foxostro/Turtle16/Hardware/Archive/MEMModule_Rev_C_1e01d7a2/MEMModule (Rev C).pdf

Id: 1/14 Title: Turtle16: MEM, RAM, ROM

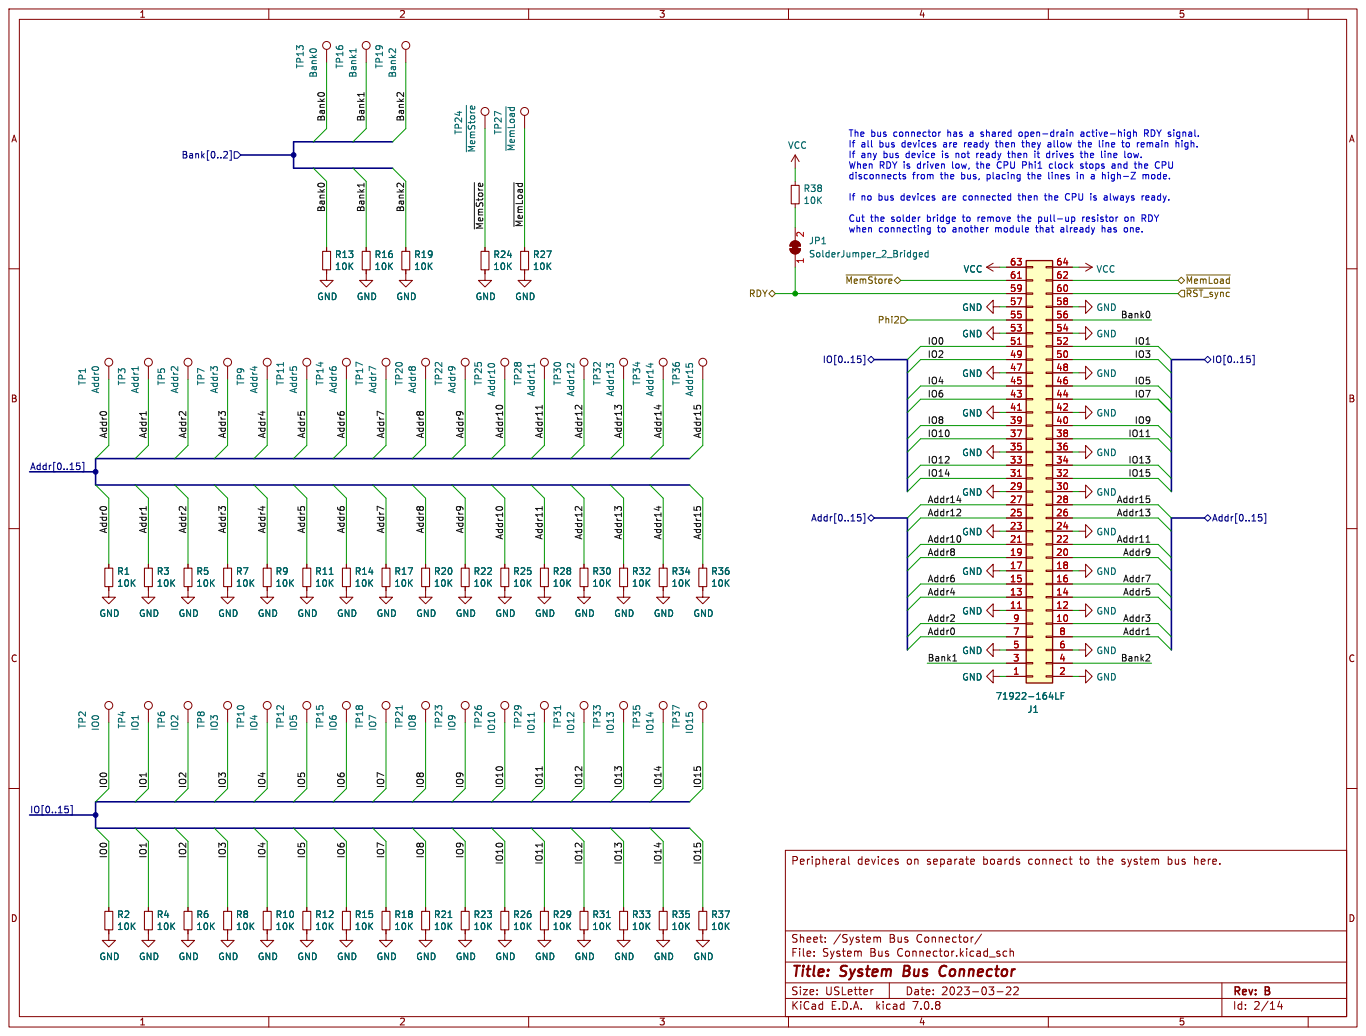
[picture p56: page 2]

If all bus devices are ready then they allow the line to remain high.
If any bus device is not ready then it drives the line low. When RDY is driven low, the CPU Phi1 clock stops and the CPU

VCC GND GND GND GND
9 GND GND GND GND

GND GND

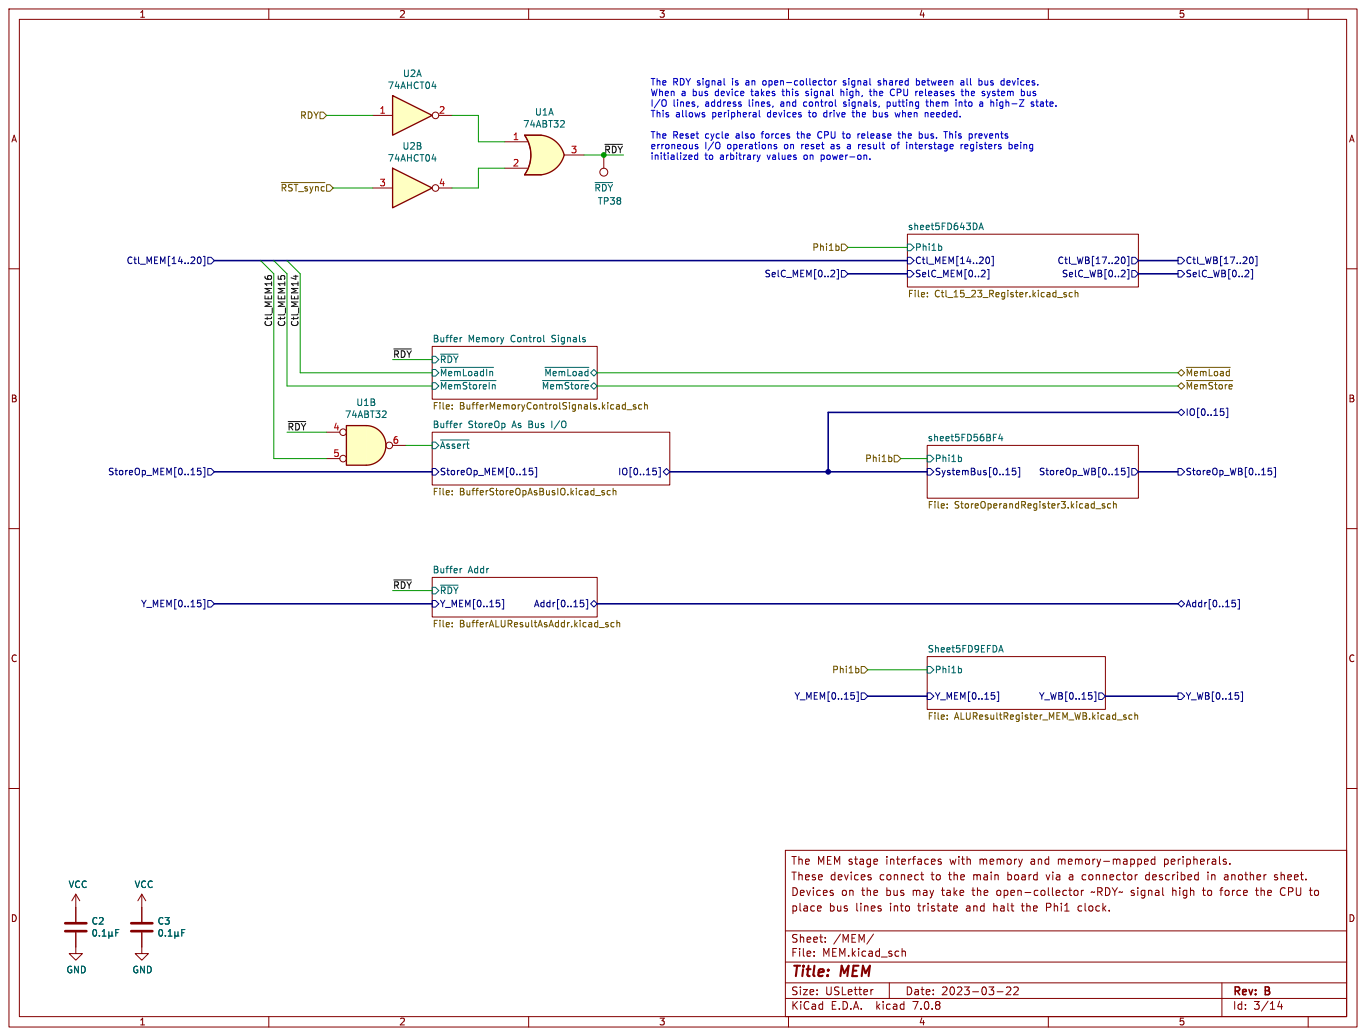
[picture p57: page 3]

~{RDY} Buffer Memory Control Signals File: BufferMemoryControlSignals.kicad_sch

~{Assert} Buffer StoreOp As Bus I/O

þÿ0.1¼F GND VCC 14 GND


74AHCT245 VCC GND GND GND


Id: 5/14 Title: MEM: Buffer StoreOp



Id: 7/14 Title: MEM/WB: Control Word Register File: Ctl_15_23_Register.kicad_sch Sheet: /MEM/sheet5FD643DA/



VCC GND VCC GND GND GND GND

If the IF stage is not being fed by ROM then it is being fed by RAM.

File: RAM.kicad_sch Sheet: /Memory/RAM/
Id: 9/14 Title: Turtle16: RAM


File: ALUResultRegister_MEM_WB.kicad_sch Sheet: /MEM/Sheet5FD9EFDA/ GND

Id: 10/14 Title: ALU Result Register MEM/WB


Id: 11/14 Title: Turtle16: MEM Prototype Inputs

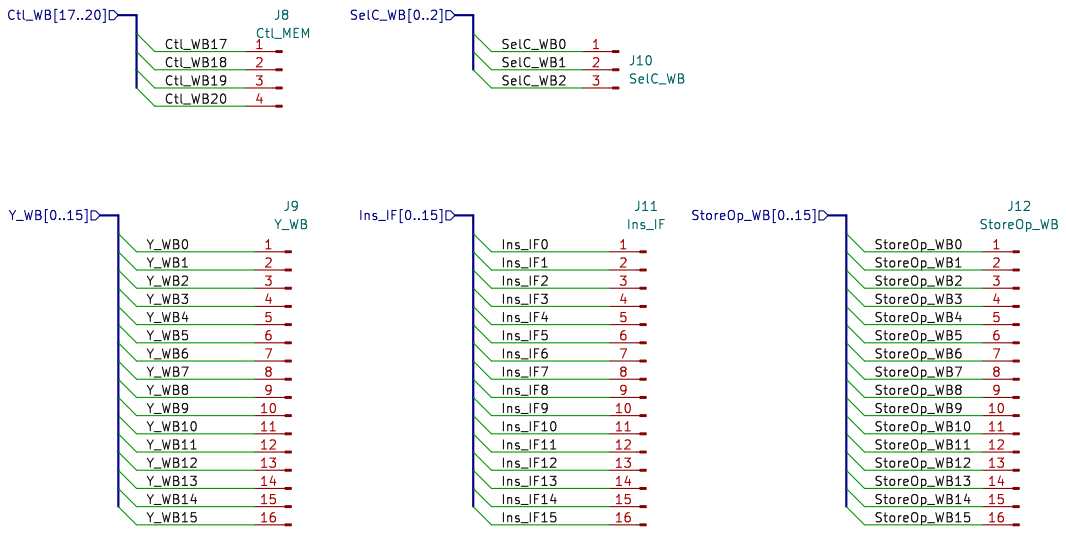
[picture p58: page 12]

Id: 12/14 Title: Turtle16: MEM Prototype Outputs

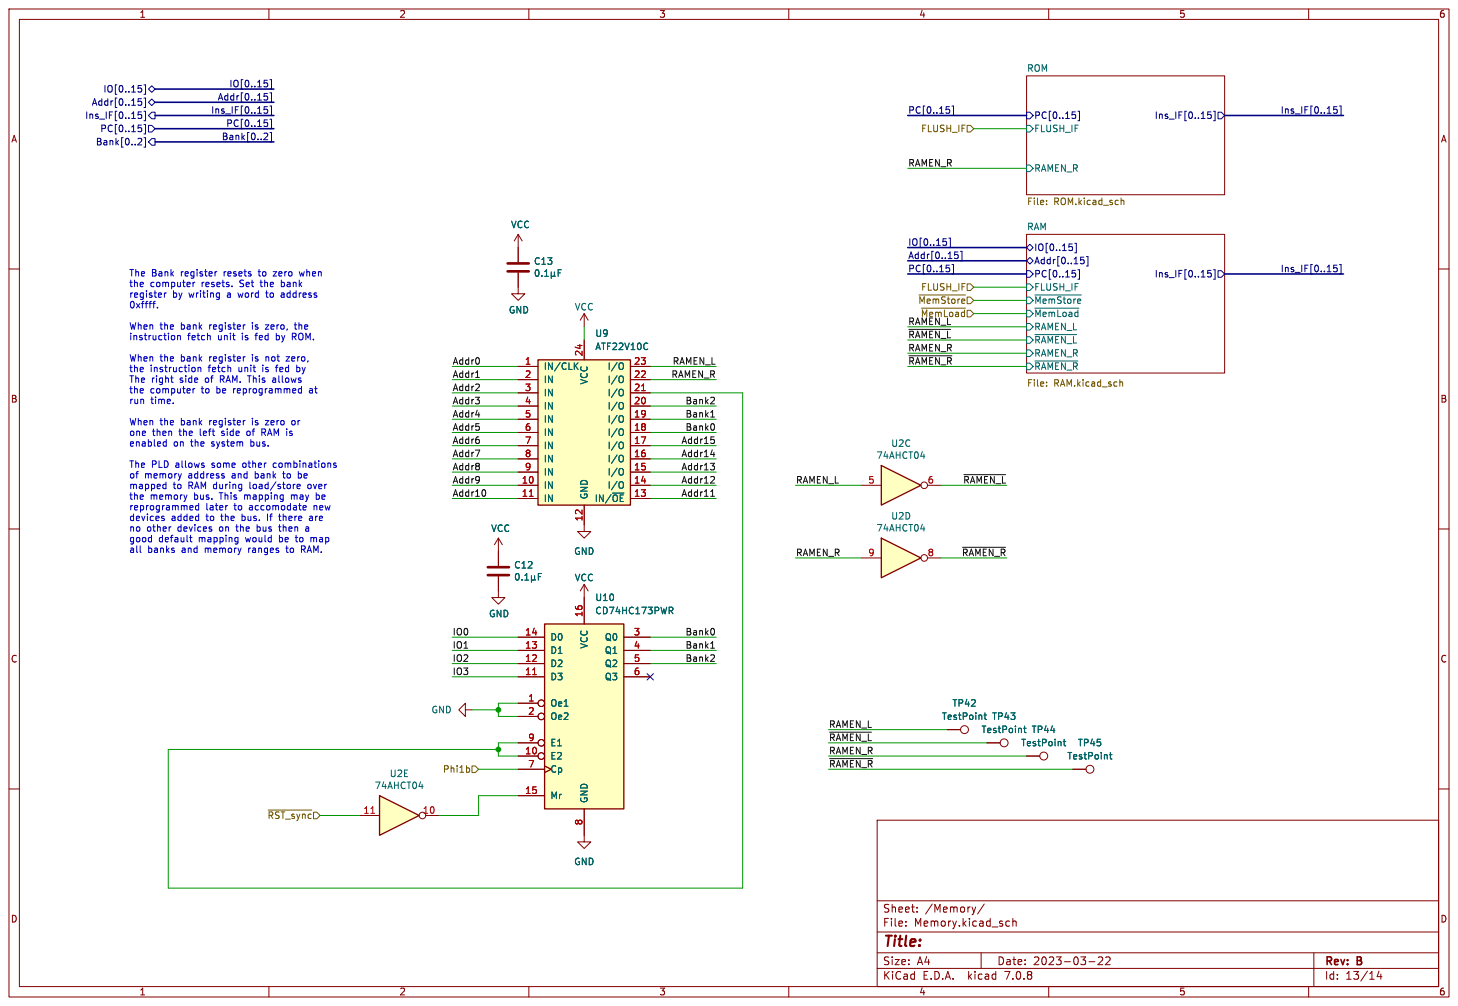
[picture p59: page 13]

8 E1 9 U10 CD74HC173PWR GND TP43 TestPoint TP42 TestPoint TP44 TestPoint TP45 TestPoint 5 6 U2C

the memory bus. This mapping may be
devices added to the bus. If there are
no other devices on the bus then a

Id: 13/14 Title: File: Memory.kicad_sch Sheet: /Memory/

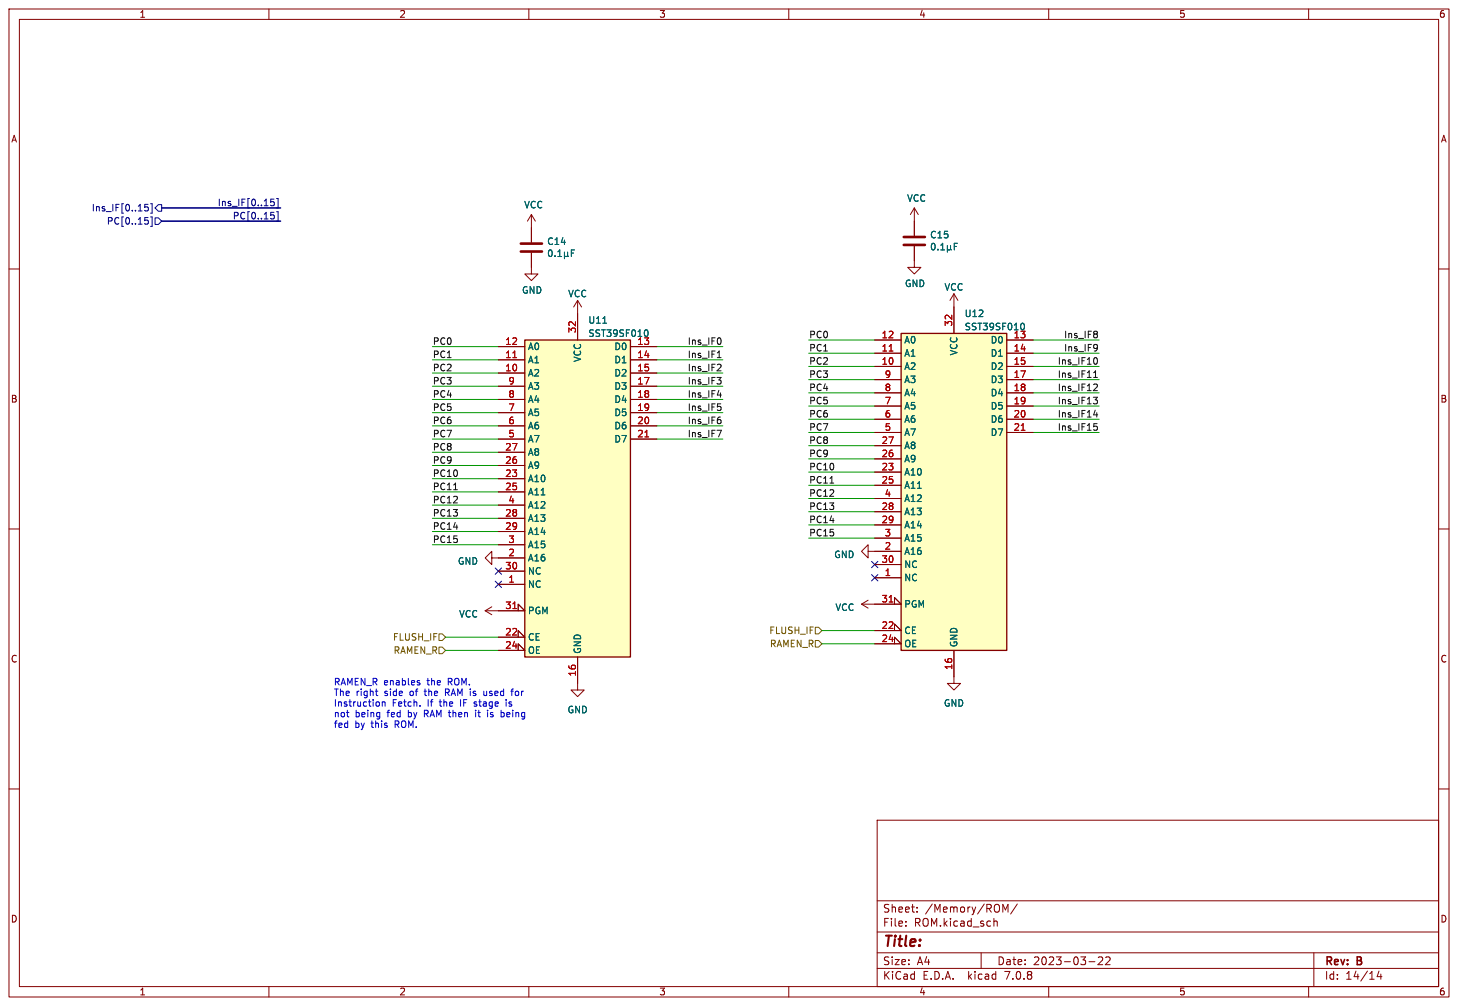
[picture p60: page 14]

fed by this ROM.

Id: 14/14 Title: File: ROM.kicad_sch Sheet: /Memory/ROM/
