foxostro/Turtle16/Hardware/PrototypeProcessor/BypassModule/BypassModule.kicad_pcb

## KiCad design Hardware/PrototypeProcessor/BypassModule/BypassModule.kicad_pcb (2025-06-30, an earlier design)

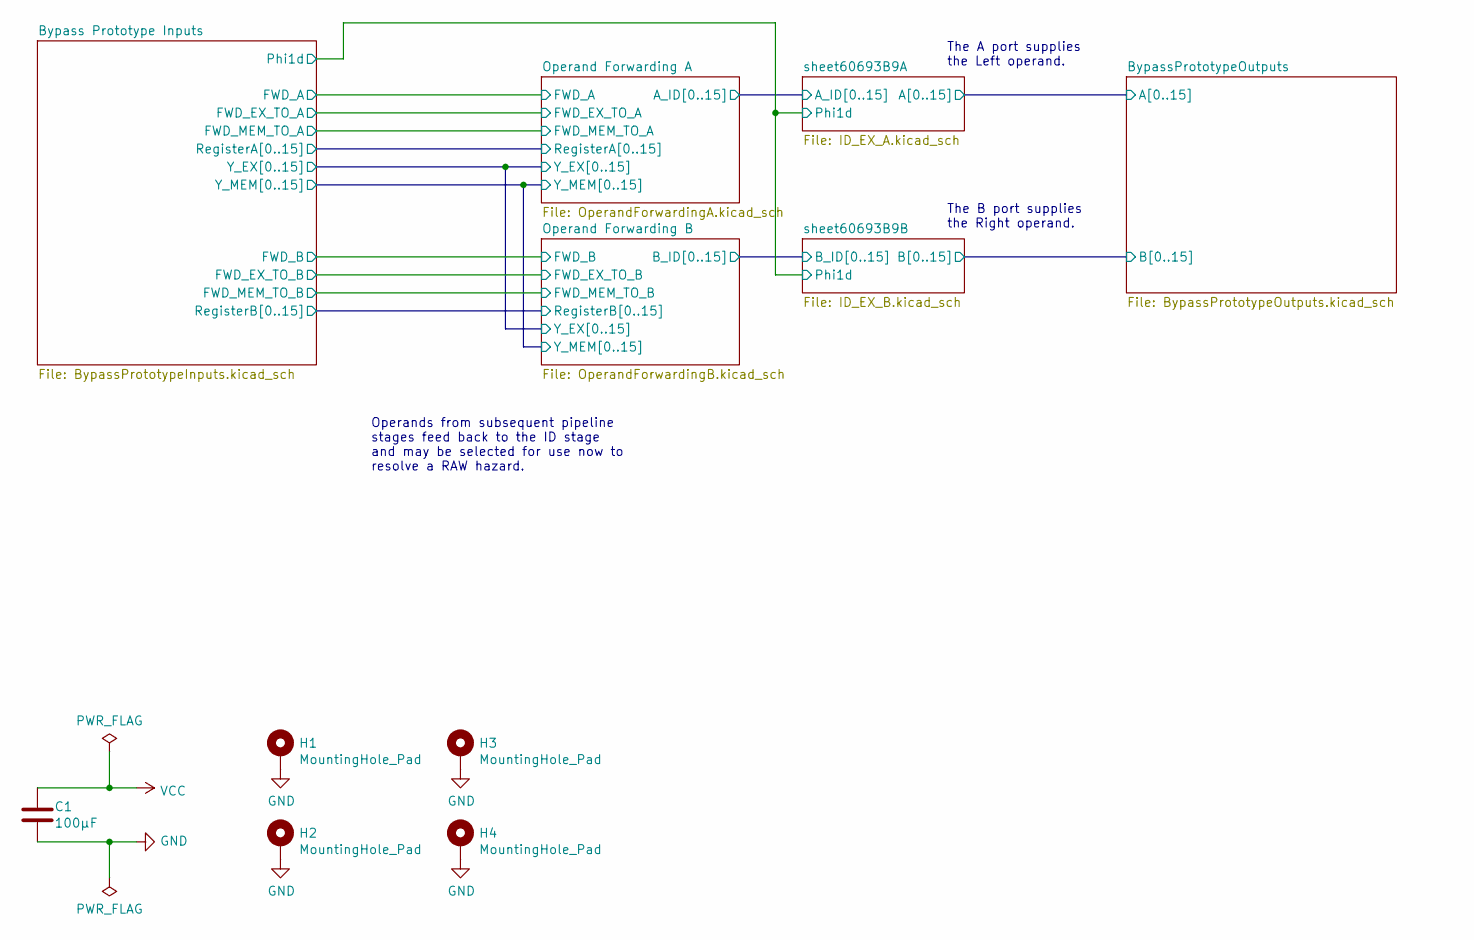
[picture p125: schematic BypassModule.kicad_sch, Turtle16: Bypass]

Parts:
C1: 100µF; C_1206_3216Metric_Pad1.33x1.80mm_HandSolder
H1, H2, H3, H4: MountingHole_Pad; MountingHole_3.2mm_M3_Pad

Connections:
GND: C1.2, H1.1, H2.1, H3.1, H4.1; also elsewhere on the board
VCC: C1.1; also elsewhere on the board

Notes on the sheet:
Operands from subsequent pipeline stages feed back to the ID stage and may be selected for use now to resolve a RAW hazard.
The B port supplies the Right operand.
The A port supplies the Left operand.

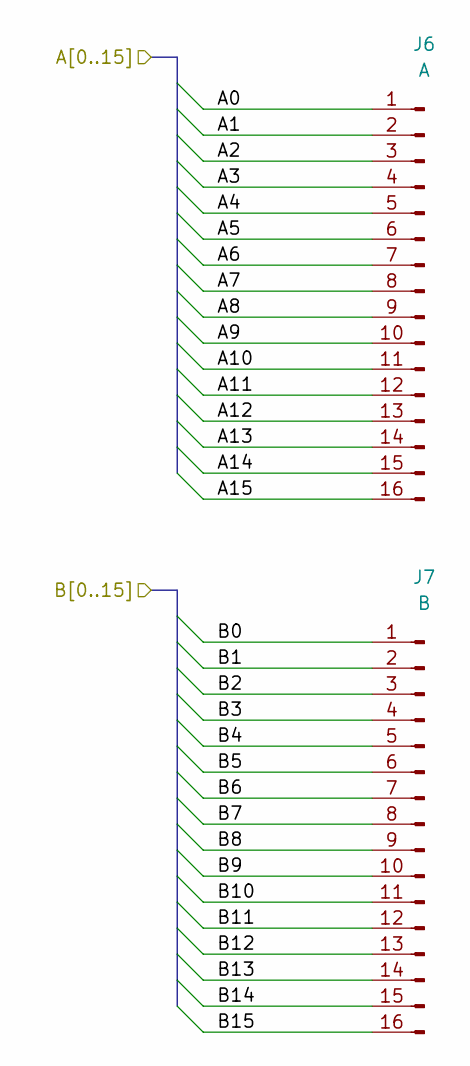
[picture p126: schematic BypassPrototypeOutputs.kicad_sch]

Parts:
J6: A; PinHeader_1x16_P2.54mm_Vertical
J7: B; PinHeader_1x16_P2.54mm_Vertical

Connections:
/BypassPrototypeOutputs/A0: J6.1; also elsewhere on the board
/BypassPrototypeOutputs/A1: J6.2; also elsewhere on the board
/BypassPrototypeOutputs/A2: J6.3; also elsewhere on the board
/BypassPrototypeOutputs/A3: J6.4; also elsewhere on the board
/BypassPrototypeOutputs/A4: J6.5; also elsewhere on the board
/BypassPrototypeOutputs/A5: J6.6; also elsewhere on the board
/BypassPrototypeOutputs/A6: J6.7; also elsewhere on the board
/BypassPrototypeOutputs/A7: J6.8; also elsewhere on the board
/BypassPrototypeOutputs/A8: J6.9; also elsewhere on the board
/BypassPrototypeOutputs/A9: J6.10; also elsewhere on the board
/BypassPrototypeOutputs/A10: J6.11; also elsewhere on the board
/BypassPrototypeOutputs/A11: J6.12; also elsewhere on the board
/BypassPrototypeOutputs/A12: J6.13; also elsewhere on the board
/BypassPrototypeOutputs/A13: J6.14; also elsewhere on the board
/BypassPrototypeOutputs/A14: J6.15; also elsewhere on the board
/BypassPrototypeOutputs/A15: J6.16; also elsewhere on the board
/BypassPrototypeOutputs/B0: J7.1; also elsewhere on the board
/BypassPrototypeOutputs/B1: J7.2; also elsewhere on the board
/BypassPrototypeOutputs/B2: J7.3; also elsewhere on the board
/BypassPrototypeOutputs/B3: J7.4; also elsewhere on the board
/BypassPrototypeOutputs/B4: J7.5; also elsewhere on the board
/BypassPrototypeOutputs/B5: J7.6; also elsewhere on the board
/BypassPrototypeOutputs/B6: J7.7; also elsewhere on the board
/BypassPrototypeOutputs/B7: J7.8; also elsewhere on the board
/BypassPrototypeOutputs/B8: J7.9; also elsewhere on the board
/BypassPrototypeOutputs/B9: J7.10; also elsewhere on the board
/BypassPrototypeOutputs/B10: J7.11; also elsewhere on the board
/BypassPrototypeOutputs/B11: J7.12; also elsewhere on the board
/BypassPrototypeOutputs/B12: J7.13; also elsewhere on the board
/BypassPrototypeOutputs/B13: J7.14; also elsewhere on the board
/BypassPrototypeOutputs/B14: J7.15; also elsewhere on the board
/BypassPrototypeOutputs/B15: J7.16; also elsewhere on the board

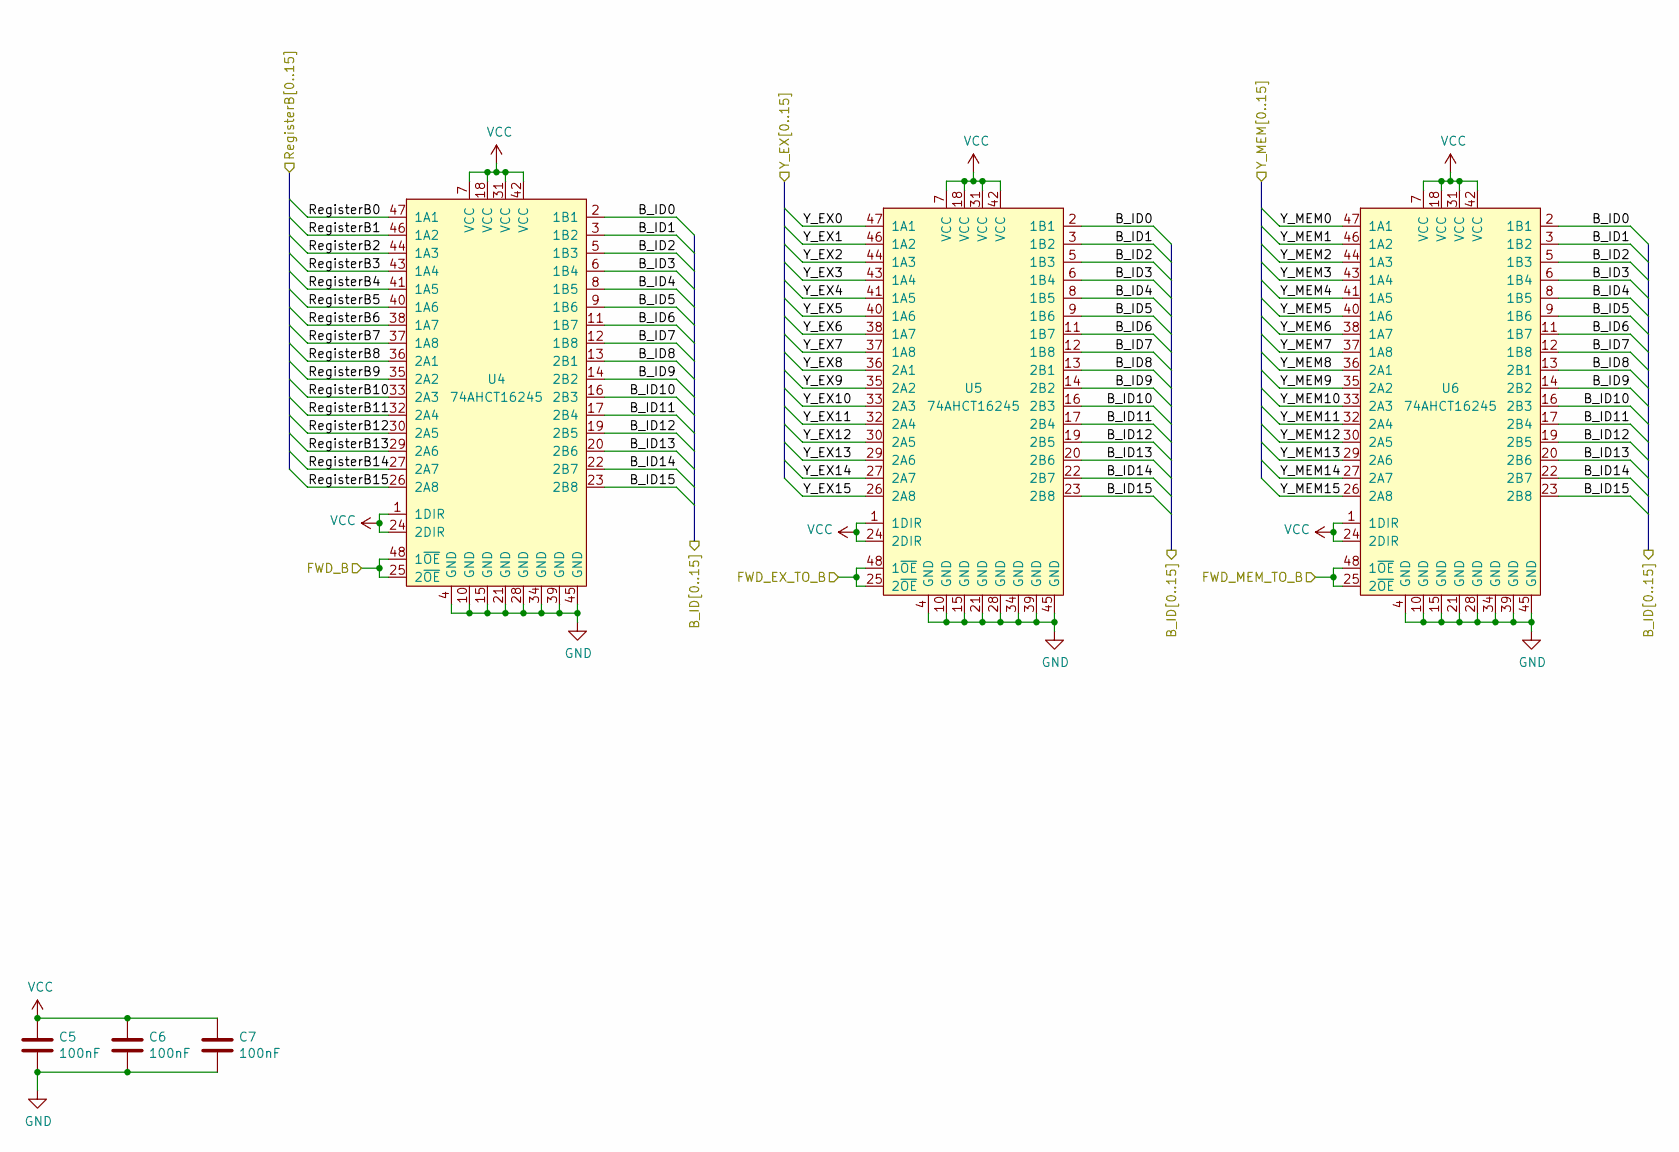
[picture p127: schematic OperandForwardingB.kicad_sch]

Parts:
C5, C6, C7: 100nF; C_0603_1608Metric_Pad1.08x0.95mm_HandSolder
U4, U5, U6: 74AHCT16245; TSSOP-48_6.1x12.5mm_P0.5mm

Connections:
/Bypass Prototype Inputs/FWD_B: U4.25 (2~OE), U4.48 (1~OE); also elsewhere on the board
/Bypass Prototype Inputs/FWD_EX_TO_B: U5.25 (2~OE), U5.48 (1~OE); also elsewhere on the board
/Bypass Prototype Inputs/FWD_MEM_TO_B: U6.25 (2~OE), U6.48 (1~OE); also elsewhere on the board
/Bypass Prototype Inputs/RegisterB0: U4.47 (1A1); also elsewhere on the board
/Bypass Prototype Inputs/RegisterB1: U4.46 (1A2); also elsewhere on the board
/Bypass Prototype Inputs/RegisterB2: U4.44 (1A3); also elsewhere on the board
/Bypass Prototype Inputs/RegisterB3: U4.43 (1A4); also elsewhere on the board
/Bypass Prototype Inputs/RegisterB4: U4.41 (1A5); also elsewhere on the board
/Bypass Prototype Inputs/RegisterB5: U4.40 (1A6); also elsewhere on the board
/Bypass Prototype Inputs/RegisterB6: U4.38 (1A7); also elsewhere on the board
/Bypass Prototype Inputs/RegisterB7: U4.37 (1A8); also elsewhere on the board
/Bypass Prototype Inputs/RegisterB8: U4.36 (2A1); also elsewhere on the board
/Bypass Prototype Inputs/RegisterB9: U4.35 (2A2); also elsewhere on the board
/Bypass Prototype Inputs/RegisterB10: U4.33 (2A3); also elsewhere on the board
/Bypass Prototype Inputs/RegisterB11: U4.32 (2A4); also elsewhere on the board
/Bypass Prototype Inputs/RegisterB12: U4.30 (2A5); also elsewhere on the board
/Bypass Prototype Inputs/RegisterB13: U4.29 (2A6); also elsewhere on the board
/Bypass Prototype Inputs/RegisterB14: U4.27 (2A7); also elsewhere on the board
/Bypass Prototype Inputs/RegisterB15: U4.26 (2A8); also elsewhere on the board
/Bypass Prototype Inputs/Y_EX0: U5.47 (1A1); also elsewhere on the board
/Bypass Prototype Inputs/Y_EX1: U5.46 (1A2); also elsewhere on the board
/Bypass Prototype Inputs/Y_EX2: U5.44 (1A3); also elsewhere on the board
/Bypass Prototype Inputs/Y_EX3: U5.43 (1A4); also elsewhere on the board
/Bypass Prototype Inputs/Y_EX4: U5.41 (1A5); also elsewhere on the board
/Bypass Prototype Inputs/Y_EX5: U5.40 (1A6); also elsewhere on the board
/Bypass Prototype Inputs/Y_EX6: U5.38 (1A7); also elsewhere on the board
/Bypass Prototype Inputs/Y_EX7: U5.37 (1A8); also elsewhere on the board
/Bypass Prototype Inputs/Y_EX8: U5.36 (2A1); also elsewhere on the board
/Bypass Prototype Inputs/Y_EX9: U5.35 (2A2); also elsewhere on the board
/Bypass Prototype Inputs/Y_EX10: U5.33 (2A3); also elsewhere on the board
/Bypass Prototype Inputs/Y_EX11: U5.32 (2A4); also elsewhere on the board
/Bypass Prototype Inputs/Y_EX12: U5.30 (2A5); also elsewhere on the board
/Bypass Prototype Inputs/Y_EX13: U5.29 (2A6); also elsewhere on the board
/Bypass Prototype Inputs/Y_EX14: U5.27 (2A7); also elsewhere on the board
/Bypass Prototype Inputs/Y_EX15: U5.26 (2A8); also elsewhere on the board
/Bypass Prototype Inputs/Y_MEM0: U6.47 (1A1); also elsewhere on the board
/Bypass Prototype Inputs/Y_MEM1: U6.46 (1A2); also elsewhere on the board
/Bypass Prototype Inputs/Y_MEM2: U6.44 (1A3); also elsewhere on the board
/Bypass Prototype Inputs/Y_MEM3: U6.43 (1A4); also elsewhere on the board
/Bypass Prototype Inputs/Y_MEM4: U6.41 (1A5); also elsewhere on the board
/Bypass Prototype Inputs/Y_MEM5: U6.40 (1A6); also elsewhere on the board
/Bypass Prototype Inputs/Y_MEM6: U6.38 (1A7); also elsewhere on the board
/Bypass Prototype Inputs/Y_MEM7: U6.37 (1A8); also elsewhere on the board
/Bypass Prototype Inputs/Y_MEM8: U6.36 (2A1); also elsewhere on the board
/Bypass Prototype Inputs/Y_MEM9: U6.35 (2A2); also elsewhere on the board
/Bypass Prototype Inputs/Y_MEM10: U6.33 (2A3); also elsewhere on the board
/Bypass Prototype Inputs/Y_MEM11: U6.32 (2A4); also elsewhere on the board
/Bypass Prototype Inputs/Y_MEM12: U6.30 (2A5); also elsewhere on the board
/Bypass Prototype Inputs/Y_MEM13: U6.29 (2A6); also elsewhere on the board
/Bypass Prototype Inputs/Y_MEM14: U6.27 (2A7); also elsewhere on the board
/Bypass Prototype Inputs/Y_MEM15: U6.26 (2A8); also elsewhere on the board
/Operand Forwarding B/B_ID0: U4.2 (1B1), U5.2 (1B1), U6.2 (1B1); also elsewhere on the board
/Operand Forwarding B/B_ID1: U4.3 (1B2), U5.3 (1B2), U6.3 (1B2); also elsewhere on the board
/Operand Forwarding B/B_ID2: U4.5 (1B3), U5.5 (1B3), U6.5 (1B3); also elsewhere on the board
/Operand Forwarding B/B_ID3: U4.6 (1B4), U5.6 (1B4), U6.6 (1B4); also elsewhere on the board
/Operand Forwarding B/B_ID4: U4.8 (1B5), U5.8 (1B5), U6.8 (1B5); also elsewhere on the board
/Operand Forwarding B/B_ID5: U4.9 (1B6), U5.9 (1B6), U6.9 (1B6); also elsewhere on the board
/Operand Forwarding B/B_ID6: U4.11 (1B7), U5.11 (1B7), U6.11 (1B7); also elsewhere on the board
/Operand Forwarding B/B_ID7: U4.12 (1B8), U5.12 (1B8), U6.12 (1B8); also elsewhere on the board
/Operand Forwarding B/B_ID8: U4.13 (2B1), U5.13 (2B1), U6.13 (2B1); also elsewhere on the board
/Operand Forwarding B/B_ID9: U4.14 (2B2), U5.14 (2B2), U6.14 (2B2); also elsewhere on the board
/Operand Forwarding B/B_ID10: U4.16 (2B3), U5.16 (2B3), U6.16 (2B3); also elsewhere on the board
/Operand Forwarding B/B_ID11: U4.17 (2B4), U5.17 (2B4), U6.17 (2B4); also elsewhere on the board
/Operand Forwarding B/B_ID12: U4.19 (2B5), U5.19 (2B5), U6.19 (2B5); also elsewhere on the board
/Operand Forwarding B/B_ID13: U4.20 (2B6), U5.20 (2B6), U6.20 (2B6); also elsewhere on the board
/Operand Forwarding B/B_ID14: U4.22 (2B7), U5.22 (2B7), U6.22 (2B7); also elsewhere on the board
/Operand Forwarding B/B_ID15: U4.23 (2B8), U5.23 (2B8), U6.23 (2B8); also elsewhere on the board
GND: C5.2, C6.2, C7.2, U4.4 (GND), U4.10 (GND), U4.15 (GND), U4.21 (GND), U4.28 (GND), U4.34 (GND), U4.39 (GND), U4.45 (GND), U5.4 (GND), U5.10 (GND), U5.15 (GND), U5.21 (GND), U5.28 (GND), U5.34 (GND), U5.39 (GND), U5.45 (GND), U6.4 (GND), U6.10 (GND), U6.15 (GND), U6.21 (GND), U6.28 (GND), U6.34 (GND), U6.39 (GND), U6.45 (GND); also elsewhere on the board
VCC: C5.1, C6.1, C7.1, U4.1 (1DIR), U4.7 (VCC), U4.18 (VCC), U4.24 (2DIR), U4.31 (VCC), U4.42 (VCC), U5.1 (1DIR), U5.7 (VCC), U5.18 (VCC), U5.24 (2DIR), U5.31 (VCC), U5.42 (VCC), U6.1 (1DIR), U6.7 (VCC), U6.18 (VCC), U6.24 (2DIR), U6.31 (VCC), U6.42 (VCC); also elsewhere on the board

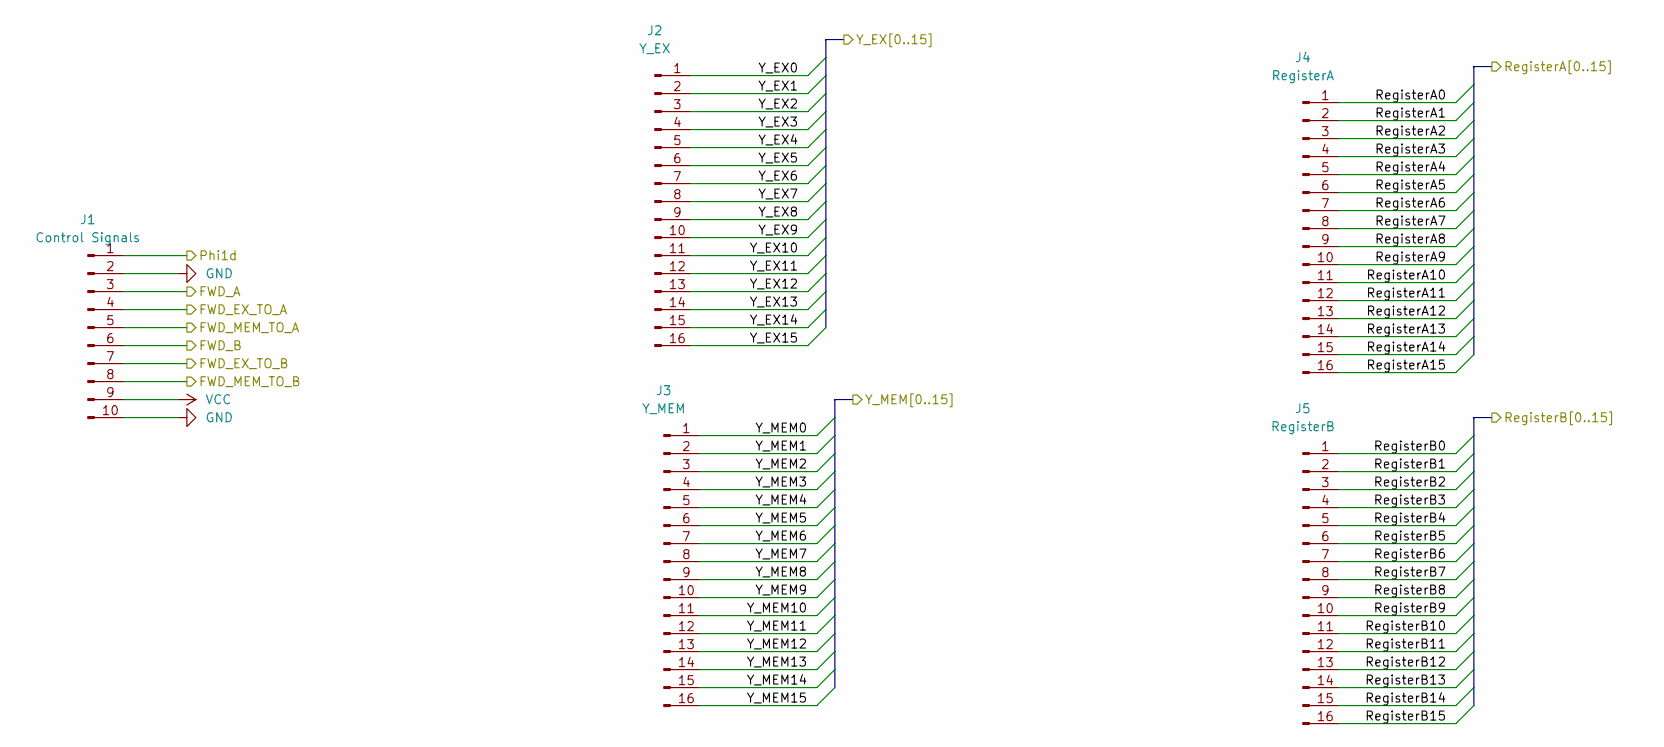
[picture p128: schematic BypassPrototypeInputs.kicad_sch]

Parts:
J1: Control Signals; PinHeader_1x10_P2.54mm_Vertical
J2: Y_EX; PinHeader_1x16_P2.54mm_Vertical
J3: Y_MEM; PinHeader_1x16_P2.54mm_Vertical
J4: RegisterA; PinHeader_1x16_P2.54mm_Vertical
J5: RegisterB; PinHeader_1x16_P2.54mm_Vertical

Connections:
/Bypass Prototype Inputs/FWD_A: J1.3; also elsewhere on the board
/Bypass Prototype Inputs/FWD_B: J1.6; also elsewhere on the board
/Bypass Prototype Inputs/FWD_EX_TO_A: J1.4; also elsewhere on the board
/Bypass Prototype Inputs/FWD_EX_TO_B: J1.7; also elsewhere on the board
/Bypass Prototype Inputs/FWD_MEM_TO_A: J1.5; also elsewhere on the board
/Bypass Prototype Inputs/FWD_MEM_TO_B: J1.8; also elsewhere on the board
/Bypass Prototype Inputs/Phi1d: J1.1; also elsewhere on the board
/Bypass Prototype Inputs/RegisterA0: J4.1; also elsewhere on the board
/Bypass Prototype Inputs/RegisterA1: J4.2; also elsewhere on the board
/Bypass Prototype Inputs/RegisterA2: J4.3; also elsewhere on the board
/Bypass Prototype Inputs/RegisterA3: J4.4; also elsewhere on the board
/Bypass Prototype Inputs/RegisterA4: J4.5; also elsewhere on the board
/Bypass Prototype Inputs/RegisterA5: J4.6; also elsewhere on the board
/Bypass Prototype Inputs/RegisterA6: J4.7; also elsewhere on the board
/Bypass Prototype Inputs/RegisterA7: J4.8; also elsewhere on the board
/Bypass Prototype Inputs/RegisterA8: J4.9; also elsewhere on the board
/Bypass Prototype Inputs/RegisterA9: J4.10; also elsewhere on the board
/Bypass Prototype Inputs/RegisterA10: J4.11; also elsewhere on the board
/Bypass Prototype Inputs/RegisterA11: J4.12; also elsewhere on the board
/Bypass Prototype Inputs/RegisterA12: J4.13; also elsewhere on the board
/Bypass Prototype Inputs/RegisterA13: J4.14; also elsewhere on the board
/Bypass Prototype Inputs/RegisterA14: J4.15; also elsewhere on the board
/Bypass Prototype Inputs/RegisterA15: J4.16; also elsewhere on the board
/Bypass Prototype Inputs/RegisterB0: J5.1; also elsewhere on the board
/Bypass Prototype Inputs/RegisterB1: J5.2; also elsewhere on the board
/Bypass Prototype Inputs/RegisterB2: J5.3; also elsewhere on the board
/Bypass Prototype Inputs/RegisterB3: J5.4; also elsewhere on the board
/Bypass Prototype Inputs/RegisterB4: J5.5; also elsewhere on the board
/Bypass Prototype Inputs/RegisterB5: J5.6; also elsewhere on the board
/Bypass Prototype Inputs/RegisterB6: J5.7; also elsewhere on the board
/Bypass Prototype Inputs/RegisterB7: J5.8; also elsewhere on the board
/Bypass Prototype Inputs/RegisterB8: J5.9; also elsewhere on the board
/Bypass Prototype Inputs/RegisterB9: J5.10; also elsewhere on the board
/Bypass Prototype Inputs/RegisterB10: J5.11; also elsewhere on the board
/Bypass Prototype Inputs/RegisterB11: J5.12; also elsewhere on the board
/Bypass Prototype Inputs/RegisterB12: J5.13; also elsewhere on the board
/Bypass Prototype Inputs/RegisterB13: J5.14; also elsewhere on the board
/Bypass Prototype Inputs/RegisterB14: J5.15; also elsewhere on the board
/Bypass Prototype Inputs/RegisterB15: J5.16; also elsewhere on the board
/Bypass Prototype Inputs/Y_EX0: J2.1; also elsewhere on the board
/Bypass Prototype Inputs/Y_EX1: J2.2; also elsewhere on the board
/Bypass Prototype Inputs/Y_EX2: J2.3; also elsewhere on the board
/Bypass Prototype Inputs/Y_EX3: J2.4; also elsewhere on the board
/Bypass Prototype Inputs/Y_EX4: J2.5; also elsewhere on the board
/Bypass Prototype Inputs/Y_EX5: J2.6; also elsewhere on the board
/Bypass Prototype Inputs/Y_EX6: J2.7; also elsewhere on the board
/Bypass Prototype Inputs/Y_EX7: J2.8; also elsewhere on the board
/Bypass Prototype Inputs/Y_EX8: J2.9; also elsewhere on the board
/Bypass Prototype Inputs/Y_EX9: J2.10; also elsewhere on the board
/Bypass Prototype Inputs/Y_EX10: J2.11; also elsewhere on the board
/Bypass Prototype Inputs/Y_EX11: J2.12; also elsewhere on the board
/Bypass Prototype Inputs/Y_EX12: J2.13; also elsewhere on the board
/Bypass Prototype Inputs/Y_EX13: J2.14; also elsewhere on the board
/Bypass Prototype Inputs/Y_EX14: J2.15; also elsewhere on the board
/Bypass Prototype Inputs/Y_EX15: J2.16; also elsewhere on the board
/Bypass Prototype Inputs/Y_MEM0: J3.1; also elsewhere on the board
/Bypass Prototype Inputs/Y_MEM1: J3.2; also elsewhere on the board
/Bypass Prototype Inputs/Y_MEM2: J3.3; also elsewhere on the board
/Bypass Prototype Inputs/Y_MEM3: J3.4; also elsewhere on the board
/Bypass Prototype Inputs/Y_MEM4: J3.5; also elsewhere on the board
/Bypass Prototype Inputs/Y_MEM5: J3.6; also elsewhere on the board
/Bypass Prototype Inputs/Y_MEM6: J3.7; also elsewhere on the board
/Bypass Prototype Inputs/Y_MEM7: J3.8; also elsewhere on the board
/Bypass Prototype Inputs/Y_MEM8: J3.9; also elsewhere on the board
/Bypass Prototype Inputs/Y_MEM9: J3.10; also elsewhere on the board
/Bypass Prototype Inputs/Y_MEM10: J3.11; also elsewhere on the board
/Bypass Prototype Inputs/Y_MEM11: J3.12; also elsewhere on the board
/Bypass Prototype Inputs/Y_MEM12: J3.13; also elsewhere on the board
/Bypass Prototype Inputs/Y_MEM13: J3.14; also elsewhere on the board
/Bypass Prototype Inputs/Y_MEM14: J3.15; also elsewhere on the board
/Bypass Prototype Inputs/Y_MEM15: J3.16; also elsewhere on the board
GND: J1.2, J1.10; also elsewhere on the board
VCC: J1.9; also elsewhere on the board

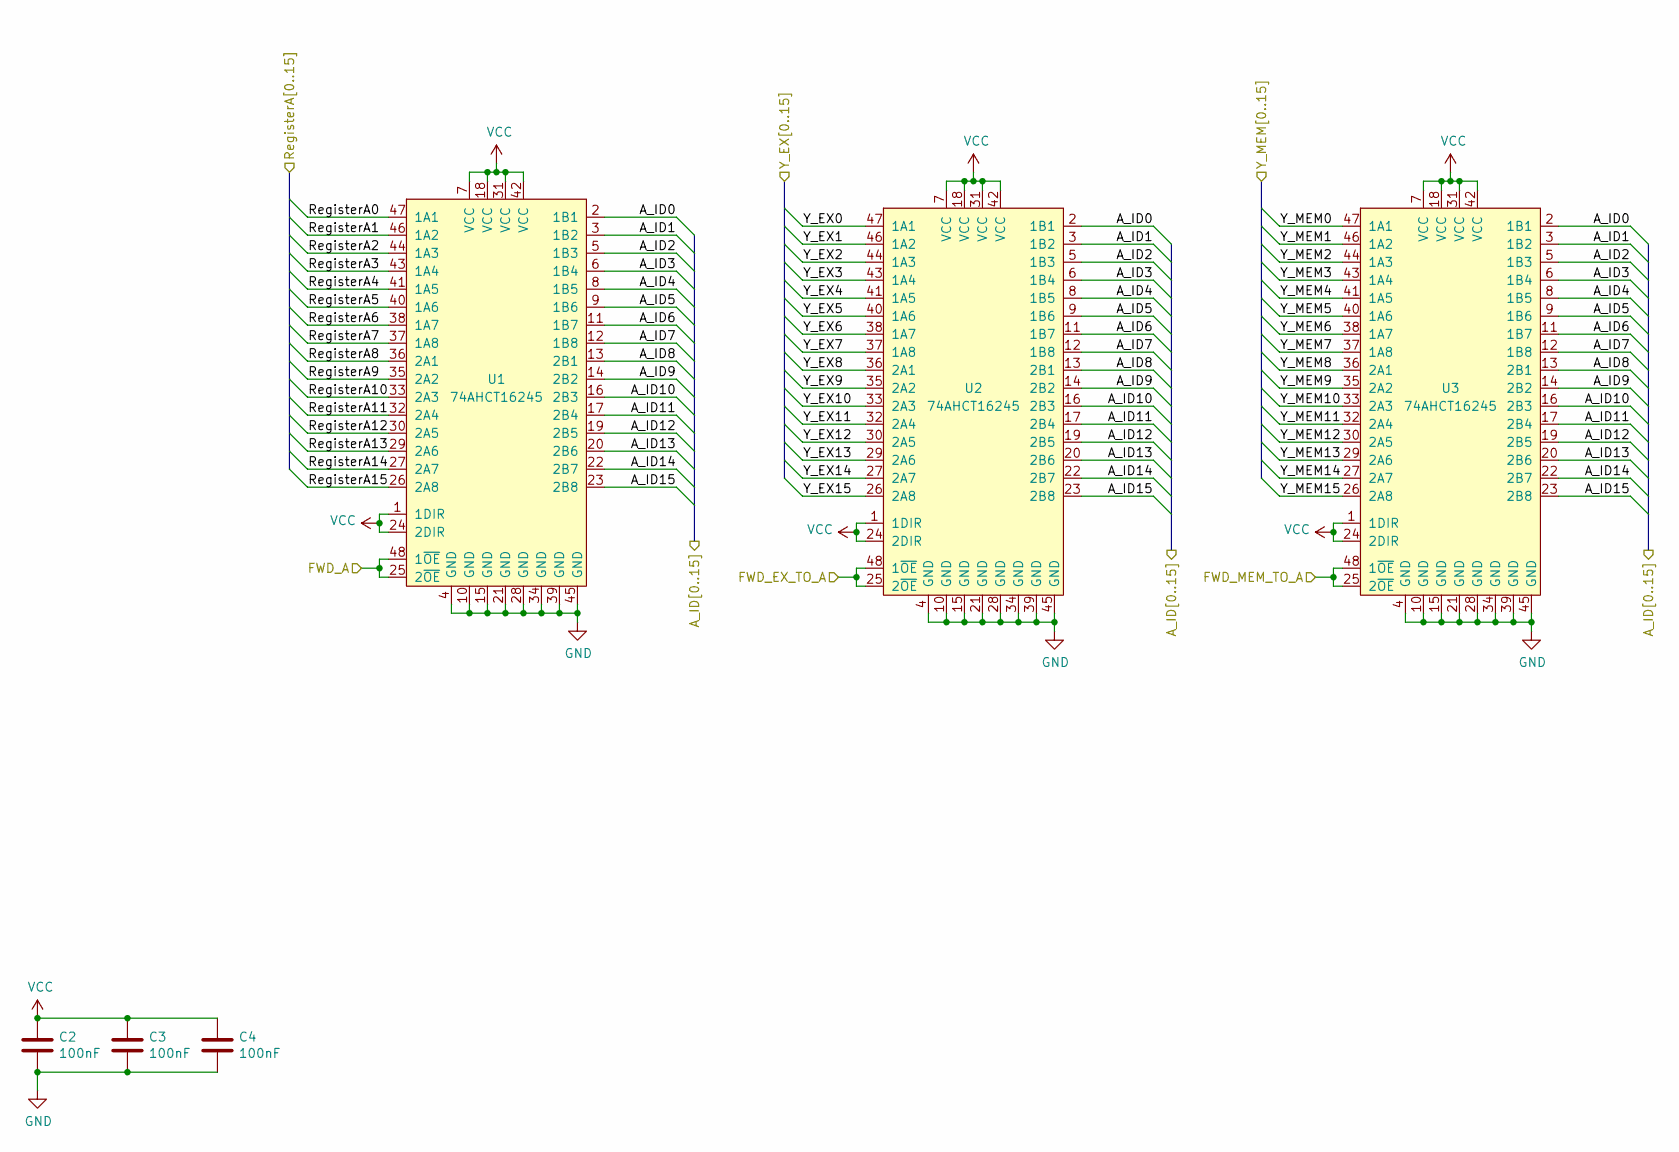
[picture p129: schematic OperandForwardingA.kicad_sch]

Parts:
C2, C3, C4: 100nF; C_0603_1608Metric_Pad1.08x0.95mm_HandSolder
U1, U2, U3: 74AHCT16245; TSSOP-48_6.1x12.5mm_P0.5mm

Connections:
/Bypass Prototype Inputs/FWD_A: U1.25 (2~OE), U1.48 (1~OE); also elsewhere on the board
/Bypass Prototype Inputs/FWD_EX_TO_A: U2.25 (2~OE), U2.48 (1~OE); also elsewhere on the board
/Bypass Prototype Inputs/FWD_MEM_TO_A: U3.25 (2~OE), U3.48 (1~OE); also elsewhere on the board
/Bypass Prototype Inputs/RegisterA0: U1.47 (1A1); also elsewhere on the board
/Bypass Prototype Inputs/RegisterA1: U1.46 (1A2); also elsewhere on the board
/Bypass Prototype Inputs/RegisterA2: U1.44 (1A3); also elsewhere on the board
/Bypass Prototype Inputs/RegisterA3: U1.43 (1A4); also elsewhere on the board
/Bypass Prototype Inputs/RegisterA4: U1.41 (1A5); also elsewhere on the board
/Bypass Prototype Inputs/RegisterA5: U1.40 (1A6); also elsewhere on the board
/Bypass Prototype Inputs/RegisterA6: U1.38 (1A7); also elsewhere on the board
/Bypass Prototype Inputs/RegisterA7: U1.37 (1A8); also elsewhere on the board
/Bypass Prototype Inputs/RegisterA8: U1.36 (2A1); also elsewhere on the board
/Bypass Prototype Inputs/RegisterA9: U1.35 (2A2); also elsewhere on the board
/Bypass Prototype Inputs/RegisterA10: U1.33 (2A3); also elsewhere on the board
/Bypass Prototype Inputs/RegisterA11: U1.32 (2A4); also elsewhere on the board
/Bypass Prototype Inputs/RegisterA12: U1.30 (2A5); also elsewhere on the board
/Bypass Prototype Inputs/RegisterA13: U1.29 (2A6); also elsewhere on the board
/Bypass Prototype Inputs/RegisterA14: U1.27 (2A7); also elsewhere on the board
/Bypass Prototype Inputs/RegisterA15: U1.26 (2A8); also elsewhere on the board
/Bypass Prototype Inputs/Y_EX0: U2.47 (1A1); also elsewhere on the board
/Bypass Prototype Inputs/Y_EX1: U2.46 (1A2); also elsewhere on the board
/Bypass Prototype Inputs/Y_EX2: U2.44 (1A3); also elsewhere on the board
/Bypass Prototype Inputs/Y_EX3: U2.43 (1A4); also elsewhere on the board
/Bypass Prototype Inputs/Y_EX4: U2.41 (1A5); also elsewhere on the board
/Bypass Prototype Inputs/Y_EX5: U2.40 (1A6); also elsewhere on the board
/Bypass Prototype Inputs/Y_EX6: U2.38 (1A7); also elsewhere on the board
/Bypass Prototype Inputs/Y_EX7: U2.37 (1A8); also elsewhere on the board
/Bypass Prototype Inputs/Y_EX8: U2.36 (2A1); also elsewhere on the board
/Bypass Prototype Inputs/Y_EX9: U2.35 (2A2); also elsewhere on the board
/Bypass Prototype Inputs/Y_EX10: U2.33 (2A3); also elsewhere on the board
/Bypass Prototype Inputs/Y_EX11: U2.32 (2A4); also elsewhere on the board
/Bypass Prototype Inputs/Y_EX12: U2.30 (2A5); also elsewhere on the board
/Bypass Prototype Inputs/Y_EX13: U2.29 (2A6); also elsewhere on the board
/Bypass Prototype Inputs/Y_EX14: U2.27 (2A7); also elsewhere on the board
/Bypass Prototype Inputs/Y_EX15: U2.26 (2A8); also elsewhere on the board
/Bypass Prototype Inputs/Y_MEM0: U3.47 (1A1); also elsewhere on the board
/Bypass Prototype Inputs/Y_MEM1: U3.46 (1A2); also elsewhere on the board
/Bypass Prototype Inputs/Y_MEM2: U3.44 (1A3); also elsewhere on the board
/Bypass Prototype Inputs/Y_MEM3: U3.43 (1A4); also elsewhere on the board
/Bypass Prototype Inputs/Y_MEM4: U3.41 (1A5); also elsewhere on the board
/Bypass Prototype Inputs/Y_MEM5: U3.40 (1A6); also elsewhere on the board
/Bypass Prototype Inputs/Y_MEM6: U3.38 (1A7); also elsewhere on the board
/Bypass Prototype Inputs/Y_MEM7: U3.37 (1A8); also elsewhere on the board
/Bypass Prototype Inputs/Y_MEM8: U3.36 (2A1); also elsewhere on the board
/Bypass Prototype Inputs/Y_MEM9: U3.35 (2A2); also elsewhere on the board
/Bypass Prototype Inputs/Y_MEM10: U3.33 (2A3); also elsewhere on the board
/Bypass Prototype Inputs/Y_MEM11: U3.32 (2A4); also elsewhere on the board
/Bypass Prototype Inputs/Y_MEM12: U3.30 (2A5); also elsewhere on the board
/Bypass Prototype Inputs/Y_MEM13: U3.29 (2A6); also elsewhere on the board
/Bypass Prototype Inputs/Y_MEM14: U3.27 (2A7); also elsewhere on the board
/Bypass Prototype Inputs/Y_MEM15: U3.26 (2A8); also elsewhere on the board
/Operand Forwarding A/A_ID0: U1.2 (1B1), U2.2 (1B1), U3.2 (1B1); also elsewhere on the board
/Operand Forwarding A/A_ID1: U1.3 (1B2), U2.3 (1B2), U3.3 (1B2); also elsewhere on the board
/Operand Forwarding A/A_ID2: U1.5 (1B3), U2.5 (1B3), U3.5 (1B3); also elsewhere on the board
/Operand Forwarding A/A_ID3: U1.6 (1B4), U2.6 (1B4), U3.6 (1B4); also elsewhere on the board
/Operand Forwarding A/A_ID4: U1.8 (1B5), U2.8 (1B5), U3.8 (1B5); also elsewhere on the board
/Operand Forwarding A/A_ID5: U1.9 (1B6), U2.9 (1B6), U3.9 (1B6); also elsewhere on the board
/Operand Forwarding A/A_ID6: U1.11 (1B7), U2.11 (1B7), U3.11 (1B7); also elsewhere on the board
/Operand Forwarding A/A_ID7: U1.12 (1B8), U2.12 (1B8), U3.12 (1B8); also elsewhere on the board
/Operand Forwarding A/A_ID8: U1.13 (2B1), U2.13 (2B1), U3.13 (2B1); also elsewhere on the board
/Operand Forwarding A/A_ID9: U1.14 (2B2), U2.14 (2B2), U3.14 (2B2); also elsewhere on the board
/Operand Forwarding A/A_ID10: U1.16 (2B3), U2.16 (2B3), U3.16 (2B3); also elsewhere on the board
/Operand Forwarding A/A_ID11: U1.17 (2B4), U2.17 (2B4), U3.17 (2B4); also elsewhere on the board
/Operand Forwarding A/A_ID12: U1.19 (2B5), U2.19 (2B5), U3.19 (2B5); also elsewhere on the board
/Operand Forwarding A/A_ID13: U1.20 (2B6), U2.20 (2B6), U3.20 (2B6); also elsewhere on the board
/Operand Forwarding A/A_ID14: U1.22 (2B7), U2.22 (2B7), U3.22 (2B7); also elsewhere on the board
/Operand Forwarding A/A_ID15: U1.23 (2B8), U2.23 (2B8), U3.23 (2B8); also elsewhere on the board
GND: C2.2, C3.2, C4.2, U1.4 (GND), U1.10 (GND), U1.15 (GND), U1.21 (GND), U1.28 (GND), U1.34 (GND), U1.39 (GND), U1.45 (GND), U2.4 (GND), U2.10 (GND), U2.15 (GND), U2.21 (GND), U2.28 (GND), U2.34 (GND), U2.39 (GND), U2.45 (GND), U3.4 (GND), U3.10 (GND), U3.15 (GND), U3.21 (GND), U3.28 (GND), U3.34 (GND), U3.39 (GND), U3.45 (GND); also elsewhere on the board
VCC: C2.1, C3.1, C4.1, U1.1 (1DIR), U1.7 (VCC), U1.18 (VCC), U1.24 (2DIR), U1.31 (VCC), U1.42 (VCC), U2.1 (1DIR), U2.7 (VCC), U2.18 (VCC), U2.24 (2DIR), U2.31 (VCC), U2.42 (VCC), U3.1 (1DIR), U3.7 (VCC), U3.18 (VCC), U3.24 (2DIR), U3.31 (VCC), U3.42 (VCC); also elsewhere on the board

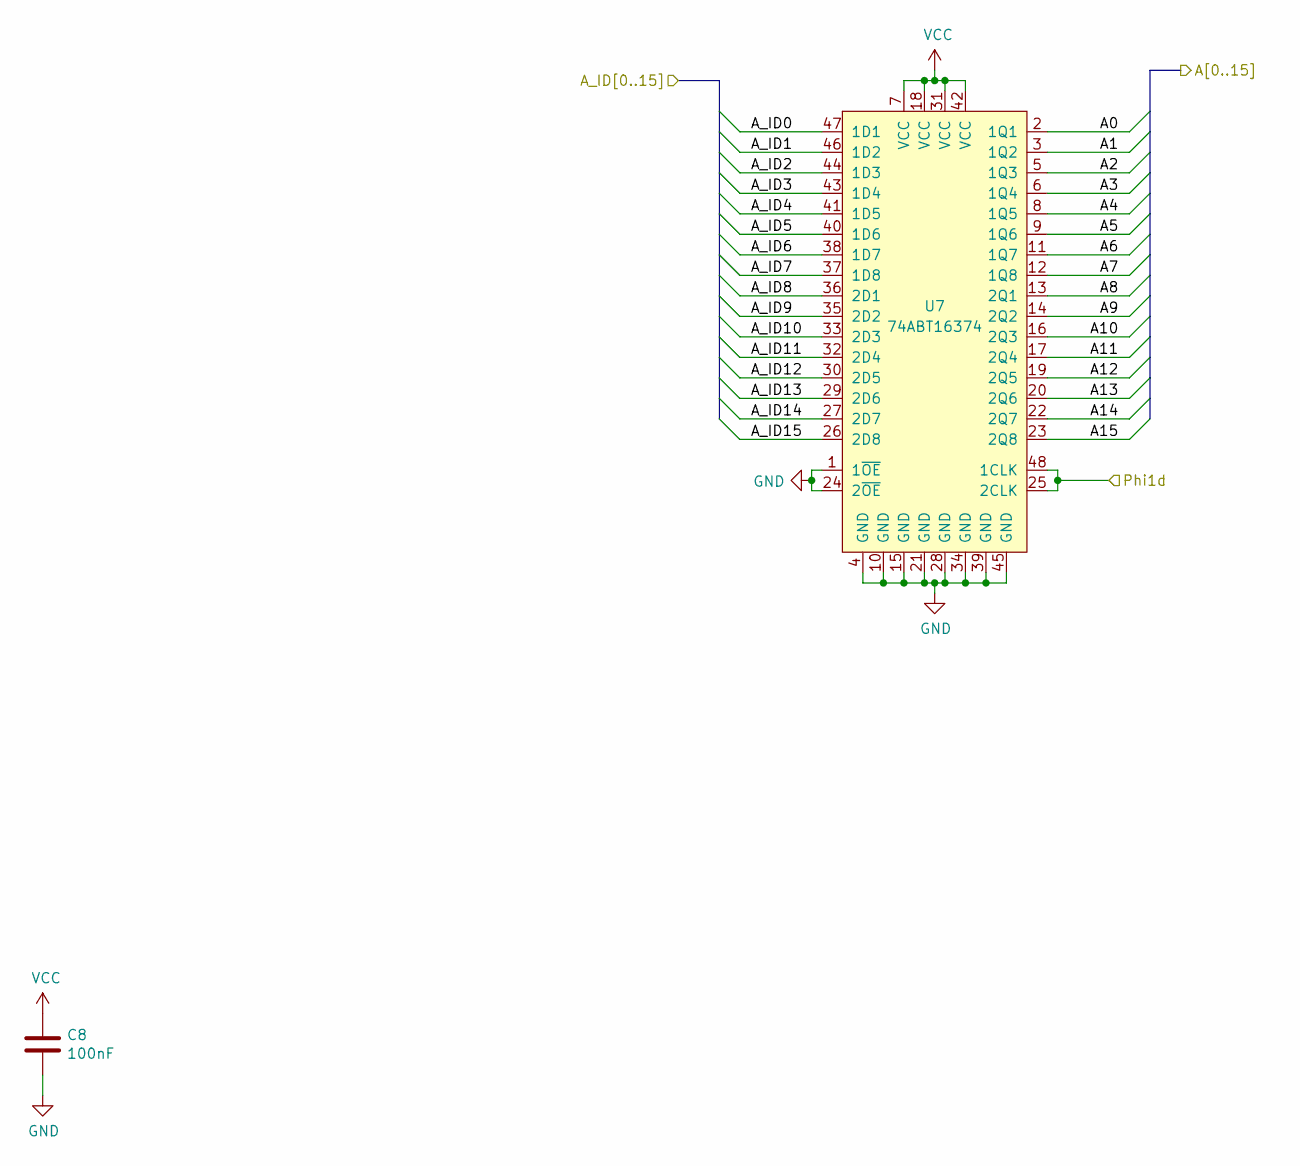
[picture p130: schematic ID_EX_A.kicad_sch]

Parts:
C8: 100nF; C_0603_1608Metric_Pad1.08x0.95mm_HandSolder
U7: 74ABT16374; TSSOP-48_6.1x12.5mm_P0.5mm

Connections:
/Bypass Prototype Inputs/Phi1d: U7.25 (2CLK), U7.48 (1CLK); also elsewhere on the board
/BypassPrototypeOutputs/A0: U7.2 (1Q1); also elsewhere on the board
/BypassPrototypeOutputs/A1: U7.3 (1Q2); also elsewhere on the board
/BypassPrototypeOutputs/A2: U7.5 (1Q3); also elsewhere on the board
/BypassPrototypeOutputs/A3: U7.6 (1Q4); also elsewhere on the board
/BypassPrototypeOutputs/A4: U7.8 (1Q5); also elsewhere on the board
/BypassPrototypeOutputs/A5: U7.9 (1Q6); also elsewhere on the board
/BypassPrototypeOutputs/A6: U7.11 (1Q7); also elsewhere on the board
/BypassPrototypeOutputs/A7: U7.12 (1Q8); also elsewhere on the board
/BypassPrototypeOutputs/A8: U7.13 (2Q1); also elsewhere on the board
/BypassPrototypeOutputs/A9: U7.14 (2Q2); also elsewhere on the board
/BypassPrototypeOutputs/A10: U7.16 (2Q3); also elsewhere on the board
/BypassPrototypeOutputs/A11: U7.17 (2Q4); also elsewhere on the board
/BypassPrototypeOutputs/A12: U7.19 (2Q5); also elsewhere on the board
/BypassPrototypeOutputs/A13: U7.20 (2Q6); also elsewhere on the board
/BypassPrototypeOutputs/A14: U7.22 (2Q7); also elsewhere on the board
/BypassPrototypeOutputs/A15: U7.23 (2Q8); also elsewhere on the board
/Operand Forwarding A/A_ID0: U7.47 (1D1); also elsewhere on the board
/Operand Forwarding A/A_ID1: U7.46 (1D2); also elsewhere on the board
/Operand Forwarding A/A_ID2: U7.44 (1D3); also elsewhere on the board
/Operand Forwarding A/A_ID3: U7.43 (1D4); also elsewhere on the board
/Operand Forwarding A/A_ID4: U7.41 (1D5); also elsewhere on the board
/Operand Forwarding A/A_ID5: U7.40 (1D6); also elsewhere on the board
/Operand Forwarding A/A_ID6: U7.38 (1D7); also elsewhere on the board
/Operand Forwarding A/A_ID7: U7.37 (1D8); also elsewhere on the board
/Operand Forwarding A/A_ID8: U7.36 (2D1); also elsewhere on the board
/Operand Forwarding A/A_ID9: U7.35 (2D2); also elsewhere on the board
/Operand Forwarding A/A_ID10: U7.33 (2D3); also elsewhere on the board
/Operand Forwarding A/A_ID11: U7.32 (2D4); also elsewhere on the board
/Operand Forwarding A/A_ID12: U7.30 (2D5); also elsewhere on the board
/Operand Forwarding A/A_ID13: U7.29 (2D6); also elsewhere on the board
/Operand Forwarding A/A_ID14: U7.27 (2D7); also elsewhere on the board
/Operand Forwarding A/A_ID15: U7.26 (2D8); also elsewhere on the board
GND: C8.2, U7.1 (1~OE), U7.4 (GND), U7.10 (GND), U7.15 (GND), U7.21 (GND), U7.24 (2~OE), U7.28 (GND), U7.34 (GND), U7.39 (GND), U7.45 (GND); also elsewhere on the board
VCC: C8.1, U7.7 (VCC), U7.18 (VCC), U7.31 (VCC), U7.42 (VCC); also elsewhere on the board
