foxostro/Turtle16/Hardware/PrototypeProcessor/BypassModule/BypassModule.kicad_pcb

## KiCad design Hardware/PrototypeProcessor/BypassModule/BypassModule.kicad_pcb (continued)

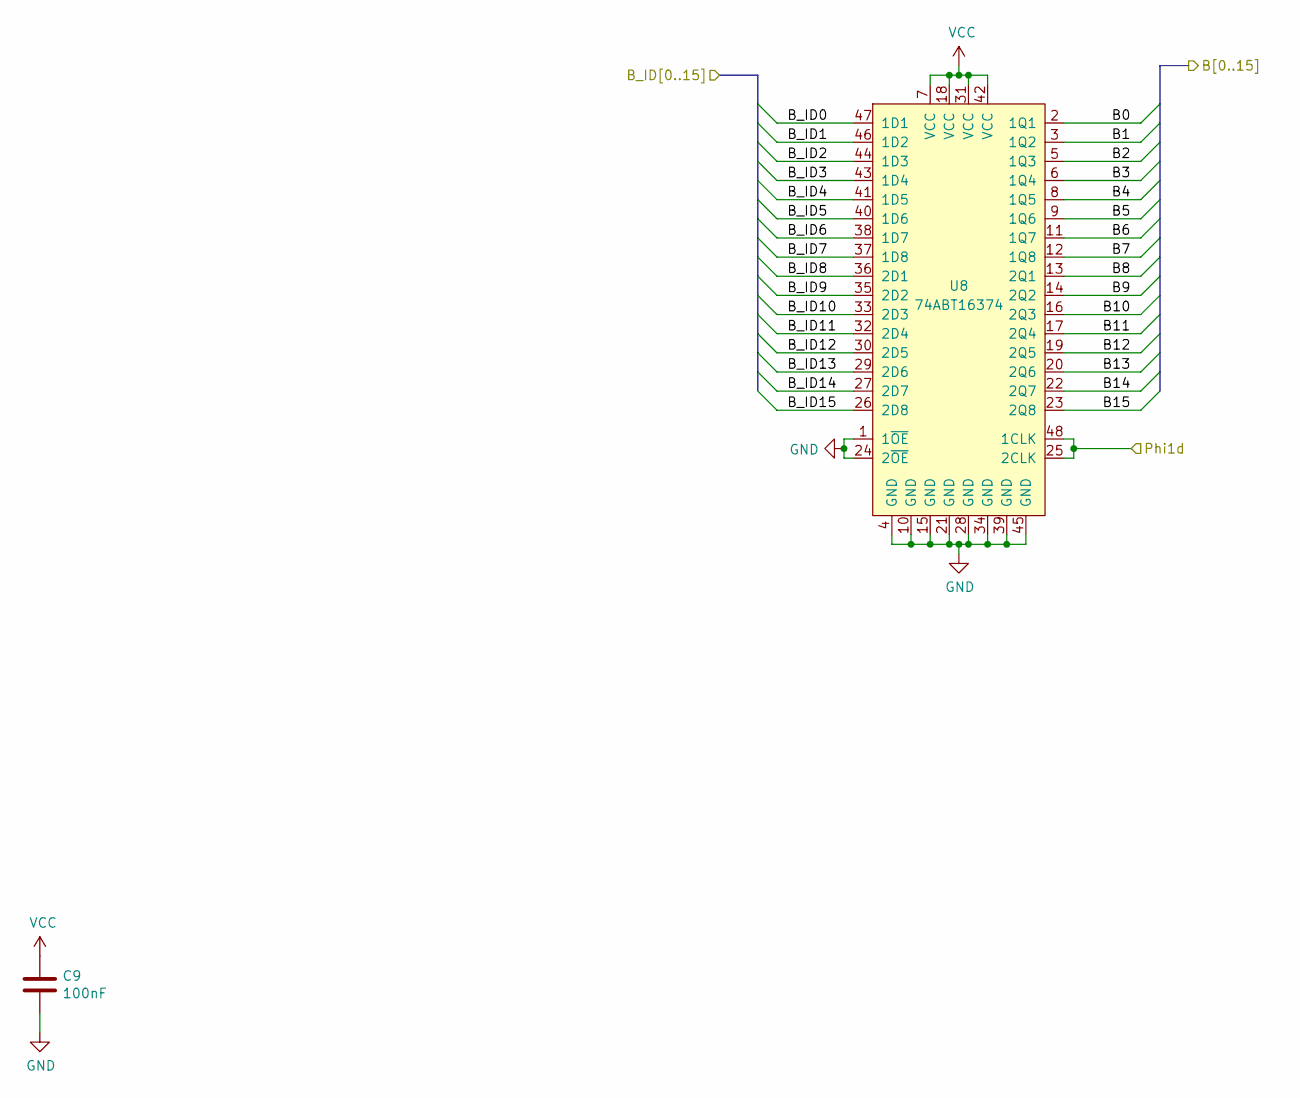
[picture p131: schematic ID_EX_B.kicad_sch]

Parts:
C9: 100nF; C_0603_1608Metric_Pad1.08x0.95mm_HandSolder
U8: 74ABT16374; TSSOP-48_6.1x12.5mm_P0.5mm

Connections:
/Bypass Prototype Inputs/Phi1d: U8.25 (2CLK), U8.48 (1CLK); also elsewhere on the board
/BypassPrototypeOutputs/B0: U8.2 (1Q1); also elsewhere on the board
/BypassPrototypeOutputs/B1: U8.3 (1Q2); also elsewhere on the board
/BypassPrototypeOutputs/B2: U8.5 (1Q3); also elsewhere on the board
/BypassPrototypeOutputs/B3: U8.6 (1Q4); also elsewhere on the board
/BypassPrototypeOutputs/B4: U8.8 (1Q5); also elsewhere on the board
/BypassPrototypeOutputs/B5: U8.9 (1Q6); also elsewhere on the board
/BypassPrototypeOutputs/B6: U8.11 (1Q7); also elsewhere on the board
/BypassPrototypeOutputs/B7: U8.12 (1Q8); also elsewhere on the board
/BypassPrototypeOutputs/B8: U8.13 (2Q1); also elsewhere on the board
/BypassPrototypeOutputs/B9: U8.14 (2Q2); also elsewhere on the board
/BypassPrototypeOutputs/B10: U8.16 (2Q3); also elsewhere on the board
/BypassPrototypeOutputs/B11: U8.17 (2Q4); also elsewhere on the board
/BypassPrototypeOutputs/B12: U8.19 (2Q5); also elsewhere on the board
/BypassPrototypeOutputs/B13: U8.20 (2Q6); also elsewhere on the board
/BypassPrototypeOutputs/B14: U8.22 (2Q7); also elsewhere on the board
/BypassPrototypeOutputs/B15: U8.23 (2Q8); also elsewhere on the board
/Operand Forwarding B/B_ID0: U8.47 (1D1); also elsewhere on the board
/Operand Forwarding B/B_ID1: U8.46 (1D2); also elsewhere on the board
/Operand Forwarding B/B_ID2: U8.44 (1D3); also elsewhere on the board
/Operand Forwarding B/B_ID3: U8.43 (1D4); also elsewhere on the board
/Operand Forwarding B/B_ID4: U8.41 (1D5); also elsewhere on the board
/Operand Forwarding B/B_ID5: U8.40 (1D6); also elsewhere on the board
/Operand Forwarding B/B_ID6: U8.38 (1D7); also elsewhere on the board
/Operand Forwarding B/B_ID7: U8.37 (1D8); also elsewhere on the board
/Operand Forwarding B/B_ID8: U8.36 (2D1); also elsewhere on the board
/Operand Forwarding B/B_ID9: U8.35 (2D2); also elsewhere on the board
/Operand Forwarding B/B_ID10: U8.33 (2D3); also elsewhere on the board
/Operand Forwarding B/B_ID11: U8.32 (2D4); also elsewhere on the board
/Operand Forwarding B/B_ID12: U8.30 (2D5); also elsewhere on the board
/Operand Forwarding B/B_ID13: U8.29 (2D6); also elsewhere on the board
/Operand Forwarding B/B_ID14: U8.27 (2D7); also elsewhere on the board
/Operand Forwarding B/B_ID15: U8.26 (2D8); also elsewhere on the board
GND: C9.2, U8.1 (1~OE), U8.4 (GND), U8.10 (GND), U8.15 (GND), U8.21 (GND), U8.24 (2~OE), U8.28 (GND), U8.34 (GND), U8.39 (GND), U8.45 (GND); also elsewhere on the board
VCC: C9.1, U8.7 (VCC), U8.18 (VCC), U8.31 (VCC), U8.42 (VCC); also elsewhere on the board

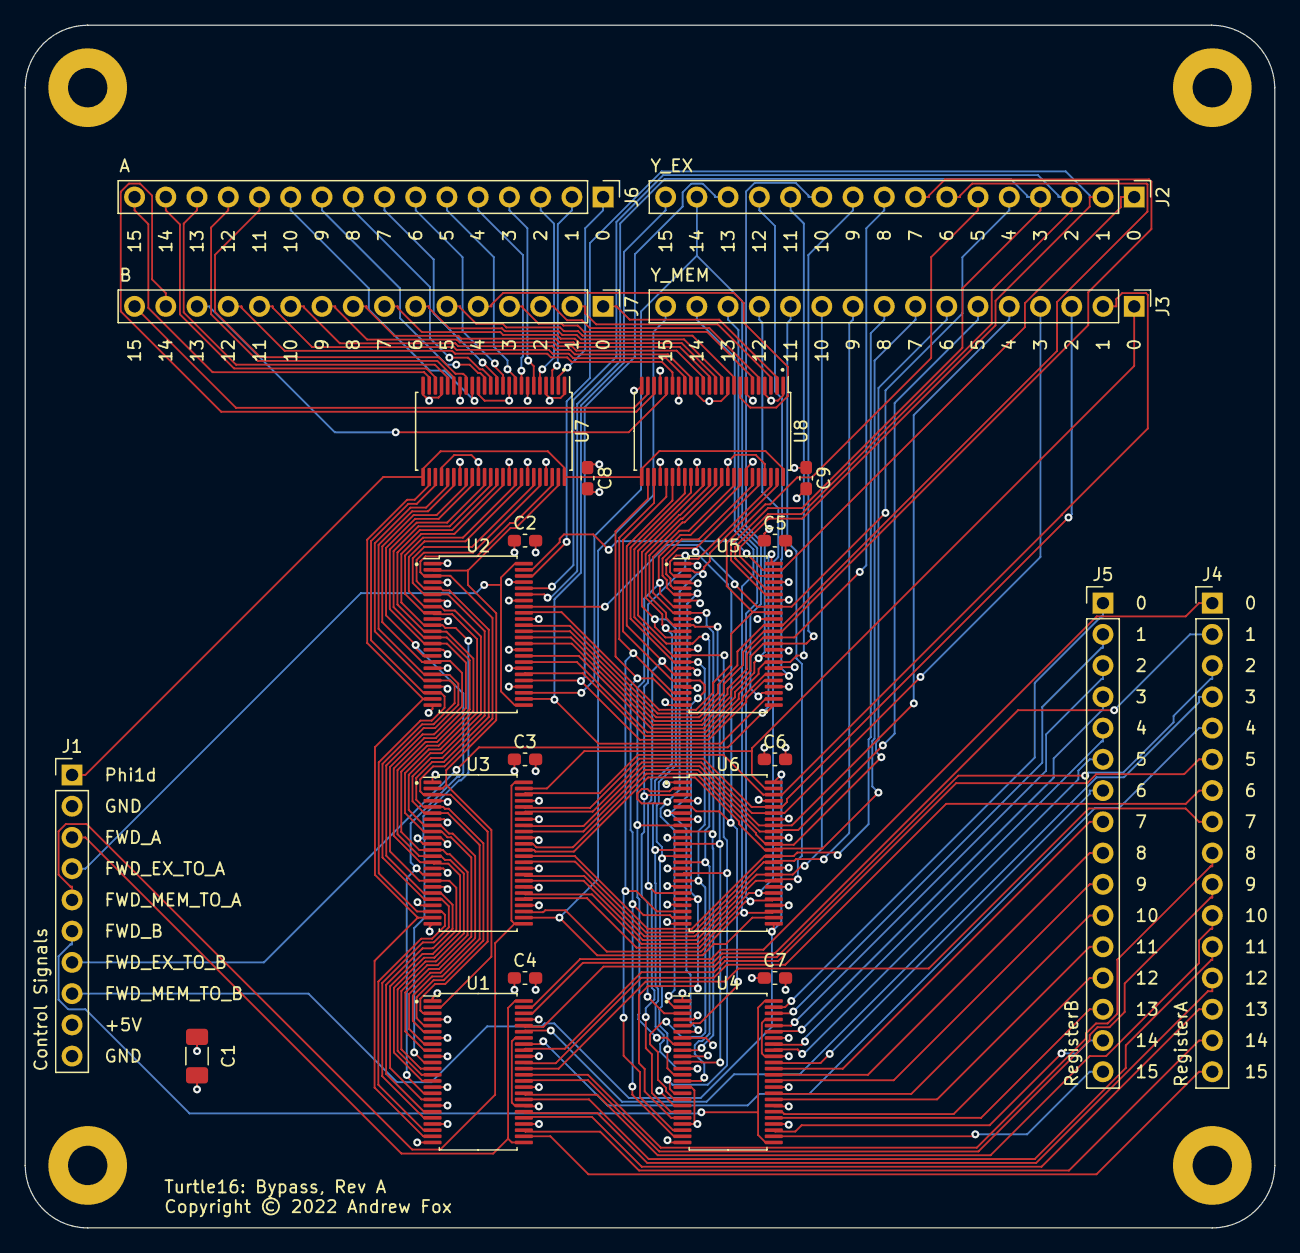
[picture p132: board BypassModule.kicad_pcb from above]

Board: 4 copper layers, 101.6 x 97.8 mm, 28 parts (0 on the bottom side), 137 nets.
