foxostro/Turtle16/Hardware/PrototypeProcessor/ClockModule/ClockModule.kicad_pcb

## KiCad design Hardware/PrototypeProcessor/ClockModule/ClockModule.kicad_pcb (2025-06-30)

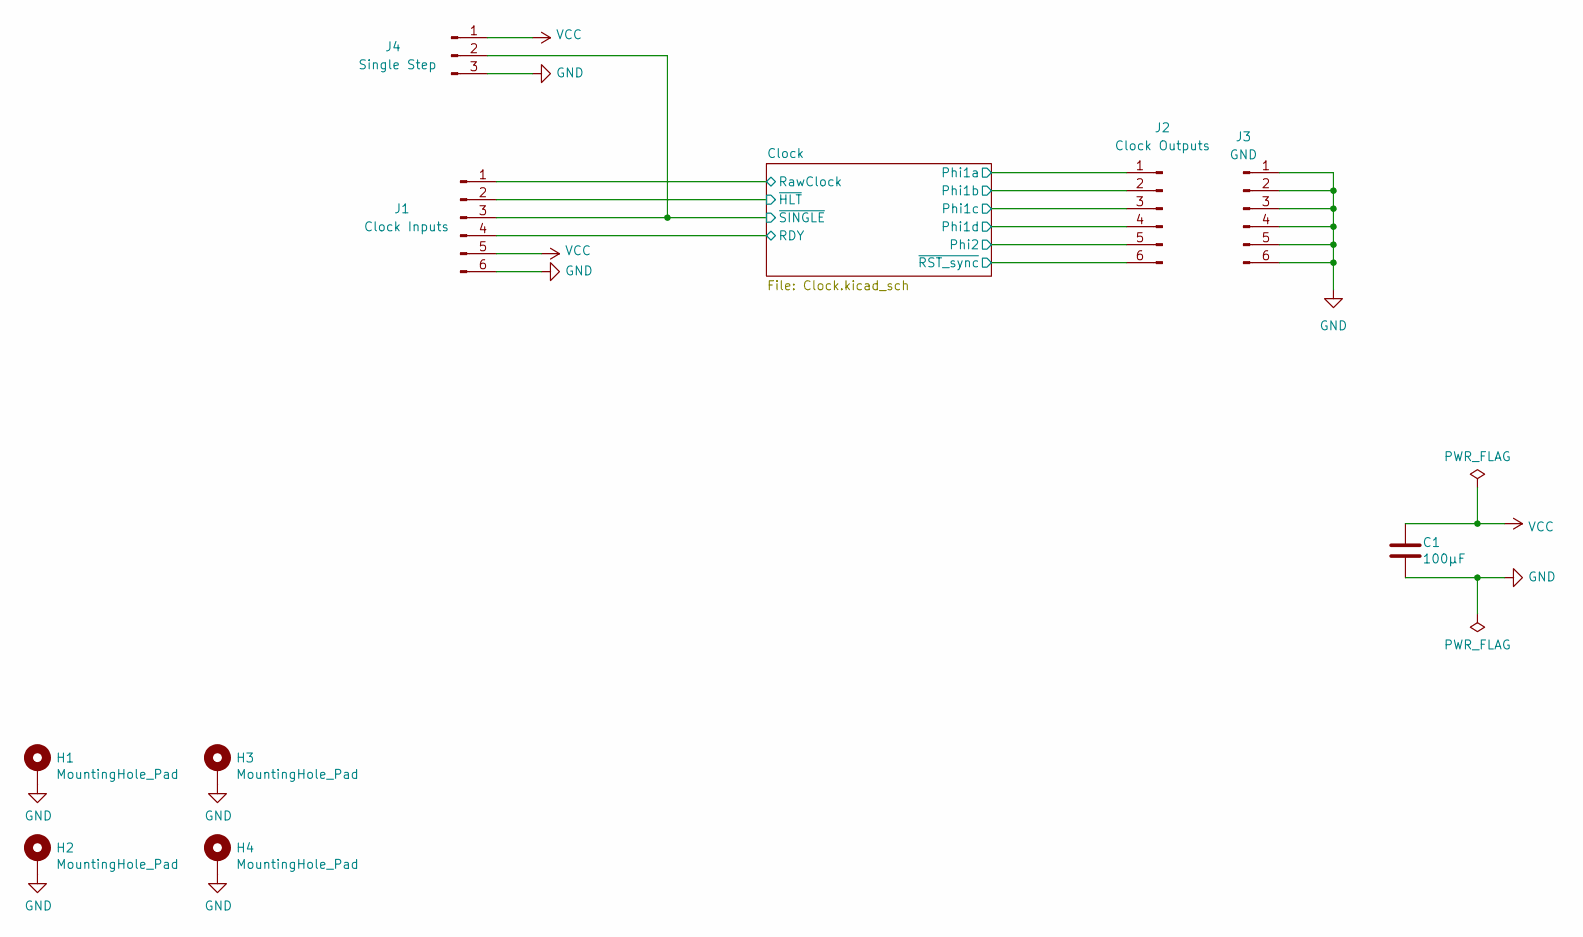
[picture p133: schematic ClockModule.kicad_sch, Turtle16: Clock Module]

Parts:
C1: 100µF; C_1206_3216Metric_Pad1.33x1.80mm_HandSolder
H1, H2, H3, H4: MountingHole_Pad; MountingHole_3.2mm_M3_Pad
J1: Clock Inputs; PinHeader_1x06_P2.54mm_Vertical
J2: Clock Outputs; PinHeader_1x06_P2.54mm_Vertical
J3: GND; PinHeader_1x06_P2.54mm_Vertical
J4: Single Step; PinHeader_1x03_P2.54mm_Vertical

Connections:
/Clock/Phi1a: J2.1; also elsewhere on the board
/Clock/Phi1b: J2.2; also elsewhere on the board
/Clock/Phi1c: J2.3; also elsewhere on the board
/Clock/Phi1d: J2.4; also elsewhere on the board
/Clock/Phi2: J2.5; also elsewhere on the board
/Clock/RDY: J1.4; also elsewhere on the board
/Clock/RawClock: J1.1; also elsewhere on the board
/Clock/~HLT: J1.2; also elsewhere on the board
/Clock/~RST_sync: J2.6; also elsewhere on the board
/Clock/~SINGLE: J1.3, J4.2; also elsewhere on the board
GND: C1.2, H1.1, H2.1, H3.1, H4.1, J1.6, J3.1, J3.2, J3.3, J3.4, J3.5, J3.6, J4.3; also elsewhere on the board
VCC: C1.1, J1.5, J4.1; also elsewhere on the board

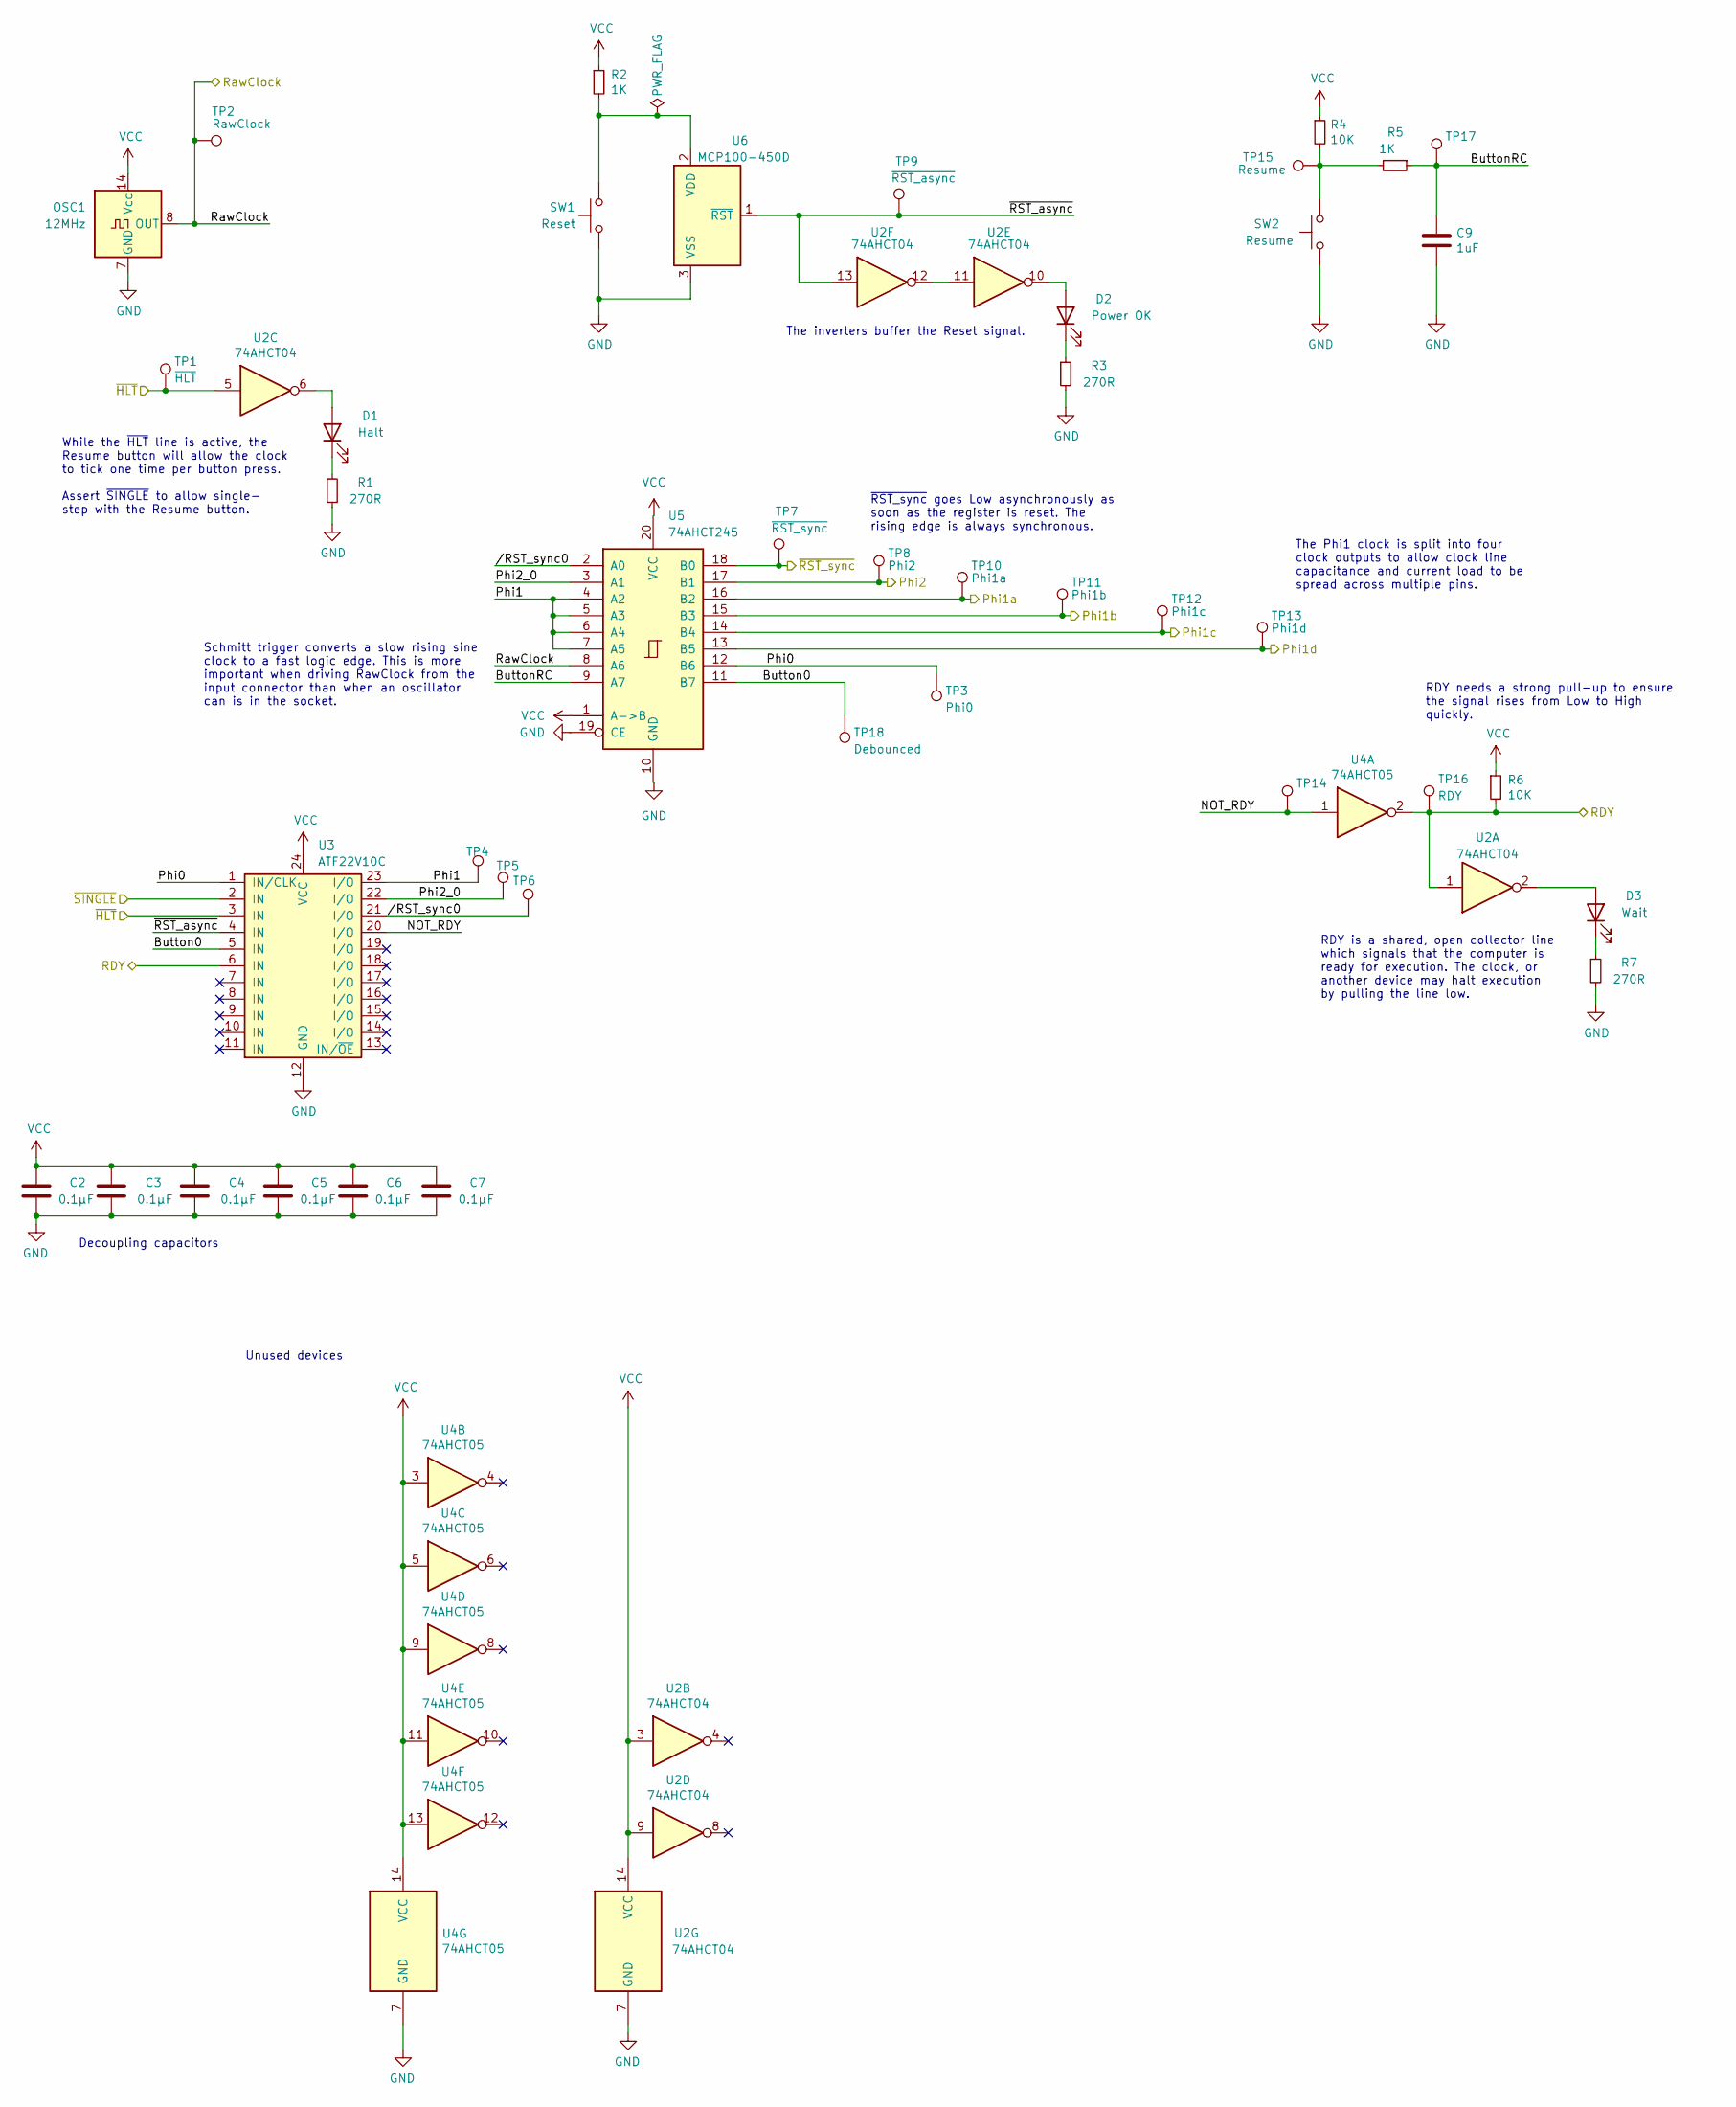
[picture p134: schematic Clock.kicad_sch, Turtle16: Clock]

Parts:
C2, C3, C4, C5, C6, C7: 0.1µF; C_0603_1608Metric_Pad1.08x0.95mm_HandSolder
C9: 1uF; C_0603_1608Metric_Pad1.08x0.95mm_HandSolder
D1: Halt; LED_0805_2012Metric
D2: Power OK; LED_0805_2012Metric
D3: Wait; LED_0805_2012Metric
OSC1: 12MHz; Oscillator_DIP-14
R1, R3, R7: 270R; C_0603_1608Metric
R2, R5: 1K; R_0603_1608Metric_Pad0.98x0.95mm_HandSolder
R4, R6: 10K; R_0603_1608Metric_Pad0.98x0.95mm_HandSolder
SW1: Reset; SW_PUSH_6mm_H5mm
SW2: Resume; SW_PUSH_6mm_H5mm
TP1: ~{HLT}; TestPoint_Pad_D1.0mm
TP2: RawClock; TestPoint_Pad_D1.0mm
TP3: Phi0; TestPoint_Pad_D1.0mm
TP4: TestPoint_Pad_D1.0mm
TP5, TP6, TP14, TP17: TP; TestPoint_Pad_D1.0mm
TP7: ~{RST_sync}; TestPoint_Pad_D1.0mm
TP8: Phi2; TestPoint_Pad_D1.0mm
TP9: ~{RST_async}; TestPoint_Pad_D1.0mm
TP10: Phi1a; TestPoint_Pad_D1.0mm
TP11: Phi1b; TestPoint_Pad_D1.0mm
TP12: Phi1c; TestPoint_Pad_D1.0mm
TP13: Phi1d; TestPoint_Pad_D1.0mm
TP15: Resume; TestPoint_Pad_D1.0mm
TP16: RDY; TestPoint_Pad_D1.0mm
TP18: Debounced; TestPoint_Pad_D1.0mm
U2: 74AHCT04; TSSOP-14_4.4x5mm_P0.65mm
U3: ATF22V10C; DIP-24_W7.62mm_Socket
U4: 74AHCT05; TSSOP-14_4.4x5mm_P0.65mm
U5: 74AHCT245; TSSOP-20_4.4x6.5mm_P0.65mm
U6: MCP100-450D; TO-92

Connections:
/Clock/Button0: TP18.1, U3.5 (IN), U5.11 (B7)
/Clock/ButtonRC: C9.1, R5.1, TP17.1, U5.9 (A7)
/Clock/NOT_RDY: TP14.1, U3.20 (I/O), U4.1
/Clock/Phi0: TP3.1, U3.1 (IN/CLK), U5.12 (B6)
/Clock/Phi1: TP4.1, U3.23 (I/O), U5.4 (A2), U5.5 (A3), U5.6 (A4), U5.7 (A5)
/Clock/Phi1a: TP10.1, U5.16 (B2); also elsewhere on the board
/Clock/Phi1b: TP11.1, U5.15 (B3); also elsewhere on the board
/Clock/Phi1c: TP12.1, U5.14 (B4); also elsewhere on the board
/Clock/Phi1d: TP13.1, U5.13 (B5); also elsewhere on the board
/Clock/Phi2: TP8.1, U5.17 (B1); also elsewhere on the board
/Clock/Phi2_0: TP5.1, U3.22 (I/O), U5.3 (A1)
/Clock/RDY: R6.2, TP16.1, U2.1, U3.6 (IN), U4.2; also elsewhere on the board
/Clock/RawClock: OSC1.8 (OUT), TP2.1, U5.8 (A6); also elsewhere on the board
/Clock//RST_sync0: TP6.1, U3.21 (I/O), U5.2 (A0)
/Clock/~HLT: TP1.1, U2.5, U3.3 (IN); also elsewhere on the board
/Clock/~RST_async: TP9.1, U2.13, U3.4 (IN), U6.1 (~RST)
/Clock/~RST_sync: TP7.1, U5.18 (B0); also elsewhere on the board
/Clock/~SINGLE: U3.2 (IN); also elsewhere on the board
GND: C2.2, C3.2, C4.2, C5.2, C6.2, C7.2, C9.2, OSC1.7 (GND), R1.2, R3.2, R7.2, SW1.1, SW2.1, U2.7 (GND), U3.12 (GND), U4.7 (GND), U5.10 (GND), U5.19 (CE), U6.3 (VSS); also elsewhere on the board
unnamed: D1.2 (A), U2.6
unnamed: D1.1 (K), R1.1
unnamed: D2.2 (A), U2.10
unnamed: D2.1 (K), R3.1
unnamed: D3.2 (A), U2.2
unnamed: D3.1 (K), R7.1
unnamed: R4.2, R5.2, SW2.2, TP15.1
unnamed: U2.11, U2.12
unnamed: R2.2, SW1.2, U6.2 (VDD)
VCC: C2.1, C3.1, C4.1, C5.1, C6.1, C7.1, OSC1.14 (Vcc), R2.1, R4.1, R6.1, U2.3, U2.9, U2.14 (VCC), U3.24 (VCC), U4.3, U4.5, U4.9, U4.11, U4.13, U4.14 (VCC), U5.1 (A->B), U5.20 (VCC); also elsewhere on the board

Notes on the sheet:
~{RST_sync} goes Low asynchronously as soon as the register is reset. The rising edge is always synchronous.
RDY is a shared, open collector line which signals that the computer is ready for execution. The clock, or another device may halt execution by pulling the line low.
The inverters buffer the Reset signal.
RDY needs a strong pull-up to ensure the signal rises from Low to High quickly.
The Phi1 clock is split into four clock outputs to allow clock line capacitance and current load to be spread across multiple pins.
Schmitt trigger converts a slow rising sine clock to a fast logic edge. This is more important when driving RawClock from the input connector than when an oscillator can is in the socket.
Unused devices
While the ~{HLT} line is active, the Resume button will allow the clock to tick one time per button press. Assert ~{SINGLE} to allow single- step with the Resume button.
Decoupling capacitors

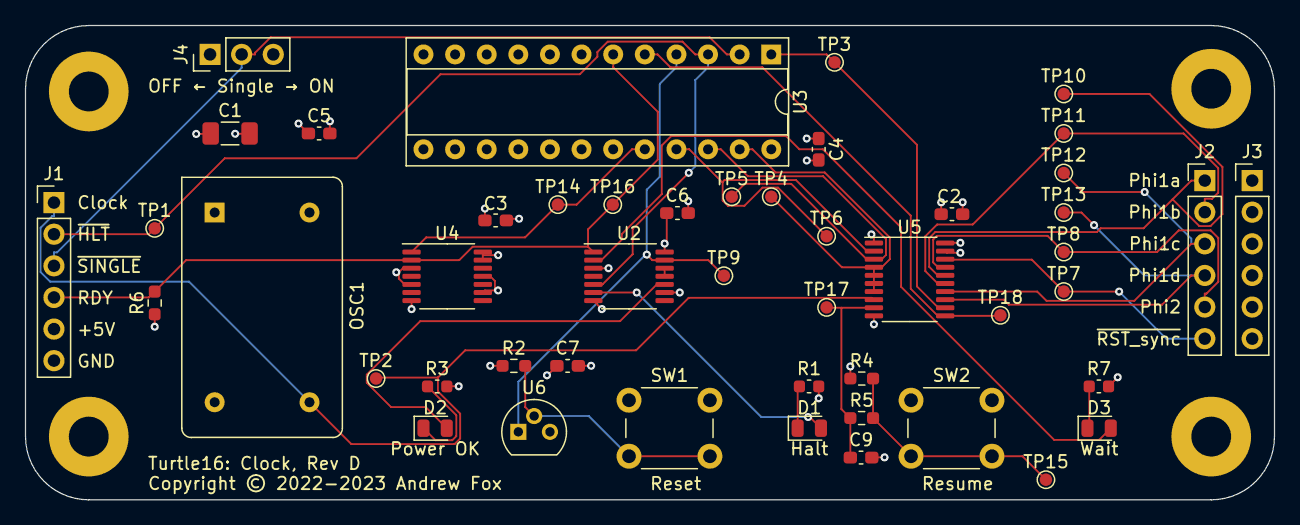
[picture p135: board ClockModule.kicad_pcb from above]

Board: 4 copper layers, 100.3 x 38.1 mm, 52 parts (0 on the bottom side), 29 nets.
