foxostro/Turtle16/Hardware/PrototypeProcessor/PCIFModule/PCIFModule.kicad_pcb

## KiCad design Hardware/PrototypeProcessor/PCIFModule/PCIFModule.kicad_pcb (2025-06-30, an earlier design)

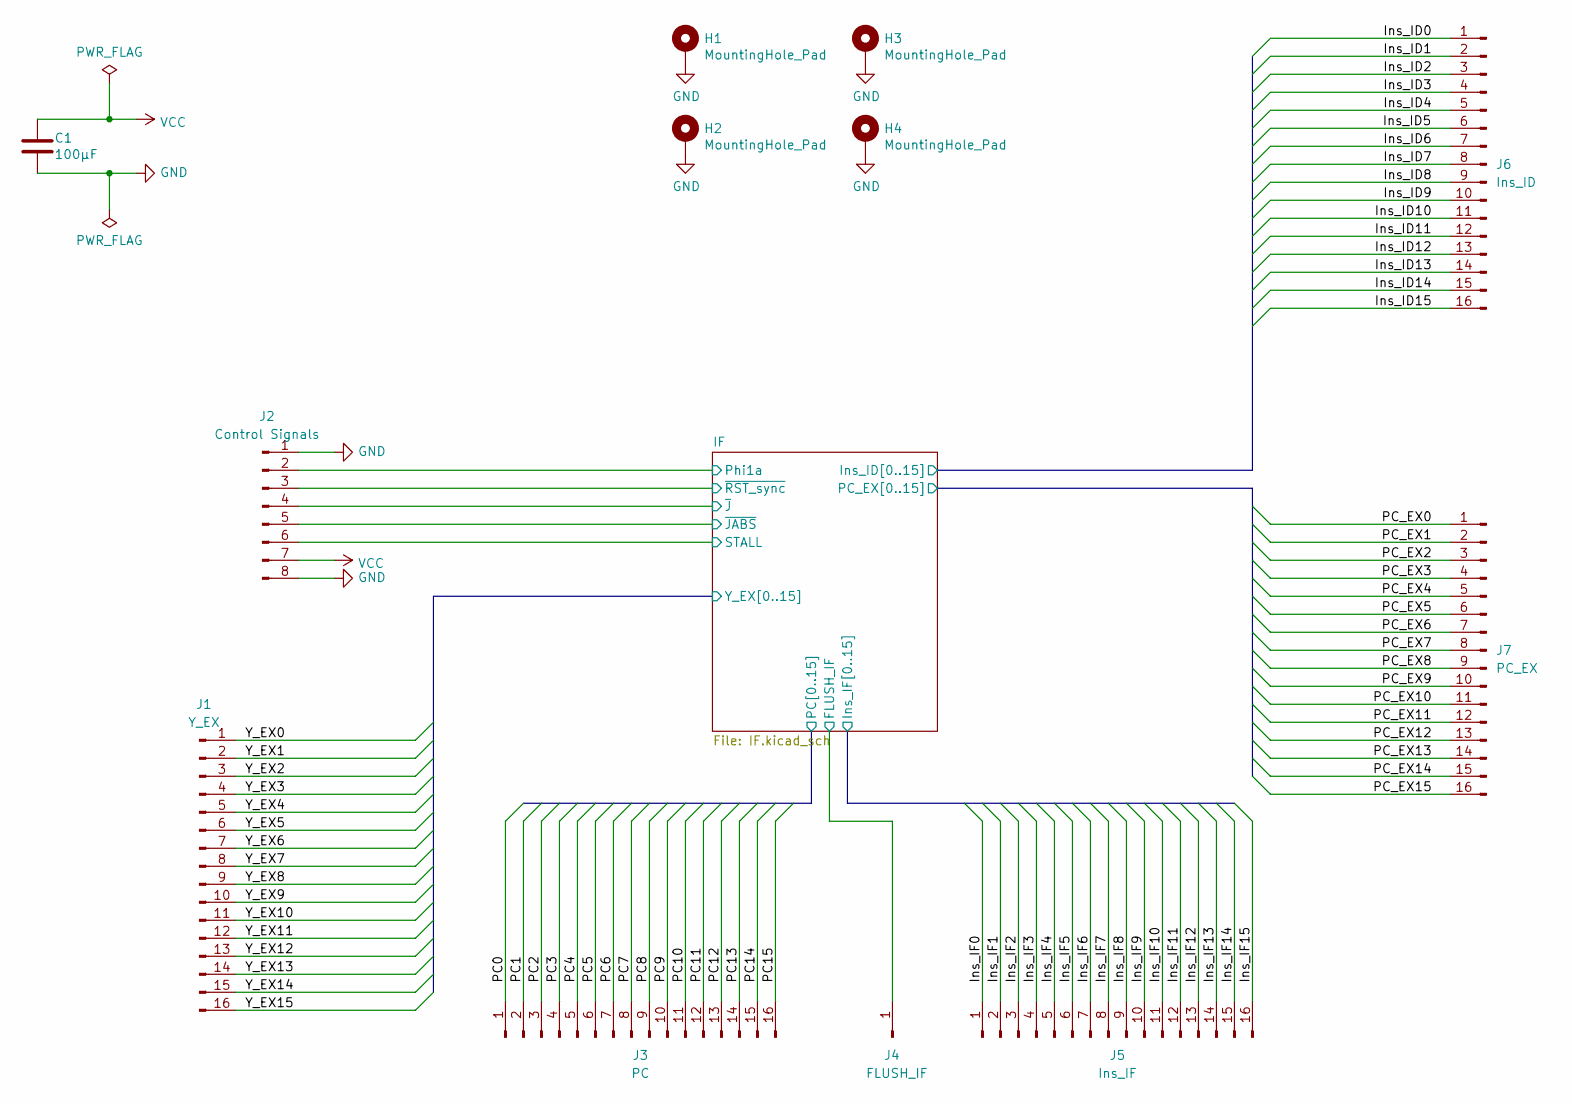
[picture p136: schematic PCIFModule.kicad_sch, Turtle16: Program Counter and Instruction Fetch]

Parts:
C1: 100µF; C_1206_3216Metric_Pad1.33x1.80mm_HandSolder
H1, H2, H3, H4: MountingHole_Pad; MountingHole_3.2mm_M3_Pad
J1: Y_EX; PinHeader_1x16_P2.54mm_Vertical
J2: Control Signals; PinHeader_1x08_P2.54mm_Vertical
J3: PC; PinHeader_1x16_P2.54mm_Vertical
J4: FLUSH_IF; PinHeader_1x01_P2.54mm_Vertical
J5: Ins_IF; PinHeader_1x16_P2.54mm_Vertical
J6: Ins_ID; PinHeader_1x16_P2.54mm_Vertical
J7: PC_EX; PinHeader_1x16_P2.54mm_Vertical

Connections:
/IF/FLUSH_IF: J4.1; also elsewhere on the board
/IF/Ins_ID0: J6.1; also elsewhere on the board
/IF/Ins_ID1: J6.2; also elsewhere on the board
/IF/Ins_ID2: J6.3; also elsewhere on the board
/IF/Ins_ID3: J6.4; also elsewhere on the board
/IF/Ins_ID4: J6.5; also elsewhere on the board
/IF/Ins_ID5: J6.6; also elsewhere on the board
/IF/Ins_ID6: J6.7; also elsewhere on the board
/IF/Ins_ID7: J6.8; also elsewhere on the board
/IF/Ins_ID8: J6.9; also elsewhere on the board
/IF/Ins_ID9: J6.10; also elsewhere on the board
/IF/Ins_ID10: J6.11; also elsewhere on the board
/IF/Ins_ID11: J6.12; also elsewhere on the board
/IF/Ins_ID12: J6.13; also elsewhere on the board
/IF/Ins_ID13: J6.14; also elsewhere on the board
/IF/Ins_ID14: J6.15; also elsewhere on the board
/IF/Ins_ID15: J6.16; also elsewhere on the board
/IF/Ins_IF0: J5.1; also elsewhere on the board
/IF/Ins_IF1: J5.2; also elsewhere on the board
/IF/Ins_IF2: J5.3; also elsewhere on the board
/IF/Ins_IF3: J5.4; also elsewhere on the board
/IF/Ins_IF4: J5.5; also elsewhere on the board
/IF/Ins_IF5: J5.6; also elsewhere on the board
/IF/Ins_IF6: J5.7; also elsewhere on the board
/IF/Ins_IF7: J5.8; also elsewhere on the board
/IF/Ins_IF8: J5.9; also elsewhere on the board
/IF/Ins_IF9: J5.10; also elsewhere on the board
/IF/Ins_IF10: J5.11; also elsewhere on the board
/IF/Ins_IF11: J5.12; also elsewhere on the board
/IF/Ins_IF12: J5.13; also elsewhere on the board
/IF/Ins_IF13: J5.14; also elsewhere on the board
/IF/Ins_IF14: J5.15; also elsewhere on the board
/IF/Ins_IF15: J5.16; also elsewhere on the board
/IF/PC_EX0: J7.1; also elsewhere on the board
/IF/PC_EX1: J7.2; also elsewhere on the board
/IF/PC_EX2: J7.3; also elsewhere on the board
/IF/PC_EX3: J7.4; also elsewhere on the board
/IF/PC_EX4: J7.5; also elsewhere on the board
/IF/PC_EX5: J7.6; also elsewhere on the board
/IF/PC_EX6: J7.7; also elsewhere on the board
/IF/PC_EX7: J7.8; also elsewhere on the board
/IF/PC_EX8: J7.9; also elsewhere on the board
/IF/PC_EX9: J7.10; also elsewhere on the board
/IF/PC_EX10: J7.11; also elsewhere on the board
/IF/PC_EX11: J7.12; also elsewhere on the board
/IF/PC_EX12: J7.13; also elsewhere on the board
/IF/PC_EX13: J7.14; also elsewhere on the board
/IF/PC_EX14: J7.15; also elsewhere on the board
/IF/PC_EX15: J7.16; also elsewhere on the board
/IF/Phi1a: J2.2; also elsewhere on the board
/IF/STALL: J2.6; also elsewhere on the board
/IF/Y_EX0: J1.1; also elsewhere on the board
/IF/Y_EX1: J1.2; also elsewhere on the board
/IF/Y_EX2: J1.3; also elsewhere on the board
/IF/Y_EX3: J1.4; also elsewhere on the board
/IF/Y_EX4: J1.5; also elsewhere on the board
/IF/Y_EX5: J1.6; also elsewhere on the board
/IF/Y_EX6: J1.7; also elsewhere on the board
/IF/Y_EX7: J1.8; also elsewhere on the board
/IF/Y_EX8: J1.9; also elsewhere on the board
/IF/Y_EX9: J1.10; also elsewhere on the board
/IF/Y_EX10: J1.11; also elsewhere on the board
/IF/Y_EX11: J1.12; also elsewhere on the board
/IF/Y_EX12: J1.13; also elsewhere on the board
/IF/Y_EX13: J1.14; also elsewhere on the board
/IF/Y_EX14: J1.15; also elsewhere on the board
/IF/Y_EX15: J1.16; also elsewhere on the board
/IF/sheet5FE3DA15/PC0: J3.1; also elsewhere on the board
/IF/sheet5FE3DA15/PC1: J3.2; also elsewhere on the board
/IF/sheet5FE3DA15/PC2: J3.3; also elsewhere on the board
/IF/sheet5FE3DA15/PC3: J3.4; also elsewhere on the board
/IF/sheet5FE3DA15/PC4: J3.5; also elsewhere on the board
/IF/sheet5FE3DA15/PC5: J3.6; also elsewhere on the board
/IF/sheet5FE3DA15/PC6: J3.7; also elsewhere on the board
/IF/sheet5FE3DA15/PC7: J3.8; also elsewhere on the board
/IF/sheet5FE3DA15/PC8: J3.9; also elsewhere on the board
/IF/sheet5FE3DA15/PC9: J3.10; also elsewhere on the board
/IF/sheet5FE3DA15/PC10: J3.11; also elsewhere on the board
/IF/sheet5FE3DA15/PC11: J3.12; also elsewhere on the board
/IF/sheet5FE3DA15/PC12: J3.13; also elsewhere on the board
/IF/sheet5FE3DA15/PC13: J3.14; also elsewhere on the board
/IF/sheet5FE3DA15/PC14: J3.15; also elsewhere on the board
/IF/sheet5FE3DA15/PC15: J3.16; also elsewhere on the board
/IF/~JABS: J2.5; also elsewhere on the board
/IF/~J: J2.4; also elsewhere on the board
/IF/~RST_sync: J2.3; also elsewhere on the board
GND: C1.2, H1.1, H2.1, H3.1, H4.1, J2.1, J2.8; also elsewhere on the board
VCC: C1.1, J2.7; also elsewhere on the board

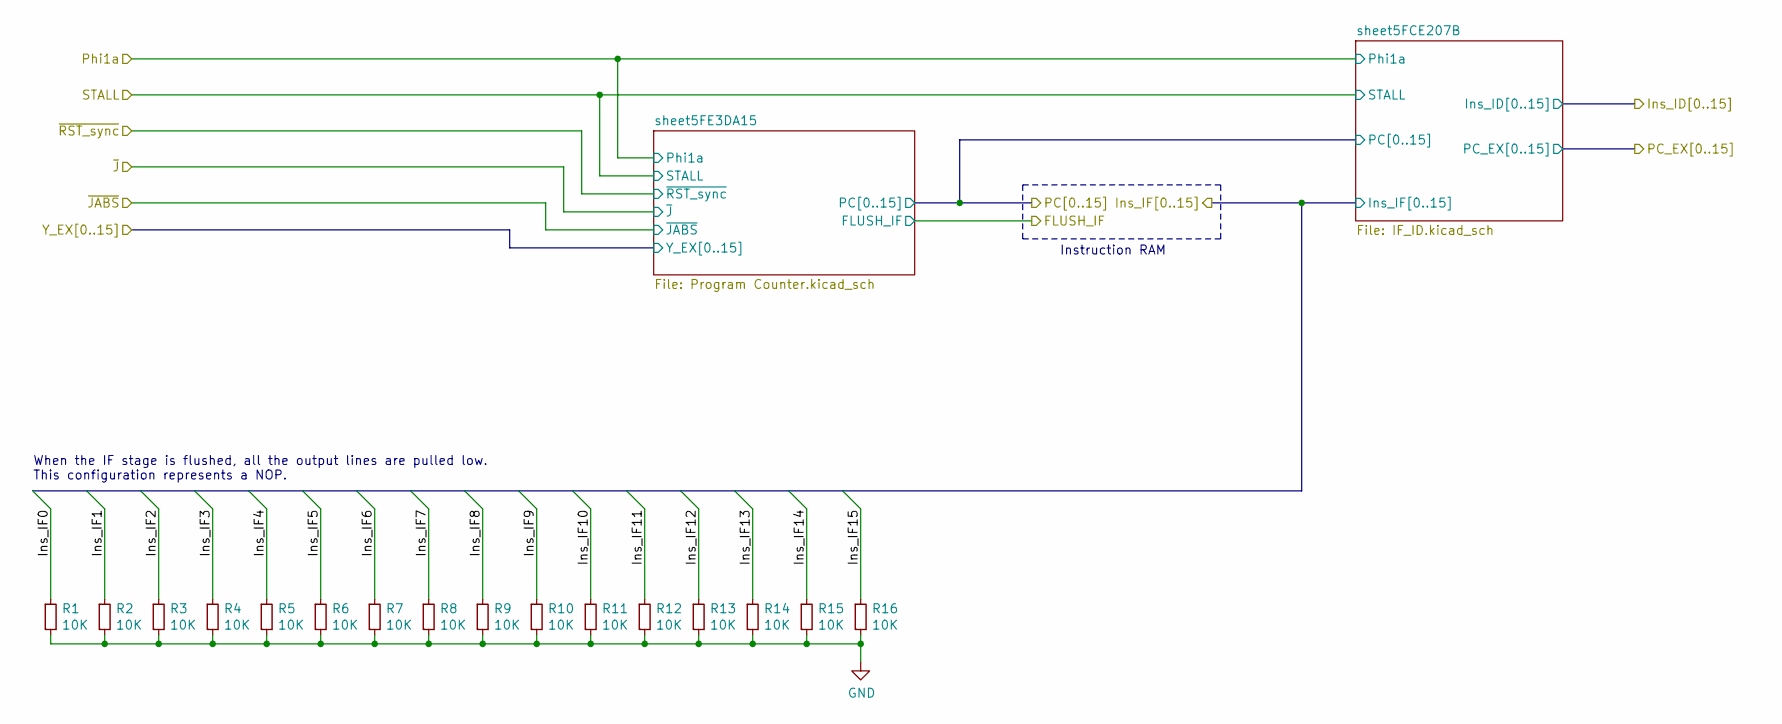
[picture p137: schematic IF.kicad_sch]

Parts:
R1, R2, R3, R4, R5, R6, R7, R8, R9, R10, R11, R12, R13, R14, R15, R16: 10K; R_0603_1608Metric_Pad0.98x0.95mm_HandSolder

Connections:
/IF/Ins_IF0: R1.1; also elsewhere on the board
/IF/Ins_IF1: R2.1; also elsewhere on the board
/IF/Ins_IF2: R3.1; also elsewhere on the board
/IF/Ins_IF3: R4.1; also elsewhere on the board
/IF/Ins_IF4: R5.1; also elsewhere on the board
/IF/Ins_IF5: R6.1; also elsewhere on the board
/IF/Ins_IF6: R7.1; also elsewhere on the board
/IF/Ins_IF7: R8.1; also elsewhere on the board
/IF/Ins_IF8: R9.1; also elsewhere on the board
/IF/Ins_IF9: R10.1; also elsewhere on the board
/IF/Ins_IF10: R11.1; also elsewhere on the board
/IF/Ins_IF11: R12.1; also elsewhere on the board
/IF/Ins_IF12: R13.1; also elsewhere on the board
/IF/Ins_IF13: R14.1; also elsewhere on the board
/IF/Ins_IF14: R15.1; also elsewhere on the board
/IF/Ins_IF15: R16.1; also elsewhere on the board
GND: R1.2, R2.2, R3.2, R4.2, R5.2, R6.2, R7.2, R8.2, R9.2, R10.2, R11.2, R12.2, R13.2, R14.2, R15.2, R16.2; also elsewhere on the board

Notes on the sheet:
Instruction RAM
When the IF stage is flushed, all the output lines are pulled low. This configuration represents a NOP.
