foxostro/Turtle16/Hardware/PrototypeProcessor/PCIFModule/PCIFModule.kicad_pcb

## KiCad design Hardware/PrototypeProcessor/PCIFModule/PCIFModule.kicad_pcb (continued)

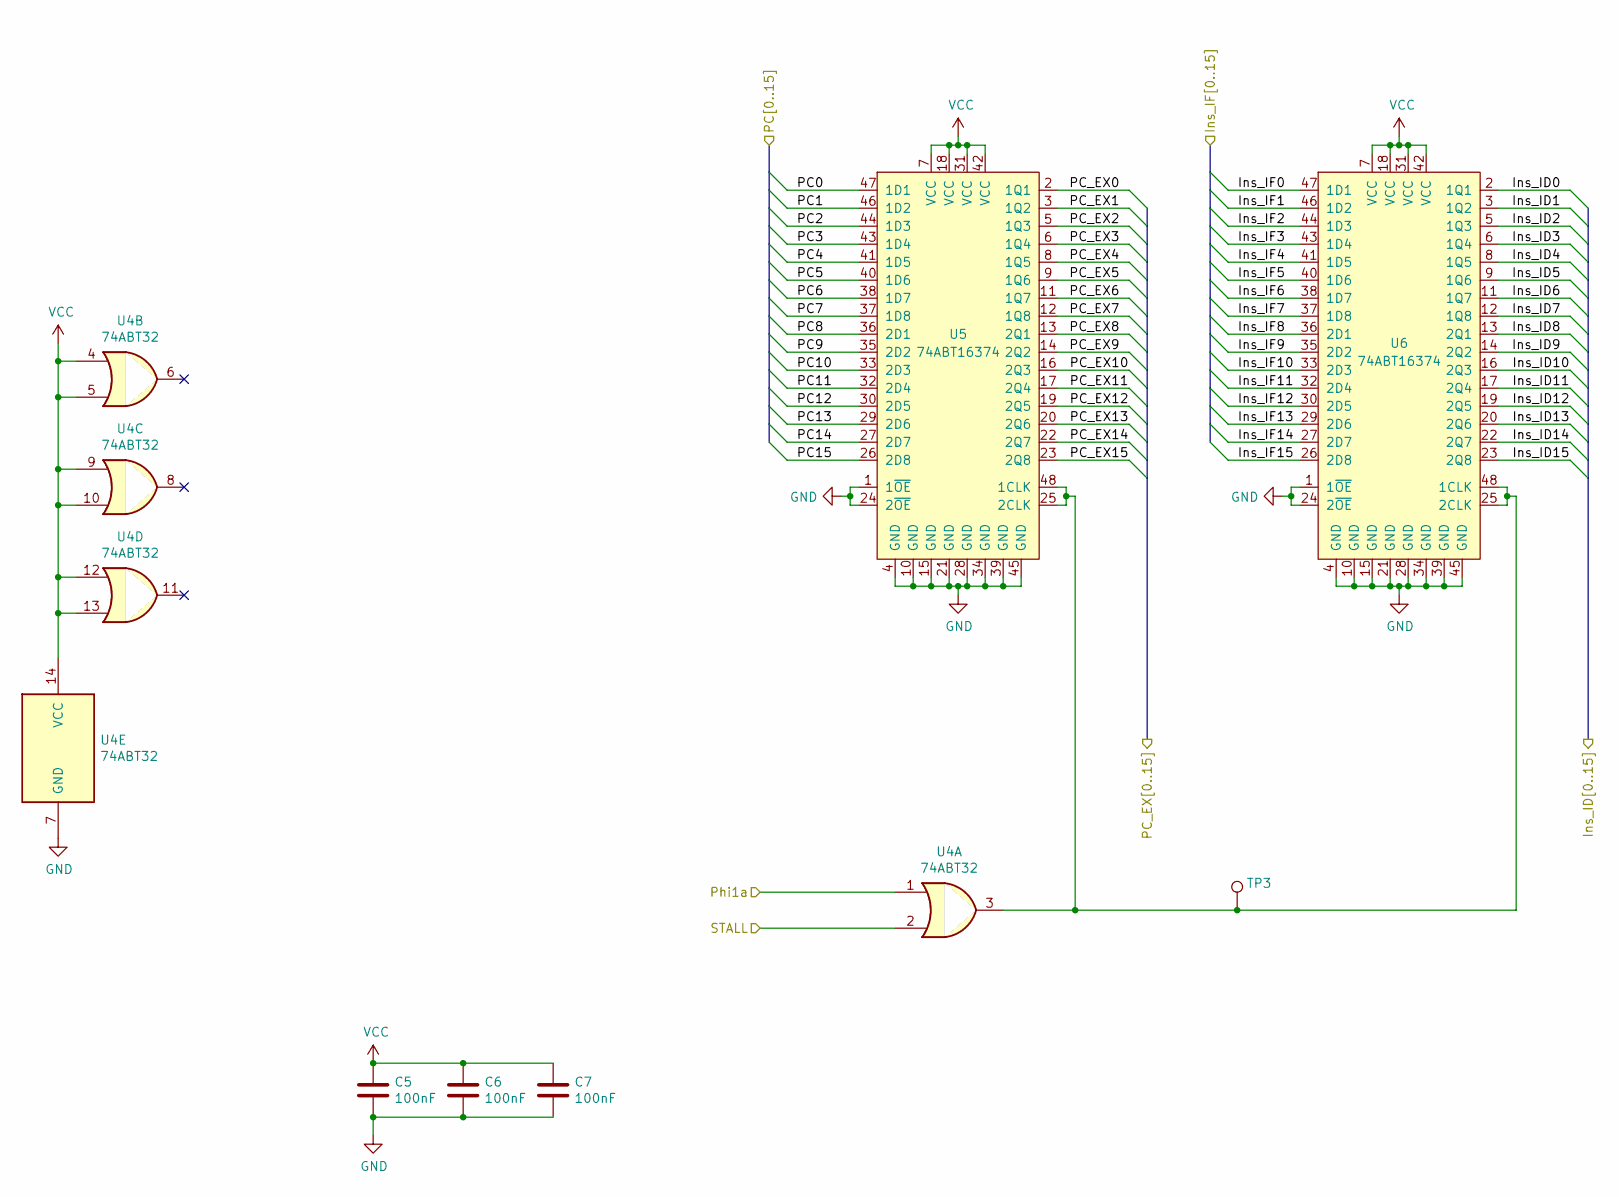
[picture p138: schematic IF_ID.kicad_sch, IF/ID]

Parts:
C5, C6, C7: 100nF; C_0603_1608Metric_Pad1.08x0.95mm_HandSolder
TP3: CLK; TestPoint_Pad_D1.0mm
U4: 74ABT32; TSSOP-14_4.4x5mm_P0.65mm
U5, U6: 74ABT16374; TSSOP-48_8x12.5mm_P0.5mm

Connections:
/IF/Ins_ID0: U6.2 (1Q1); also elsewhere on the board
/IF/Ins_ID1: U6.3 (1Q2); also elsewhere on the board
/IF/Ins_ID2: U6.5 (1Q3); also elsewhere on the board
/IF/Ins_ID3: U6.6 (1Q4); also elsewhere on the board
/IF/Ins_ID4: U6.8 (1Q5); also elsewhere on the board
/IF/Ins_ID5: U6.9 (1Q6); also elsewhere on the board
/IF/Ins_ID6: U6.11 (1Q7); also elsewhere on the board
/IF/Ins_ID7: U6.12 (1Q8); also elsewhere on the board
/IF/Ins_ID8: U6.13 (2Q1); also elsewhere on the board
/IF/Ins_ID9: U6.14 (2Q2); also elsewhere on the board
/IF/Ins_ID10: U6.16 (2Q3); also elsewhere on the board
/IF/Ins_ID11: U6.17 (2Q4); also elsewhere on the board
/IF/Ins_ID12: U6.19 (2Q5); also elsewhere on the board
/IF/Ins_ID13: U6.20 (2Q6); also elsewhere on the board
/IF/Ins_ID14: U6.22 (2Q7); also elsewhere on the board
/IF/Ins_ID15: U6.23 (2Q8); also elsewhere on the board
/IF/Ins_IF0: U6.47 (1D1); also elsewhere on the board
/IF/Ins_IF1: U6.46 (1D2); also elsewhere on the board
/IF/Ins_IF2: U6.44 (1D3); also elsewhere on the board
/IF/Ins_IF3: U6.43 (1D4); also elsewhere on the board
/IF/Ins_IF4: U6.41 (1D5); also elsewhere on the board
/IF/Ins_IF5: U6.40 (1D6); also elsewhere on the board
/IF/Ins_IF6: U6.38 (1D7); also elsewhere on the board
/IF/Ins_IF7: U6.37 (1D8); also elsewhere on the board
/IF/Ins_IF8: U6.36 (2D1); also elsewhere on the board
/IF/Ins_IF9: U6.35 (2D2); also elsewhere on the board
/IF/Ins_IF10: U6.33 (2D3); also elsewhere on the board
/IF/Ins_IF11: U6.32 (2D4); also elsewhere on the board
/IF/Ins_IF12: U6.30 (2D5); also elsewhere on the board
/IF/Ins_IF13: U6.29 (2D6); also elsewhere on the board
/IF/Ins_IF14: U6.27 (2D7); also elsewhere on the board
/IF/Ins_IF15: U6.26 (2D8); also elsewhere on the board
/IF/PC_EX0: U5.2 (1Q1); also elsewhere on the board
/IF/PC_EX1: U5.3 (1Q2); also elsewhere on the board
/IF/PC_EX2: U5.5 (1Q3); also elsewhere on the board
/IF/PC_EX3: U5.6 (1Q4); also elsewhere on the board
/IF/PC_EX4: U5.8 (1Q5); also elsewhere on the board
/IF/PC_EX5: U5.9 (1Q6); also elsewhere on the board
/IF/PC_EX6: U5.11 (1Q7); also elsewhere on the board
/IF/PC_EX7: U5.12 (1Q8); also elsewhere on the board
/IF/PC_EX8: U5.13 (2Q1); also elsewhere on the board
/IF/PC_EX9: U5.14 (2Q2); also elsewhere on the board
/IF/PC_EX10: U5.16 (2Q3); also elsewhere on the board
/IF/PC_EX11: U5.17 (2Q4); also elsewhere on the board
/IF/PC_EX12: U5.19 (2Q5); also elsewhere on the board
/IF/PC_EX13: U5.20 (2Q6); also elsewhere on the board
/IF/PC_EX14: U5.22 (2Q7); also elsewhere on the board
/IF/PC_EX15: U5.23 (2Q8); also elsewhere on the board
/IF/Phi1a: U4.1; also elsewhere on the board
/IF/STALL: U4.2; also elsewhere on the board
/IF/sheet5FE3DA15/PC0: U5.47 (1D1); also elsewhere on the board
/IF/sheet5FE3DA15/PC1: U5.46 (1D2); also elsewhere on the board
/IF/sheet5FE3DA15/PC2: U5.44 (1D3); also elsewhere on the board
/IF/sheet5FE3DA15/PC3: U5.43 (1D4); also elsewhere on the board
/IF/sheet5FE3DA15/PC4: U5.41 (1D5); also elsewhere on the board
/IF/sheet5FE3DA15/PC5: U5.40 (1D6); also elsewhere on the board
/IF/sheet5FE3DA15/PC6: U5.38 (1D7); also elsewhere on the board
/IF/sheet5FE3DA15/PC7: U5.37 (1D8); also elsewhere on the board
/IF/sheet5FE3DA15/PC8: U5.36 (2D1); also elsewhere on the board
/IF/sheet5FE3DA15/PC9: U5.35 (2D2); also elsewhere on the board
/IF/sheet5FE3DA15/PC10: U5.33 (2D3); also elsewhere on the board
/IF/sheet5FE3DA15/PC11: U5.32 (2D4); also elsewhere on the board
/IF/sheet5FE3DA15/PC12: U5.30 (2D5); also elsewhere on the board
/IF/sheet5FE3DA15/PC13: U5.29 (2D6); also elsewhere on the board
/IF/sheet5FE3DA15/PC14: U5.27 (2D7); also elsewhere on the board
/IF/sheet5FE3DA15/PC15: U5.26 (2D8); also elsewhere on the board
GND: C5.2, C6.2, C7.2, U4.7 (GND), U5.1 (1~OE), U5.4 (GND), U5.10 (GND), U5.15 (GND), U5.21 (GND), U5.24 (2~OE), U5.28 (GND), U5.34 (GND), U5.39 (GND), U5.45 (GND), U6.1 (1~OE), U6.4 (GND), U6.10 (GND), U6.15 (GND), U6.21 (GND), U6.24 (2~OE), U6.28 (GND), U6.34 (GND), U6.39 (GND), U6.45 (GND); also elsewhere on the board
unnamed: TP3.1, U4.3, U5.25 (2CLK), U5.48 (1CLK), U6.25 (2CLK), U6.48 (1CLK)
VCC: C5.1, C6.1, C7.1, U4.4, U4.5, U4.9, U4.10, U4.12, U4.13, U4.14 (VCC), U5.7 (VCC), U5.18 (VCC), U5.31 (VCC), U5.42 (VCC), U6.7 (VCC), U6.18 (VCC), U6.31 (VCC), U6.42 (VCC); also elsewhere on the board

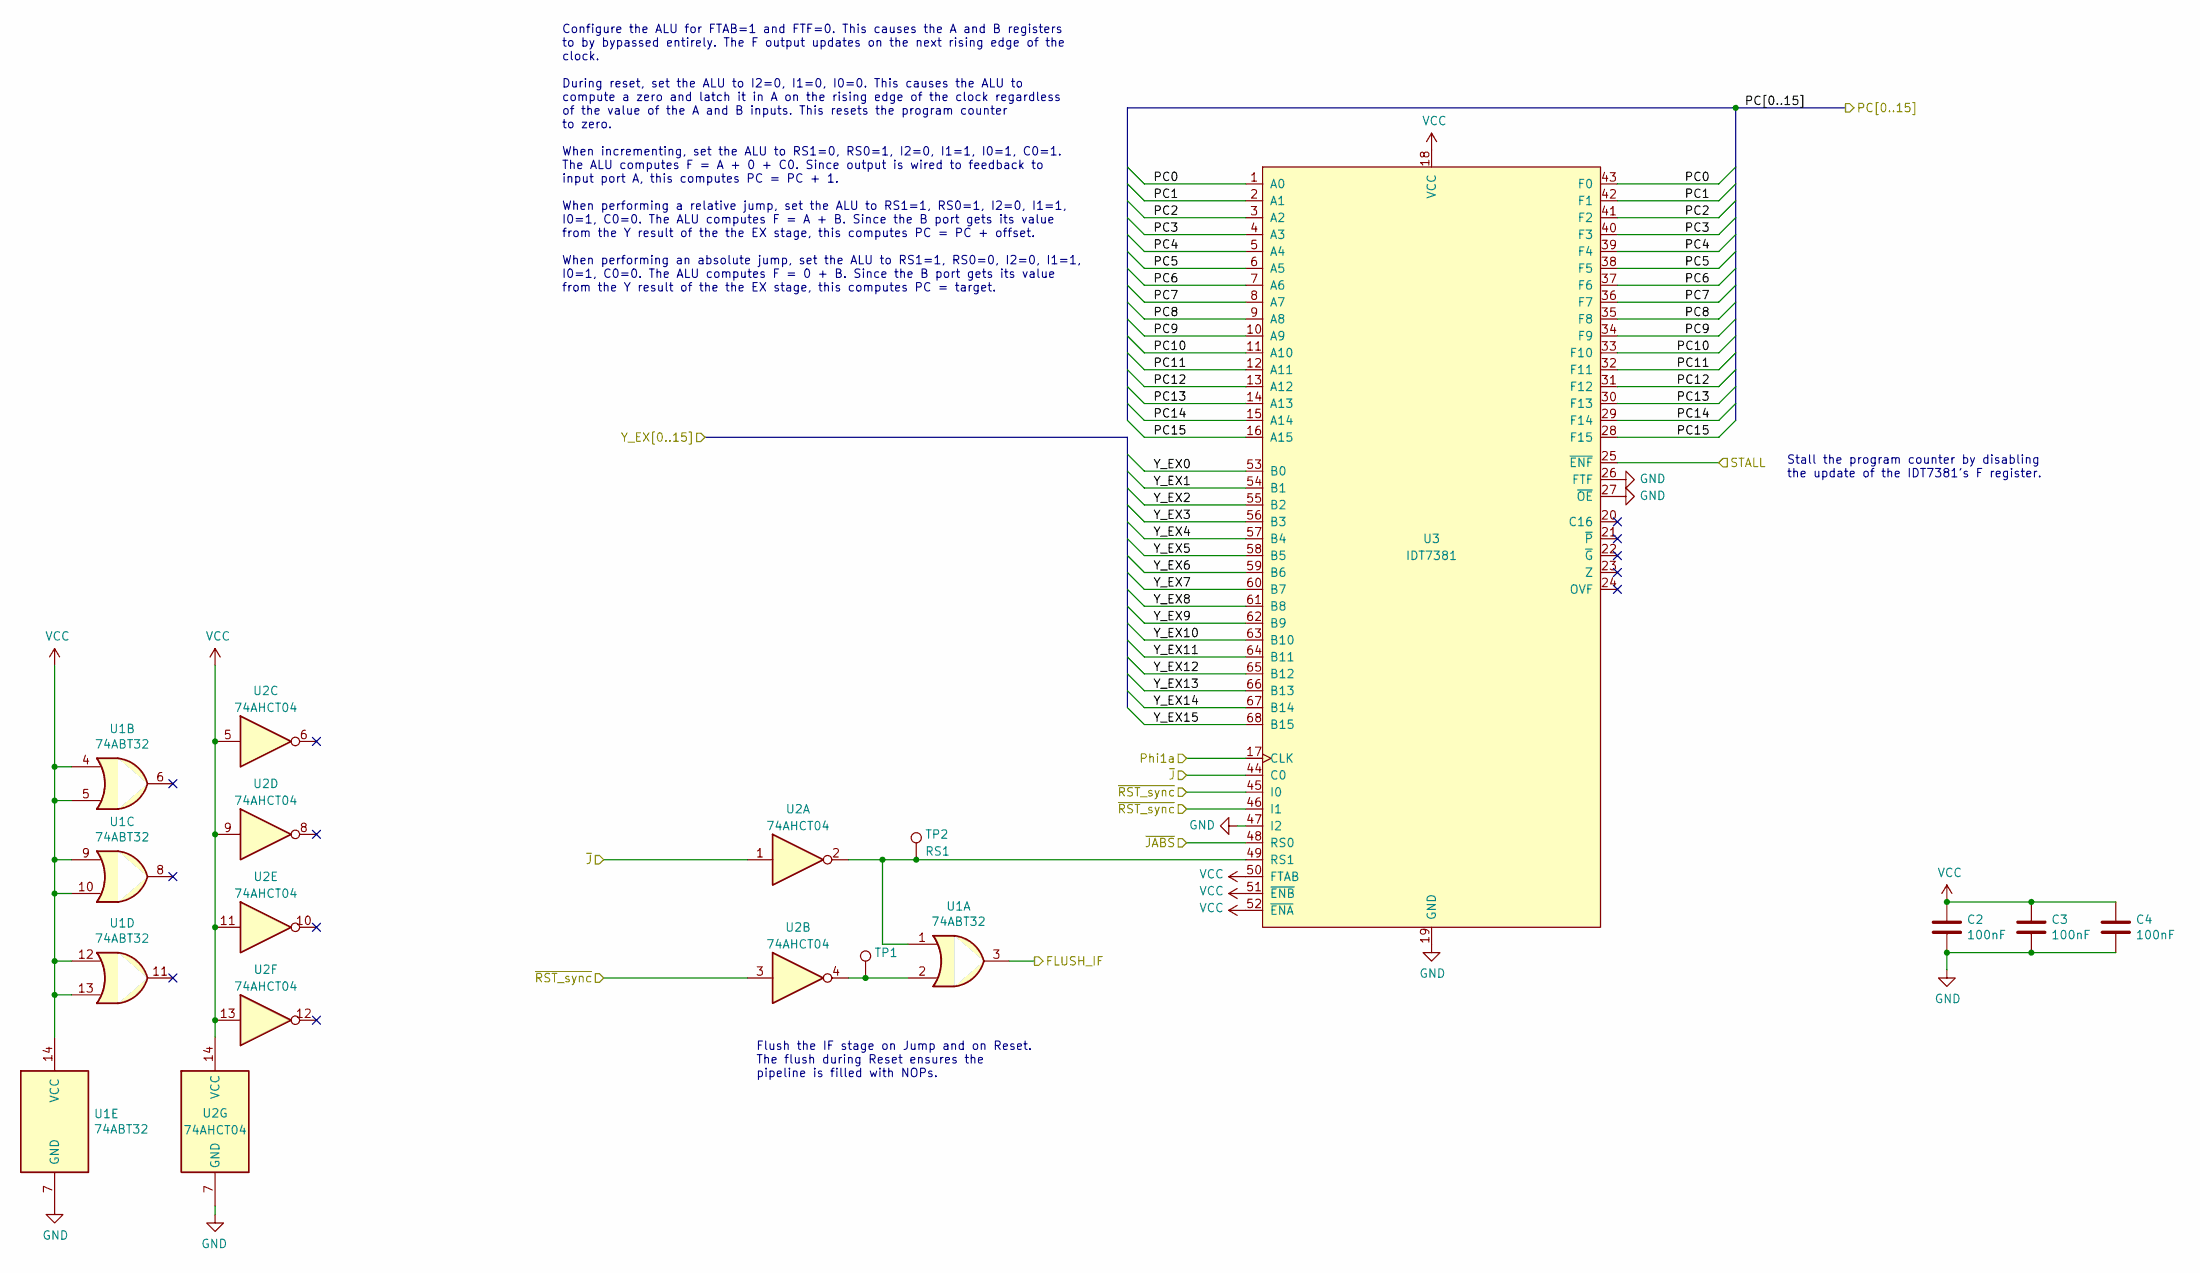
[picture p139: schematic Program Counter.kicad_sch]

Parts:
C2, C3, C4: 100nF; C_0603_1608Metric_Pad1.08x0.95mm_HandSolder
TP1: TP; TestPoint_Pad_D1.0mm
TP2: RS1; TestPoint_Pad_D1.0mm
U1: 74ABT32; TSSOP-14_4.4x5mm_P0.65mm
U2: 74AHCT04; TSSOP-14_4.4x5mm_P0.65mm
U3: IDT7381; PLCC-68_SMD-Socket

Connections:
/IF/FLUSH_IF: U1.3; also elsewhere on the board
/IF/Phi1a: U3.17 (CLK); also elsewhere on the board
/IF/STALL: U3.25 (~ENF); also elsewhere on the board
/IF/Y_EX0: U3.53 (B0); also elsewhere on the board
/IF/Y_EX1: U3.54 (B1); also elsewhere on the board
/IF/Y_EX2: U3.55 (B2); also elsewhere on the board
/IF/Y_EX3: U3.56 (B3); also elsewhere on the board
/IF/Y_EX4: U3.57 (B4); also elsewhere on the board
/IF/Y_EX5: U3.58 (B5); also elsewhere on the board
/IF/Y_EX6: U3.59 (B6); also elsewhere on the board
/IF/Y_EX7: U3.60 (B7); also elsewhere on the board
/IF/Y_EX8: U3.61 (B8); also elsewhere on the board
/IF/Y_EX9: U3.62 (B9); also elsewhere on the board
/IF/Y_EX10: U3.63 (B10); also elsewhere on the board
/IF/Y_EX11: U3.64 (B11); also elsewhere on the board
/IF/Y_EX12: U3.65 (B12); also elsewhere on the board
/IF/Y_EX13: U3.66 (B13); also elsewhere on the board
/IF/Y_EX14: U3.67 (B14); also elsewhere on the board
/IF/Y_EX15: U3.68 (B15); also elsewhere on the board
/IF/sheet5FE3DA15/PC0: U3.1 (A0), U3.43 (F0); also elsewhere on the board
/IF/sheet5FE3DA15/PC1: U3.2 (A1), U3.42 (F1); also elsewhere on the board
/IF/sheet5FE3DA15/PC2: U3.3 (A2), U3.41 (F2); also elsewhere on the board
/IF/sheet5FE3DA15/PC3: U3.4 (A3), U3.40 (F3); also elsewhere on the board
/IF/sheet5FE3DA15/PC4: U3.5 (A4), U3.39 (F4); also elsewhere on the board
/IF/sheet5FE3DA15/PC5: U3.6 (A5), U3.38 (F5); also elsewhere on the board
/IF/sheet5FE3DA15/PC6: U3.7 (A6), U3.37 (F6); also elsewhere on the board
/IF/sheet5FE3DA15/PC7: U3.8 (A7), U3.36 (F7); also elsewhere on the board
/IF/sheet5FE3DA15/PC8: U3.9 (A8), U3.35 (F8); also elsewhere on the board
/IF/sheet5FE3DA15/PC9: U3.10 (A9), U3.34 (F9); also elsewhere on the board
/IF/sheet5FE3DA15/PC10: U3.11 (A10), U3.33 (F10); also elsewhere on the board
/IF/sheet5FE3DA15/PC11: U3.12 (A11), U3.32 (F11); also elsewhere on the board
/IF/sheet5FE3DA15/PC12: U3.13 (A12), U3.31 (F12); also elsewhere on the board
/IF/sheet5FE3DA15/PC13: U3.14 (A13), U3.30 (F13); also elsewhere on the board
/IF/sheet5FE3DA15/PC14: U3.15 (A14), U3.29 (F14); also elsewhere on the board
/IF/sheet5FE3DA15/PC15: U3.16 (A15), U3.28 (F15); also elsewhere on the board
/IF/~JABS: U3.48 (RS0); also elsewhere on the board
/IF/~J: U2.1, U3.44 (C0); also elsewhere on the board
/IF/~RST_sync: U2.3, U3.45 (I0), U3.46 (I1); also elsewhere on the board
GND: C2.2, C3.2, C4.2, U1.7 (GND), U2.7 (GND), U3.19 (GND), U3.26 (FTF), U3.27 (~OE), U3.47 (I2); also elsewhere on the board
unnamed: TP1.1, U1.2, U2.4
unnamed: TP2.1, U1.1, U2.2, U3.49 (RS1)
VCC: C2.1, C3.1, C4.1, U1.4, U1.5, U1.9, U1.10, U1.12, U1.13, U1.14 (VCC), U2.5, U2.9, U2.11, U2.13, U2.14 (VCC), U3.18 (VCC), U3.50 (FTAB), U3.51 (~ENB), U3.52 (~ENA); also elsewhere on the board

Notes on the sheet:
Stall the program counter by disabling the update of the IDT7381’s F register.
Flush the IF stage on Jump and on Reset. The flush during Reset ensures the pipeline is filled with NOPs.
Configure the ALU for FTAB=1 and FTF=0. This causes the A and B registers to by bypassed entirely. The F output updates on the next rising edge of the clock. During reset, set the ALU to I2=0, I1=0, I0=0. This causes the ALU to compute a zero and latch it in A on the rising edge of the clock regard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

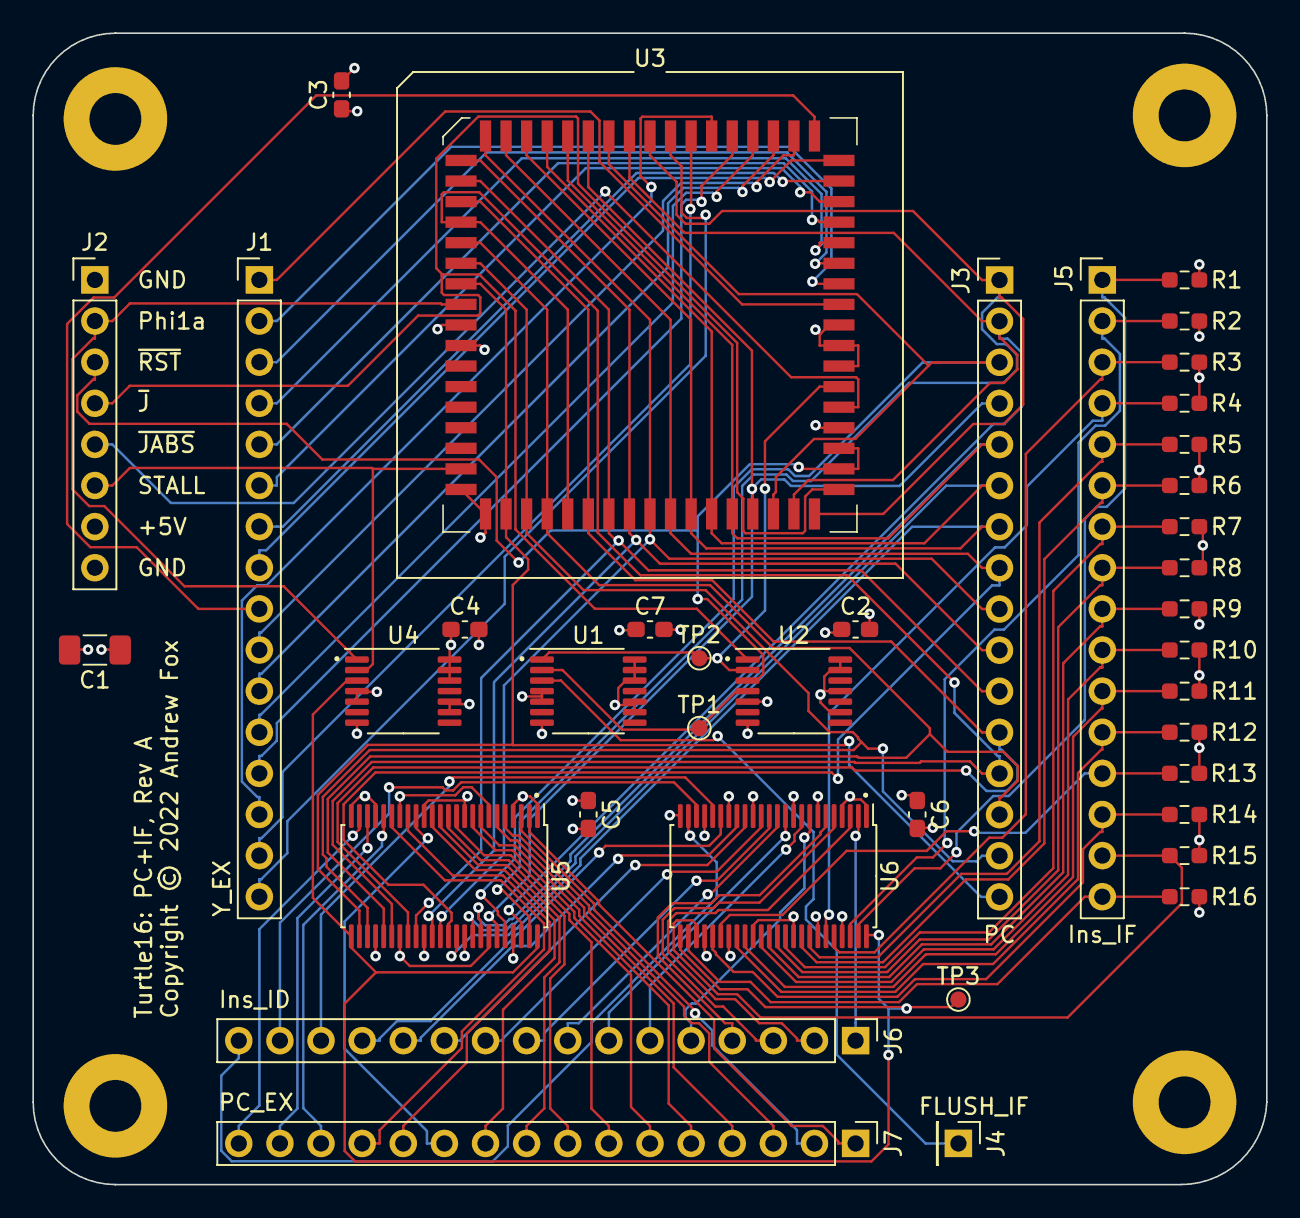
[picture p140: board PCIFModule.kicad_pcb from above]

Board: 4 copper layers, 76.2 x 71.1 mm, 43 parts (0 on the bottom side), 91 nets.
