foxostro/Turtle16/Hardware/ROMDaughterBoard/ROMDaughterBoard.kicad_pcb

## KiCad design Hardware/ROMDaughterBoard/ROMDaughterBoard.kicad_pcb (2025-06-30)

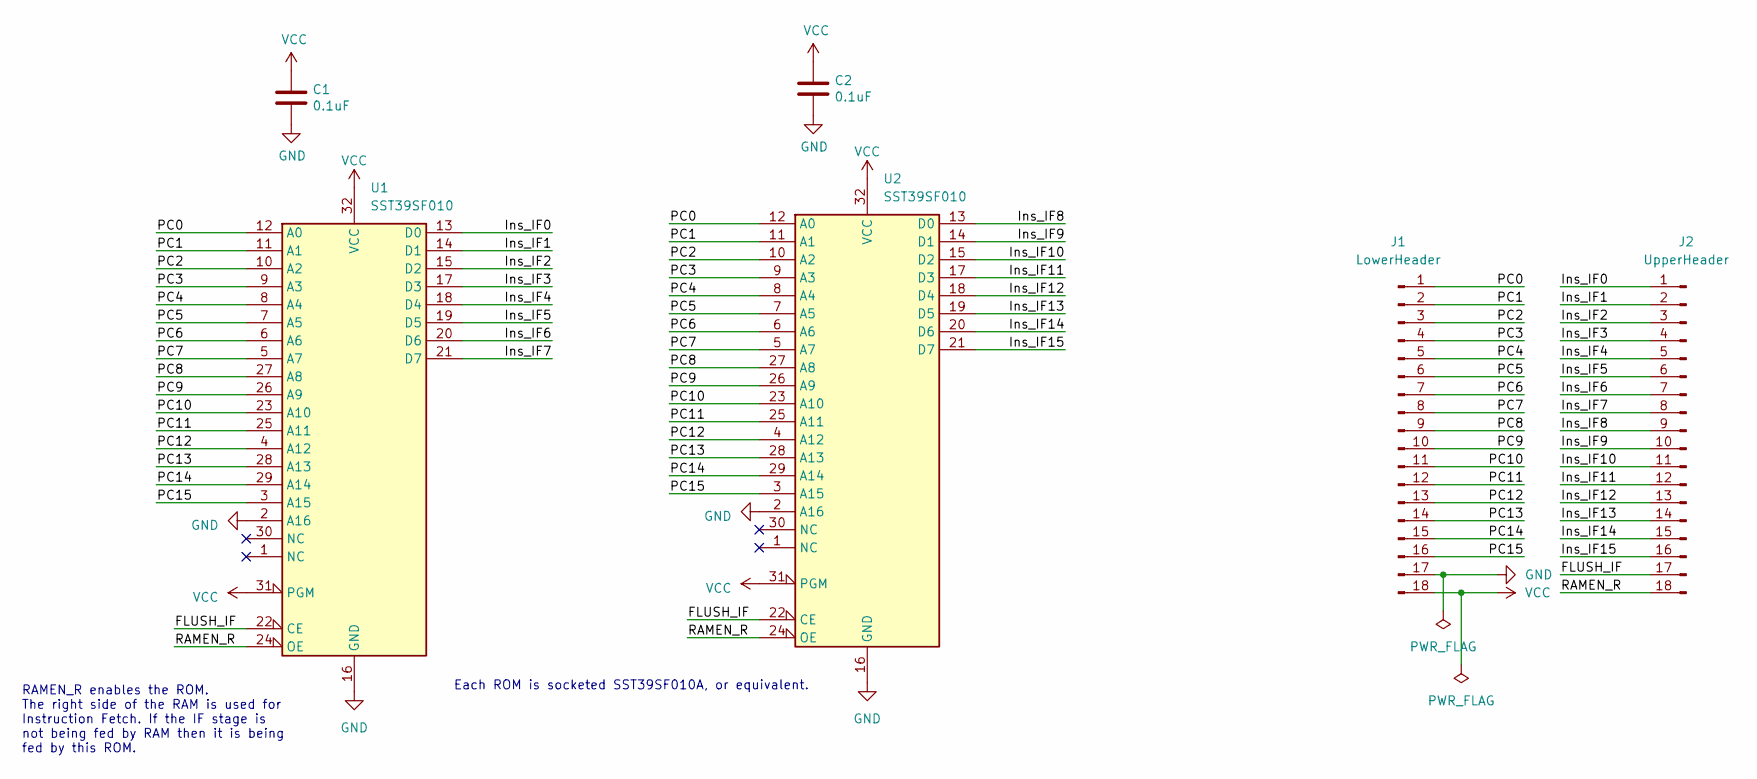
[picture p141: schematic ROMDaughterBoard.kicad_sch, Turtle16: ROM Daughter Board]

Parts:
C1, C2: 0.1uF; C_0603_1608Metric; Manufacturer# EMK107B7104KAHT; Mouser# 963-EMK107B7104KAHT
J1: LowerHeader; PinHeader_1x18_P2.54mm_Vertical
J2: UpperHeader; PinHeader_1x18_P2.54mm_Vertical
U1, U2: SST39SF010; 843221B1RKTP; Manufacturer# 8432-21B1-RK-TP; Mouser# 517-8432-21B1-RK-TP

Connections:
/FLUSH_IF: J2.17, U1.22 (CE), U2.22 (CE)
/Ins_IF0: J2.1, U1.13 (D0)
/Ins_IF1: J2.2, U1.14 (D1)
/Ins_IF2: J2.3, U1.15 (D2)
/Ins_IF3: J2.4, U1.17 (D3)
/Ins_IF4: J2.5, U1.18 (D4)
/Ins_IF5: J2.6, U1.19 (D5)
/Ins_IF6: J2.7, U1.20 (D6)
/Ins_IF7: J2.8, U1.21 (D7)
/Ins_IF8: J2.9, U2.13 (D0)
/Ins_IF9: J2.10, U2.14 (D1)
/Ins_IF10: J2.11, U2.15 (D2)
/Ins_IF11: J2.12, U2.17 (D3)
/Ins_IF12: J2.13, U2.18 (D4)
/Ins_IF13: J2.14, U2.19 (D5)
/Ins_IF14: J2.15, U2.20 (D6)
/Ins_IF15: J2.16, U2.21 (D7)
/PC0: J1.1, U1.12 (A0), U2.12 (A0)
/PC1: J1.2, U1.11 (A1), U2.11 (A1)
/PC2: J1.3, U1.10 (A2), U2.10 (A2)
/PC3: J1.4, U1.9 (A3), U2.9 (A3)
/PC4: J1.5, U1.8 (A4), U2.8 (A4)
/PC5: J1.6, U1.7 (A5), U2.7 (A5)
/PC6: J1.7, U1.6 (A6), U2.6 (A6)
/PC7: J1.8, U1.5 (A7), U2.5 (A7)
/PC8: J1.9, U1.27 (A8), U2.27 (A8)
/PC9: J1.10, U1.26 (A9), U2.26 (A9)
/PC10: J1.11, U1.23 (A10), U2.23 (A10)
/PC11: J1.12, U1.25 (A11), U2.25 (A11)
/PC12: J1.13, U1.4 (A12), U2.4 (A12)
/PC13: J1.14, U1.28 (A13), U2.28 (A13)
/PC14: J1.15, U1.29 (A14), U2.29 (A14)
/PC15: J1.16, U1.3 (A15), U2.3 (A15)
/RAMEN_R: J2.18, U1.24 (OE), U2.24 (OE)
GND: C1.2, C2.2, J1.17, U1.2 (A16), U1.16 (GND), U2.2 (A16), U2.16 (GND)
VCC: C1.1, C2.1, J1.18, U1.31 (PGM), U1.32 (VCC), U2.31 (PGM), U2.32 (VCC)

Notes on the sheet:
RAMEN_R enables the ROM. The right side of the RAM is used for Instruction Fetch. If the IF stage is not being fed by RAM then it is being fed by this ROM.
Each ROM is socketed SST39SF010A, or equivalent.

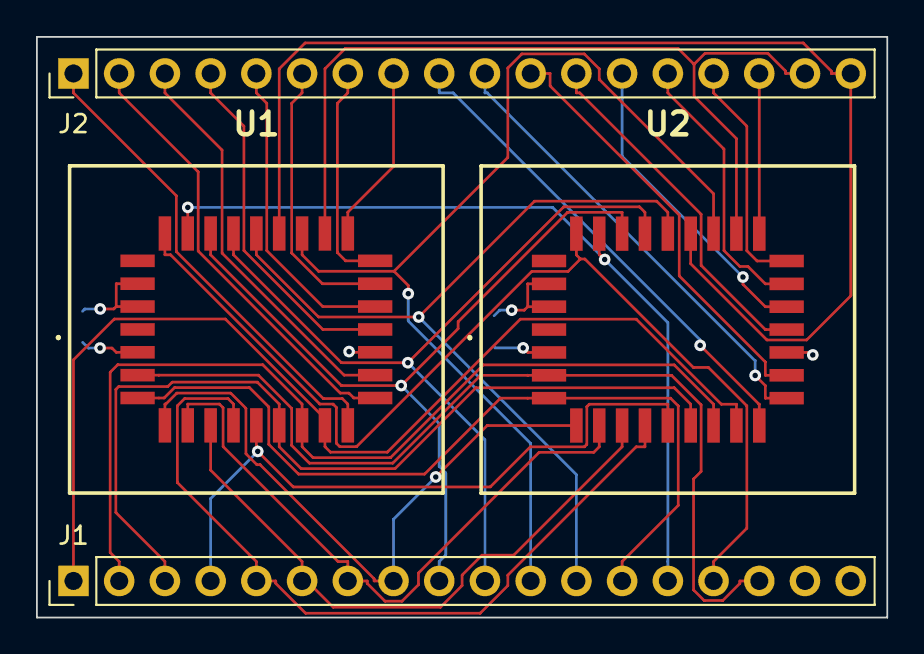
[picture p142: board ROMDaughterBoard.kicad_pcb from above]

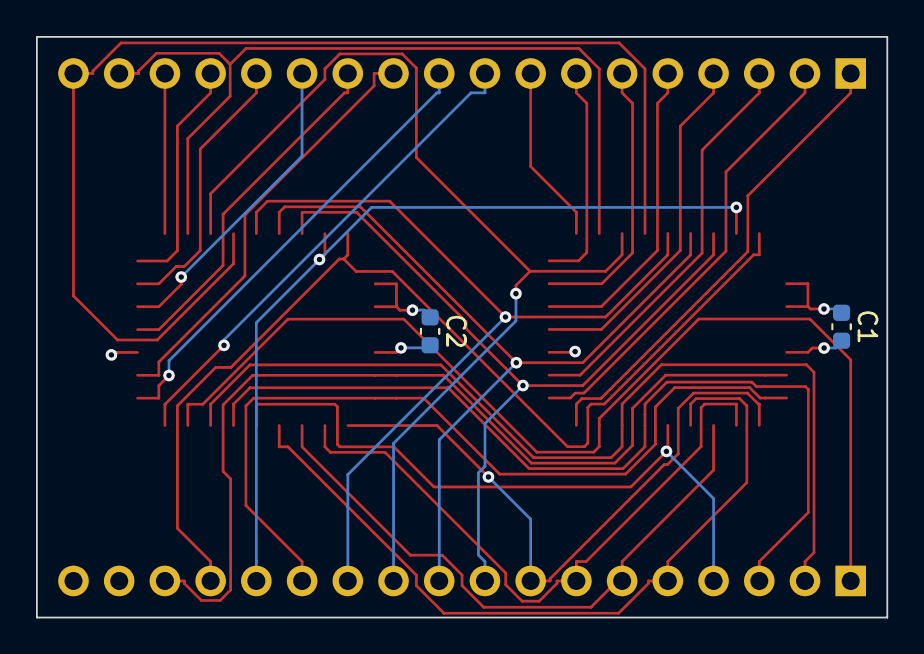
[picture p143: board ROMDaughterBoard.kicad_pcb from below]

Board: 4 copper layers, 47.2 x 32.3 mm, 6 parts (2 on the bottom side), 36 nets.
