foxostro/Turtle16/Hardware/ROMZIFBoard/ROMZIFBoard.kicad_pcb

## KiCad design Hardware/ROMZIFBoard/ROMZIFBoard.kicad_pcb (2025-06-30)

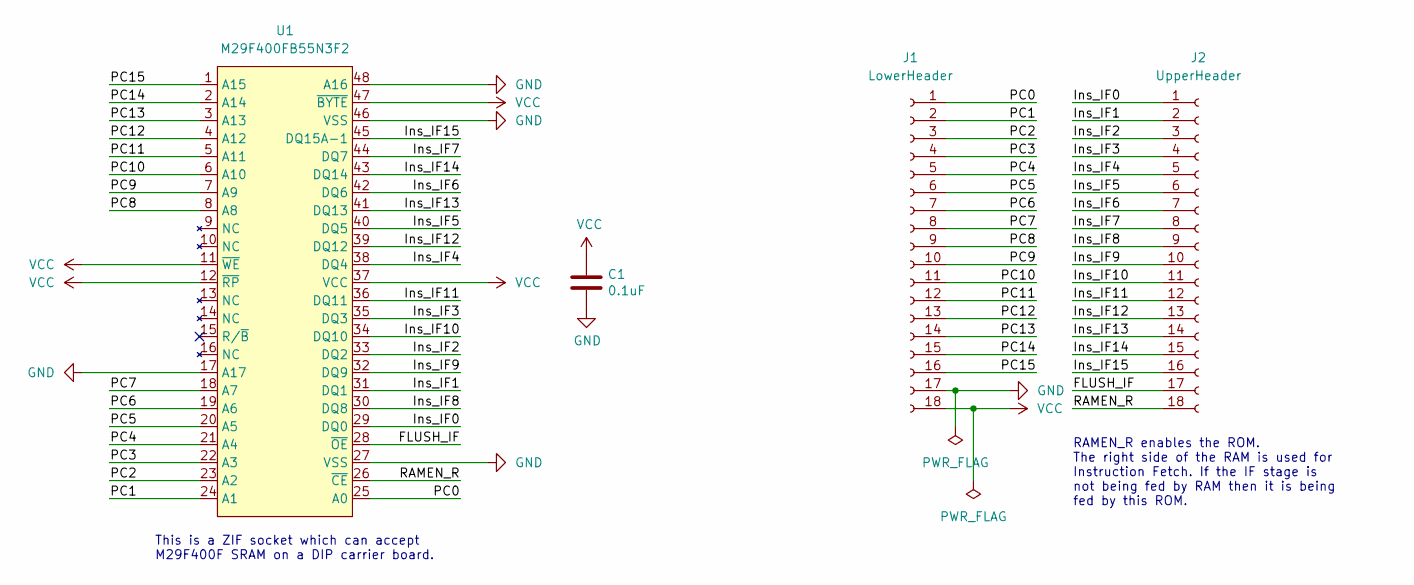
[picture p144: schematic ROMZIFBoard.kicad_sch, Turtle16: ROM ZIF Daughter Board]

Parts:
C1: 0.1uF; C_0603_1608Metric; Manufacturer# EMK107B7104KAHT; Mouser# 963-EMK107B7104KAHT
J1: LowerHeader; PinSocket_1x18_P2.54mm_Vertical
J2: UpperHeader; PinSocket_1x18_P2.54mm_Vertical
U1: M29F400FB55N3F2; DIP-48_W15.24mm_Socket; Manufacturer# 48-6554-10; Mouser# 535-48-6554-10

Connections:
/FLUSH_IF: J2.17, U1.28 (~OE)
/Ins_IF0: J2.1, U1.29 (DQ0)
/Ins_IF1: J2.2, U1.31 (DQ1)
/Ins_IF2: J2.3, U1.33 (DQ2)
/Ins_IF3: J2.4, U1.35 (DQ3)
/Ins_IF4: J2.5, U1.38 (DQ4)
/Ins_IF5: J2.6, U1.40 (DQ5)
/Ins_IF6: J2.7, U1.42 (DQ6)
/Ins_IF7: J2.8, U1.44 (DQ7)
/Ins_IF8: J2.9, U1.30 (DQ8)
/Ins_IF9: J2.10, U1.32 (DQ9)
/Ins_IF10: J2.11, U1.34 (DQ10)
/Ins_IF11: J2.12, U1.36 (DQ11)
/Ins_IF12: J2.13, U1.39 (DQ12)
/Ins_IF13: J2.14, U1.41 (DQ13)
/Ins_IF14: J2.15, U1.43 (DQ14)
/Ins_IF15: J2.16, U1.45 (DQ15A-1)
/PC0: J1.1, U1.25 (A0)
/PC1: J1.2, U1.24 (A1)
/PC2: J1.3, U1.23 (A2)
/PC3: J1.4, U1.22 (A3)
/PC4: J1.5, U1.21 (A4)
/PC5: J1.6, U1.20 (A5)
/PC6: J1.7, U1.19 (A6)
/PC7: J1.8, U1.18 (A7)
/PC8: J1.9, U1.8 (A8)
/PC9: J1.10, U1.7 (A9)
/PC10: J1.11, U1.6 (A10)
/PC11: J1.12, U1.5 (A11)
/PC12: J1.13, U1.4 (A12)
/PC13: J1.14, U1.3 (A13)
/PC14: J1.15, U1.2 (A14)
/PC15: J1.16, U1.1 (A15)
/RAMEN_R: J2.18, U1.26 (~CE)
GND: C1.2, J1.17, U1.17 (A17), U1.27 (VSS), U1.46 (VSS), U1.48 (A16)
VCC: C1.1, J1.18, U1.11 (~WE), U1.12 (~RP), U1.37 (VCC), U1.47 (~BYTE)

Notes on the sheet:
RAMEN_R enables the ROM. The right side of the RAM is used for Instruction Fetch. If the IF stage is not being fed by RAM then it is being fed by this ROM.
This is a ZIF socket which can accept M29F400F SRAM on a DIP carrier board.

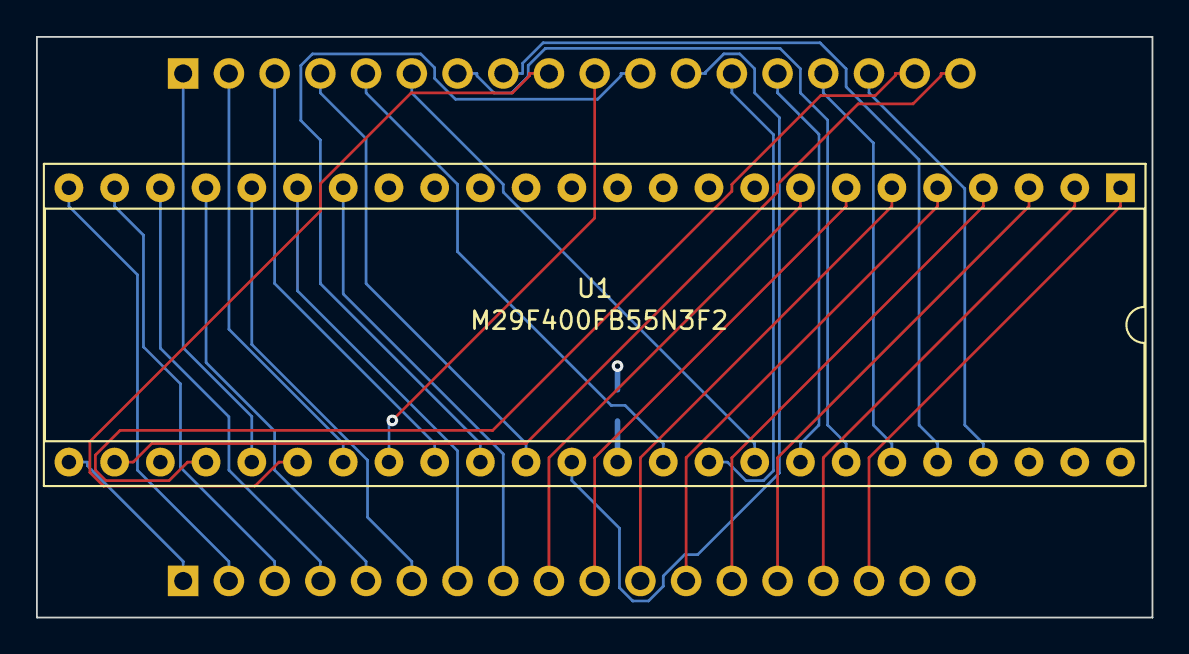
[picture p145: board ROMZIFBoard.kicad_pcb from above]

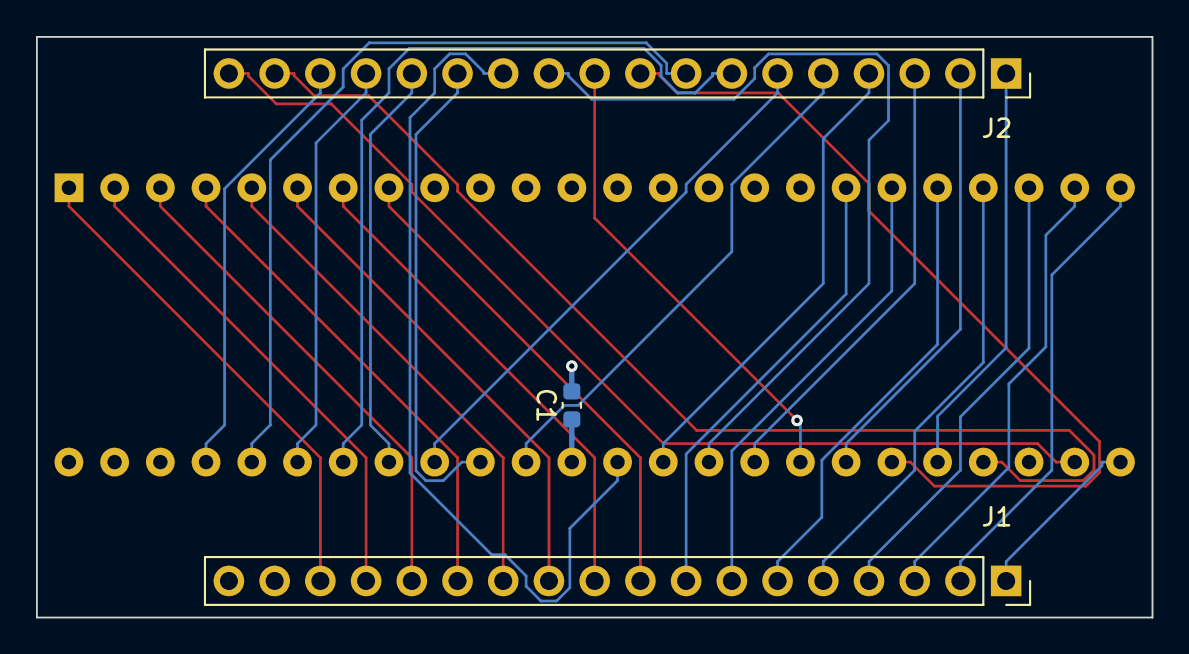
[picture p146: board ROMZIFBoard.kicad_pcb from below]

Board: 4 copper layers, 62.0 x 32.3 mm, 4 parts (3 on the bottom side), 36 nets.
