foxostro/Turtle16/Hardware/PrototypeProcessor/EXModuleTestFixture/EXModuleTestFixture.kicad_pcb

## KiCad design Hardware/PrototypeProcessor/EXModuleTestFixture/EXModuleTestFixture.kicad_pcb (2025-06-30)

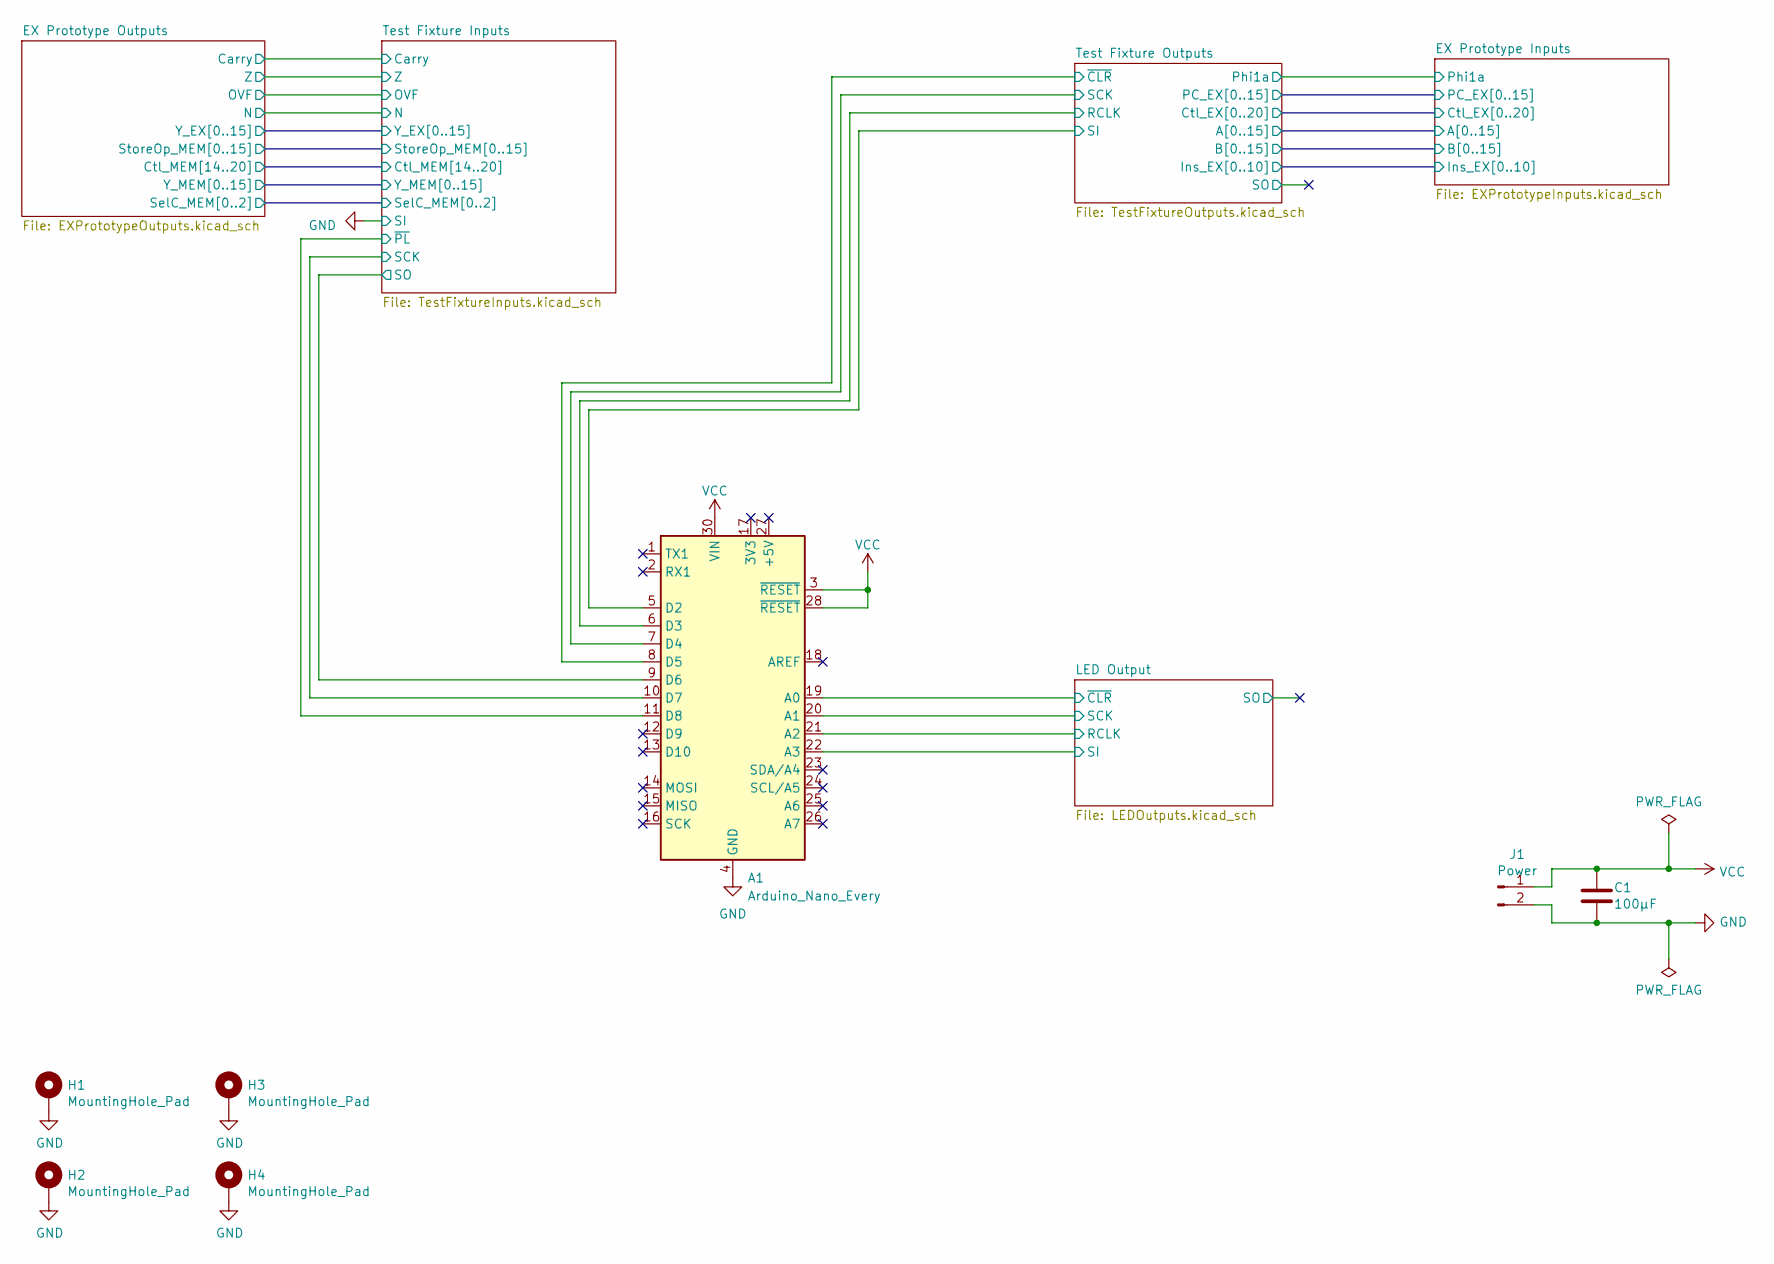
[picture p147: schematic EXModuleTestFixture.kicad_sch, Turtle16: EXModuleTestFixture]

Parts:
A1: Arduino_Nano_Every; Arduino_Nano
C1: 100µF; C_1206_3216Metric_Pad1.33x1.80mm_HandSolder
H1, H2, H3, H4: MountingHole_Pad; MountingHole_3.2mm_M3_Pad
J1: Power; 172448-0002

Connections:
/LED Output/RCLK: A1.21 (A2); also elsewhere on the board
/LED Output/SCK: A1.20 (A1); also elsewhere on the board
/LED Output/SI: A1.22 (A3); also elsewhere on the board
/LED Output/~CLR: A1.19 (A0); also elsewhere on the board
/Test Fixture Inputs/SCK: A1.10 (D7); also elsewhere on the board
/Test Fixture Inputs/SO: A1.9 (D6); also elsewhere on the board
/Test Fixture Inputs/~PL: A1.11 (D8); also elsewhere on the board
/Test Fixture Outputs/RCLK: A1.6 (D3); also elsewhere on the board
/Test Fixture Outputs/SCK: A1.7 (D4); also elsewhere on the board
/Test Fixture Outputs/SI: A1.5 (D2); also elsewhere on the board
/Test Fixture Outputs/~CLR: A1.8 (D5); also elsewhere on the board
GND: A1.4 (GND), A1.29 (GND), C1.2, H1.1, H2.1, H3.1, H4.1, J1.2; also elsewhere on the board
VCC: A1.3 (~RESET), A1.28 (~RESET), A1.30 (VIN), C1.1, J1.1; also elsewhere on the board
