foxostro/Turtle16/Hardware/PrototypeProcessor/EXModuleTestFixture/EXModuleTestFixture.kicad_pcb

## KiCad design Hardware/PrototypeProcessor/EXModuleTestFixture/EXModuleTestFixture.kicad_pcb (continued)

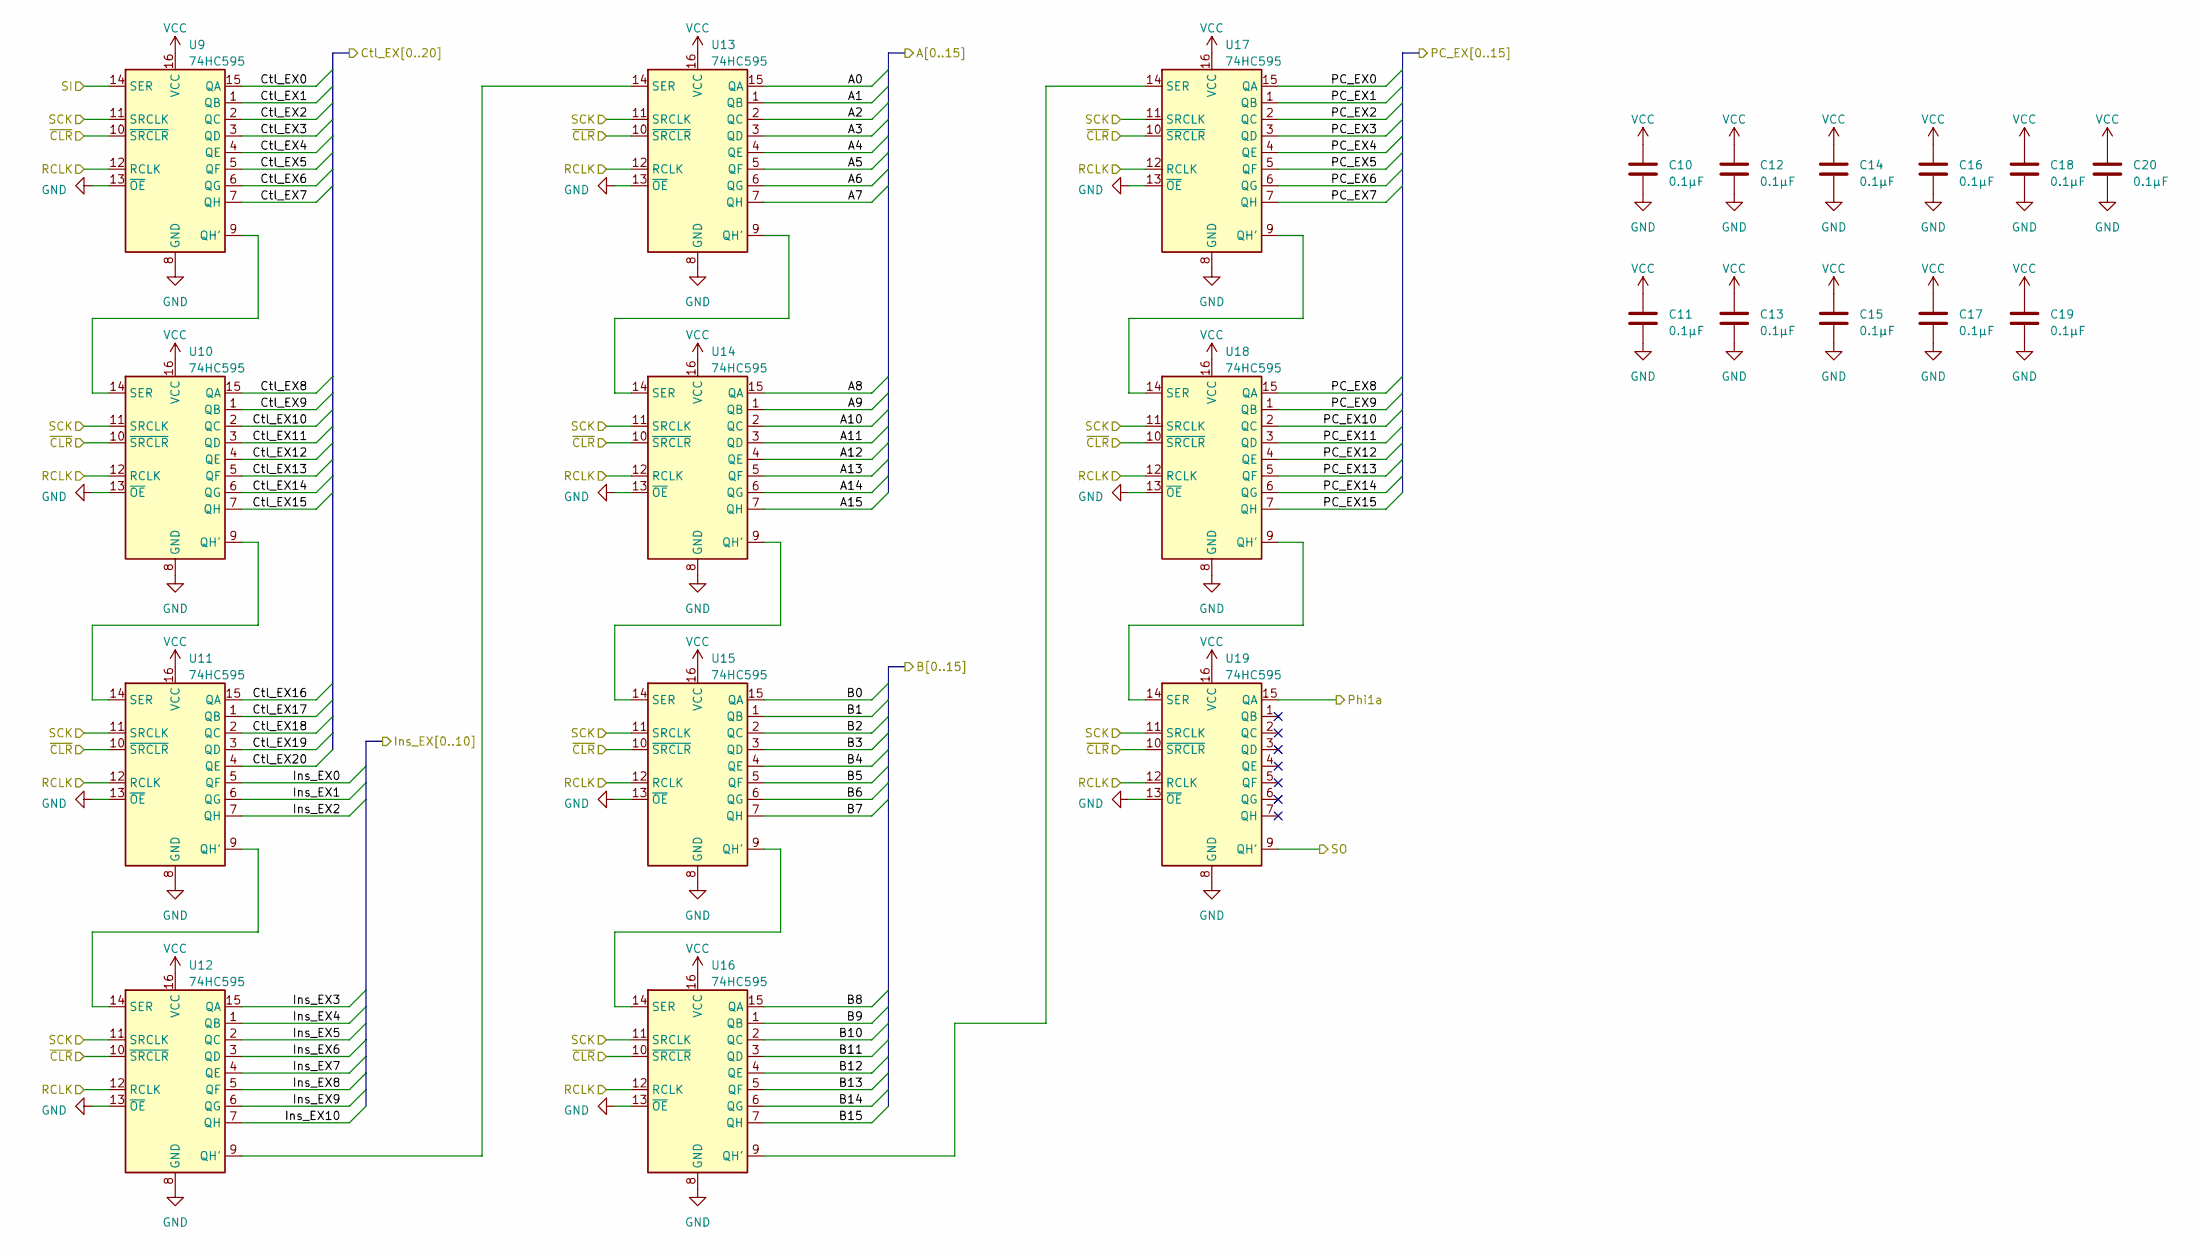
[picture p148: schematic TestFixtureOutputs.kicad_sch]

Parts:
C10, C11, C12, C13, C14, C15, C16, C17, C18, C19, C20: 0.1µF; C_0603_1608Metric
U9, U10, U11, U12, U13, U14, U15, U16, U17, U18, U19: 74HC595; TSSOP-16_4.4x5mm_P0.65mm

Connections:
/EX Prototype Inputs/A0: U13.15 (QA); also elsewhere on the board
/EX Prototype Inputs/A1: U13.1 (QB); also elsewhere on the board
/EX Prototype Inputs/A2: U13.2 (QC); also elsewhere on the board
/EX Prototype Inputs/A3: U13.3 (QD); also elsewhere on the board
/EX Prototype Inputs/A4: U13.4 (QE); also elsewhere on the board
/EX Prototype Inputs/A5: U13.5 (QF); also elsewhere on the board
/EX Prototype Inputs/A6: U13.6 (QG); also elsewhere on the board
/EX Prototype Inputs/A7: U13.7 (QH); also elsewhere on the board
/EX Prototype Inputs/A8: U14.15 (QA); also elsewhere on the board
/EX Prototype Inputs/A9: U14.1 (QB); also elsewhere on the board
/EX Prototype Inputs/A10: U14.2 (QC); also elsewhere on the board
/EX Prototype Inputs/A11: U14.3 (QD); also elsewhere on the board
/EX Prototype Inputs/A12: U14.4 (QE); also elsewhere on the board
/EX Prototype Inputs/A13: U14.5 (QF); also elsewhere on the board
/EX Prototype Inputs/A14: U14.6 (QG); also elsewhere on the board
/EX Prototype Inputs/A15: U14.7 (QH); also elsewhere on the board
/EX Prototype Inputs/B0: U15.15 (QA); also elsewhere on the board
/EX Prototype Inputs/B1: U15.1 (QB); also elsewhere on the board
/EX Prototype Inputs/B2: U15.2 (QC); also elsewhere on the board
/EX Prototype Inputs/B3: U15.3 (QD); also elsewhere on the board
/EX Prototype Inputs/B4: U15.4 (QE); also elsewhere on the board
/EX Prototype Inputs/B5: U15.5 (QF); also elsewhere on the board
/EX Prototype Inputs/B6: U15.6 (QG); also elsewhere on the board
/EX Prototype Inputs/B7: U15.7 (QH); also elsewhere on the board
/EX Prototype Inputs/B8: U16.15 (QA); also elsewhere on the board
/EX Prototype Inputs/B9: U16.1 (QB); also elsewhere on the board
/EX Prototype Inputs/B10: U16.2 (QC); also elsewhere on the board
/EX Prototype Inputs/B11: U16.3 (QD); also elsewhere on the board
/EX Prototype Inputs/B12: U16.4 (QE); also elsewhere on the board
/EX Prototype Inputs/B13: U16.5 (QF); also elsewhere on the board
/EX Prototype Inputs/B14: U16.6 (QG); also elsewhere on the board
/EX Prototype Inputs/B15: U16.7 (QH); also elsewhere on the board
/EX Prototype Inputs/Ctl_EX0: U9.15 (QA); also elsewhere on the board
/EX Prototype Inputs/Ctl_EX1: U9.1 (QB); also elsewhere on the board
/EX Prototype Inputs/Ctl_EX2: U9.2 (QC); also elsewhere on the board
/EX Prototype Inputs/Ctl_EX3: U9.3 (QD); also elsewhere on the board
/EX Prototype Inputs/Ctl_EX4: U9.4 (QE); also elsewhere on the board
/EX Prototype Inputs/Ctl_EX5: U9.5 (QF); also elsewhere on the board
/EX Prototype Inputs/Ctl_EX6: U9.6 (QG); also elsewhere on the board
/EX Prototype Inputs/Ctl_EX7: U9.7 (QH); also elsewhere on the board
/EX Prototype Inputs/Ctl_EX8: U10.15 (QA); also elsewhere on the board
/EX Prototype Inputs/Ctl_EX9: U10.1 (QB); also elsewhere on the board
/EX Prototype Inputs/Ctl_EX10: U10.2 (QC); also elsewhere on the board
/EX Prototype Inputs/Ctl_EX11: U10.3 (QD); also elsewhere on the board
/EX Prototype Inputs/Ctl_EX12: U10.4 (QE); also elsewhere on the board
/EX Prototype Inputs/Ctl_EX13: U10.5 (QF); also elsewhere on the board
/EX Prototype Inputs/Ctl_EX14: U10.6 (QG); also elsewhere on the board
/EX Prototype Inputs/Ctl_EX15: U10.7 (QH); also elsewhere on the board
/EX Prototype Inputs/Ctl_EX16: U11.15 (QA); also elsewhere on the board
/EX Prototype Inputs/Ctl_EX17: U11.1 (QB); also elsewhere on the board
/EX Prototype Inputs/Ctl_EX18: U11.2 (QC); also elsewhere on the board
/EX Prototype Inputs/Ctl_EX19: U11.3 (QD); also elsewhere on the board
/EX Prototype Inputs/Ctl_EX20: U11.4 (QE); also elsewhere on the board
/EX Prototype Inputs/Ins_EX0: U11.5 (QF); also elsewhere on the board
/EX Prototype Inputs/Ins_EX1: U11.6 (QG); also elsewhere on the board
/EX Prototype Inputs/Ins_EX2: U11.7 (QH); also elsewhere on the board
/EX Prototype Inputs/Ins_EX3: U12.15 (QA); also elsewhere on the board
/EX Prototype Inputs/Ins_EX4: U12.1 (QB); also elsewhere on the board
/EX Prototype Inputs/Ins_EX5: U12.2 (QC); also elsewhere on the board
/EX Prototype Inputs/Ins_EX6: U12.3 (QD); also elsewhere on the board
/EX Prototype Inputs/Ins_EX7: U12.4 (QE); also elsewhere on the board
/EX Prototype Inputs/Ins_EX8: U12.5 (QF); also elsewhere on the board
/EX Prototype Inputs/Ins_EX9: U12.6 (QG); also elsewhere on the board
/EX Prototype Inputs/Ins_EX10: U12.7 (QH); also elsewhere on the board
/EX Prototype Inputs/PC_EX0: U17.15 (QA); also elsewhere on the board
/EX Prototype Inputs/PC_EX1: U17.1 (QB); also elsewhere on the board
/EX Prototype Inputs/PC_EX2: U17.2 (QC); also elsewhere on the board
/EX Prototype Inputs/PC_EX3: U17.3 (QD); also elsewhere on the board
/EX Prototype Inputs/PC_EX4: U17.4 (QE); also elsewhere on the board
/EX Prototype Inputs/PC_EX5: U17.5 (QF); also elsewhere on the board
/EX Prototype Inputs/PC_EX6: U17.6 (QG); also elsewhere on the board
/EX Prototype Inputs/PC_EX7: U17.7 (QH); also elsewhere on the board
/EX Prototype Inputs/PC_EX8: U18.15 (QA); also elsewhere on the board
/EX Prototype Inputs/PC_EX9: U18.1 (QB); also elsewhere on the board
/EX Prototype Inputs/PC_EX10: U18.2 (QC); also elsewhere on the board
/EX Prototype Inputs/PC_EX11: U18.3 (QD); also elsewhere on the board
/EX Prototype Inputs/PC_EX12: U18.4 (QE); also elsewhere on the board
/EX Prototype Inputs/PC_EX13: U18.5 (QF); also elsewhere on the board
/EX Prototype Inputs/PC_EX14: U18.6 (QG); also elsewhere on the board
/EX Prototype Inputs/PC_EX15: U18.7 (QH); also elsewhere on the board
/EX Prototype Inputs/Phi1a: U19.15 (QA); also elsewhere on the board
/Test Fixture Outputs/RCLK: U9.12 (RCLK), U10.12 (RCLK), U11.12 (RCLK), U12.12 (RCLK), U13.12 (RCLK), U14.12 (RCLK), U15.12 (RCLK), U16.12 (RCLK), U17.12 (RCLK), U18.12 (RCLK), U19.12 (RCLK); also elsewhere on the board
/Test Fixture Outputs/SCK: U9.11 (SRCLK), U10.11 (SRCLK), U11.11 (SRCLK), U12.11 (SRCLK), U13.11 (SRCLK), U14.11 (SRCLK), U15.11 (SRCLK), U16.11 (SRCLK), U17.11 (SRCLK), U18.11 (SRCLK), U19.11 (SRCLK); also elsewhere on the board
/Test Fixture Outputs/SI: U9.14 (SER); also elsewhere on the board
/Test Fixture Outputs/SO: U19.9 (QH')
/Test Fixture Outputs/~CLR: U9.10 (~SRCLR), U10.10 (~SRCLR), U11.10 (~SRCLR), U12.10 (~SRCLR), U13.10 (~SRCLR), U14.10 (~SRCLR), U15.10 (~SRCLR), U16.10 (~SRCLR), U17.10 (~SRCLR), U18.10 (~SRCLR), U19.10 (~SRCLR); also elsewhere on the board
GND: C10.2, C11.2, C12.2, C13.2, C14.2, C15.2, C16.2, C17.2, C18.2, C19.2, C20.2, U9.8 (GND), U9.13 (~OE), U10.8 (GND), U10.13 (~OE), U11.8 (GND), U11.13 (~OE), U12.8 (GND), U12.13 (~OE), U13.8 (GND), U13.13 (~OE), U14.8 (GND), U14.13 (~OE), U15.8 (GND), U15.13 (~OE), U16.8 (GND), U16.13 (~OE), U17.8 (GND), U17.13 (~OE), U18.8 (GND), U18.13 (~OE), U19.8 (GND), U19.13 (~OE); also elsewhere on the board
unnamed: U10.9 (QH'), U11.14 (SER)
unnamed: U9.9 (QH'), U10.14 (SER)
unnamed: U11.9 (QH'), U12.14 (SER)
unnamed: U12.9 (QH'), U13.14 (SER)
unnamed: U13.9 (QH'), U14.14 (SER)
unnamed: U14.9 (QH'), U15.14 (SER)
unnamed: U15.9 (QH'), U16.14 (SER)
unnamed: U16.9 (QH'), U17.14 (SER)
unnamed: U17.9 (QH'), U18.14 (SER)
unnamed: U18.9 (QH'), U19.14 (SER)
VCC: C10.1, C11.1, C12.1, C13.1, C14.1, C15.1, C16.1, C17.1, C18.1, C19.1, C20.1, U9.16 (VCC), U10.16 (VCC), U11.16 (VCC), U12.16 (VCC), U13.16 (VCC), U14.16 (VCC), U15.16 (VCC), U16.16 (VCC), U17.16 (VCC), U18.16 (VCC), U19.16 (VCC); also elsewhere on the board

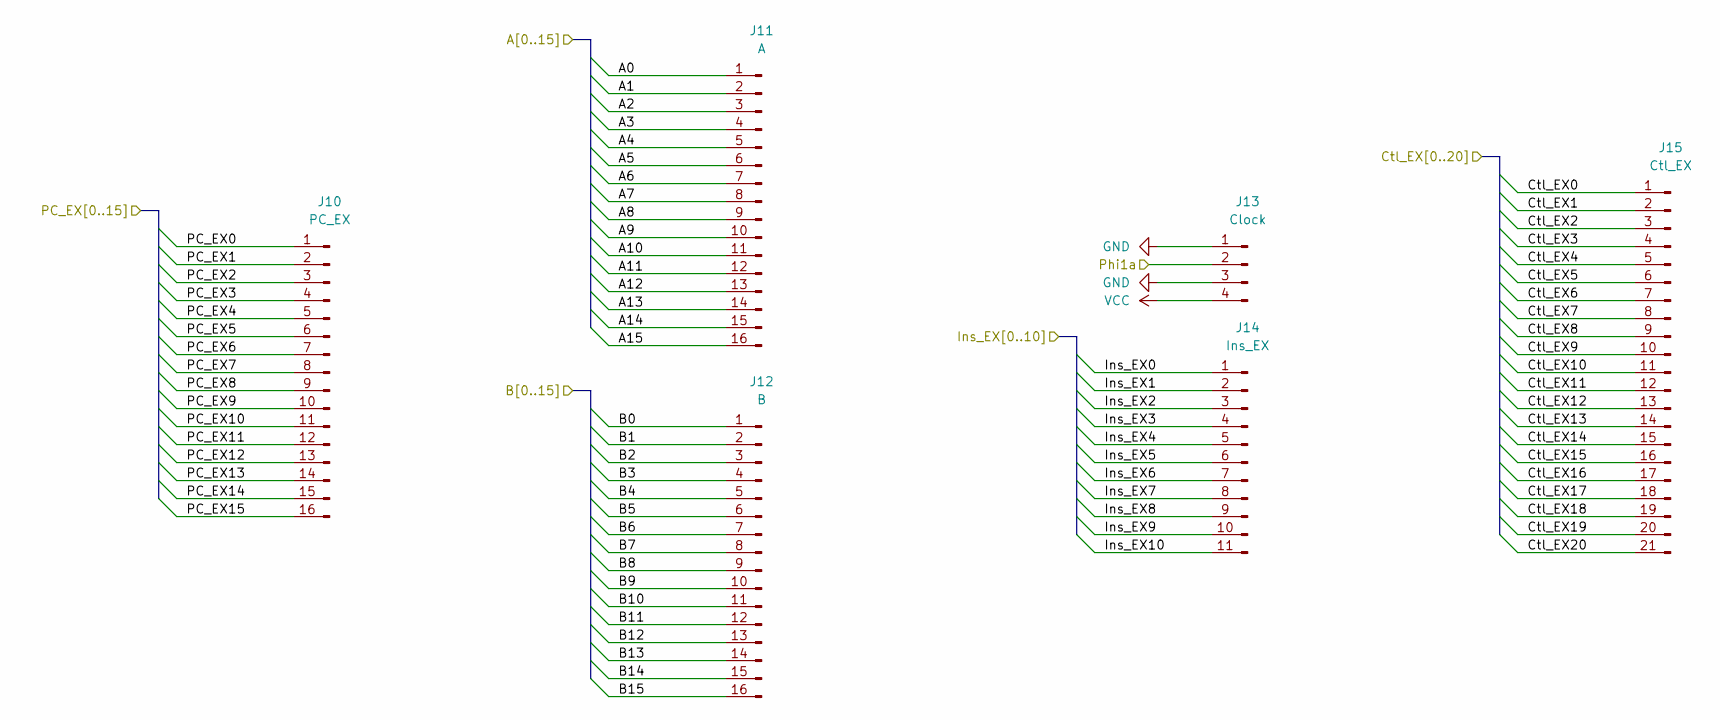
[picture p149: schematic EXPrototypeInputs.kicad_sch, Turtle16: EX Module Inputs]

Parts:
J10: PC_EX; PinHeader_1x16_P2.54mm_Vertical
J11: A; PinHeader_1x16_P2.54mm_Vertical
J12: B; PinHeader_1x16_P2.54mm_Vertical
J13: Clock; PinHeader_1x04_P2.54mm_Vertical
J14: Ins_EX; PinHeader_1x11_P2.54mm_Vertical
J15: Ctl_EX; PinHeader_1x21_P2.54mm_Vertical

Connections:
/EX Prototype Inputs/A0: J11.1; also elsewhere on the board
/EX Prototype Inputs/A1: J11.2; also elsewhere on the board
/EX Prototype Inputs/A2: J11.3; also elsewhere on the board
/EX Prototype Inputs/A3: J11.4; also elsewhere on the board
/EX Prototype Inputs/A4: J11.5; also elsewhere on the board
/EX Prototype Inputs/A5: J11.6; also elsewhere on the board
/EX Prototype Inputs/A6: J11.7; also elsewhere on the board
/EX Prototype Inputs/A7: J11.8; also elsewhere on the board
/EX Prototype Inputs/A8: J11.9; also elsewhere on the board
/EX Prototype Inputs/A9: J11.10; also elsewhere on the board
/EX Prototype Inputs/A10: J11.11; also elsewhere on the board
/EX Prototype Inputs/A11: J11.12; also elsewhere on the board
/EX Prototype Inputs/A12: J11.13; also elsewhere on the board
/EX Prototype Inputs/A13: J11.14; also elsewhere on the board
/EX Prototype Inputs/A14: J11.15; also elsewhere on the board
/EX Prototype Inputs/A15: J11.16; also elsewhere on the board
/EX Prototype Inputs/B0: J12.1; also elsewhere on the board
/EX Prototype Inputs/B1: J12.2; also elsewhere on the board
/EX Prototype Inputs/B2: J12.3; also elsewhere on the board
/EX Prototype Inputs/B3: J12.4; also elsewhere on the board
/EX Prototype Inputs/B4: J12.5; also elsewhere on the board
/EX Prototype Inputs/B5: J12.6; also elsewhere on the board
/EX Prototype Inputs/B6: J12.7; also elsewhere on the board
/EX Prototype Inputs/B7: J12.8; also elsewhere on the board
/EX Prototype Inputs/B8: J12.9; also elsewhere on the board
/EX Prototype Inputs/B9: J12.10; also elsewhere on the board
/EX Prototype Inputs/B10: J12.11; also elsewhere on the board
/EX Prototype Inputs/B11: J12.12; also elsewhere on the board
/EX Prototype Inputs/B12: J12.13; also elsewhere on the board
/EX Prototype Inputs/B13: J12.14; also elsewhere on the board
/EX Prototype Inputs/B14: J12.15; also elsewhere on the board
/EX Prototype Inputs/B15: J12.16; also elsewhere on the board
/EX Prototype Inputs/Ctl_EX0: J15.1; also elsewhere on the board
/EX Prototype Inputs/Ctl_EX1: J15.2; also elsewhere on the board
/EX Prototype Inputs/Ctl_EX2: J15.3; also elsewhere on the board
/EX Prototype Inputs/Ctl_EX3: J15.4; also elsewhere on the board
/EX Prototype Inputs/Ctl_EX4: J15.5; also elsewhere on the board
/EX Prototype Inputs/Ctl_EX5: J15.6; also elsewhere on the board
/EX Prototype Inputs/Ctl_EX6: J15.7; also elsewhere on the board
/EX Prototype Inputs/Ctl_EX7: J15.8; also elsewhere on the board
/EX Prototype Inputs/Ctl_EX8: J15.9; also elsewhere on the board
/EX Prototype Inputs/Ctl_EX9: J15.10; also elsewhere on the board
/EX Prototype Inputs/Ctl_EX10: J15.11; also elsewhere on the board
/EX Prototype Inputs/Ctl_EX11: J15.12; also elsewhere on the board
/EX Prototype Inputs/Ctl_EX12: J15.13; also elsewhere on the board
/EX Prototype Inputs/Ctl_EX13: J15.14; also elsewhere on the board
/EX Prototype Inputs/Ctl_EX14: J15.15; also elsewhere on the board
/EX Prototype Inputs/Ctl_EX15: J15.16; also elsewhere on the board
/EX Prototype Inputs/Ctl_EX16: J15.17; also elsewhere on the board
/EX Prototype Inputs/Ctl_EX17: J15.18; also elsewhere on the board
/EX Prototype Inputs/Ctl_EX18: J15.19; also elsewhere on the board
/EX Prototype Inputs/Ctl_EX19: J15.20; also elsewhere on the board
/EX Prototype Inputs/Ctl_EX20: J15.21; also elsewhere on the board
/EX Prototype Inputs/Ins_EX0: J14.1; also elsewhere on the board
/EX Prototype Inputs/Ins_EX1: J14.2; also elsewhere on the board
/EX Prototype Inputs/Ins_EX2: J14.3; also elsewhere on the board
/EX Prototype Inputs/Ins_EX3: J14.4; also elsewhere on the board
/EX Prototype Inputs/Ins_EX4: J14.5; also elsewhere on the board
/EX Prototype Inputs/Ins_EX5: J14.6; also elsewhere on the board
/EX Prototype Inputs/Ins_EX6: J14.7; also elsewhere on the board
/EX Prototype Inputs/Ins_EX7: J14.8; also elsewhere on the board
/EX Prototype Inputs/Ins_EX8: J14.9; also elsewhere on the board
/EX Prototype Inputs/Ins_EX9: J14.10; also elsewhere on the board
/EX Prototype Inputs/Ins_EX10: J14.11; also elsewhere on the board
/EX Prototype Inputs/PC_EX0: J10.1; also elsewhere on the board
/EX Prototype Inputs/PC_EX1: J10.2; also elsewhere on the board
/EX Prototype Inputs/PC_EX2: J10.3; also elsewhere on the board
/EX Prototype Inputs/PC_EX3: J10.4; also elsewhere on the board
/EX Prototype Inputs/PC_EX4: J10.5; also elsewhere on the board
/EX Prototype Inputs/PC_EX5: J10.6; also elsewhere on the board
/EX Prototype Inputs/PC_EX6: J10.7; also elsewhere on the board
/EX Prototype Inputs/PC_EX7: J10.8; also elsewhere on the board
/EX Prototype Inputs/PC_EX8: J10.9; also elsewhere on the board
/EX Prototype Inputs/PC_EX9: J10.10; also elsewhere on the board
/EX Prototype Inputs/PC_EX10: J10.11; also elsewhere on the board
/EX Prototype Inputs/PC_EX11: J10.12; also elsewhere on the board
/EX Prototype Inputs/PC_EX12: J10.13; also elsewhere on the board
/EX Prototype Inputs/PC_EX13: J10.14; also elsewhere on the board
/EX Prototype Inputs/PC_EX14: J10.15; also elsewhere on the board
/EX Prototype Inputs/PC_EX15: J10.16; also elsewhere on the board
/EX Prototype Inputs/Phi1a: J13.2; also elsewhere on the board
GND: J13.1, J13.3; also elsewhere on the board
VCC: J13.4; also elsewhere on the board

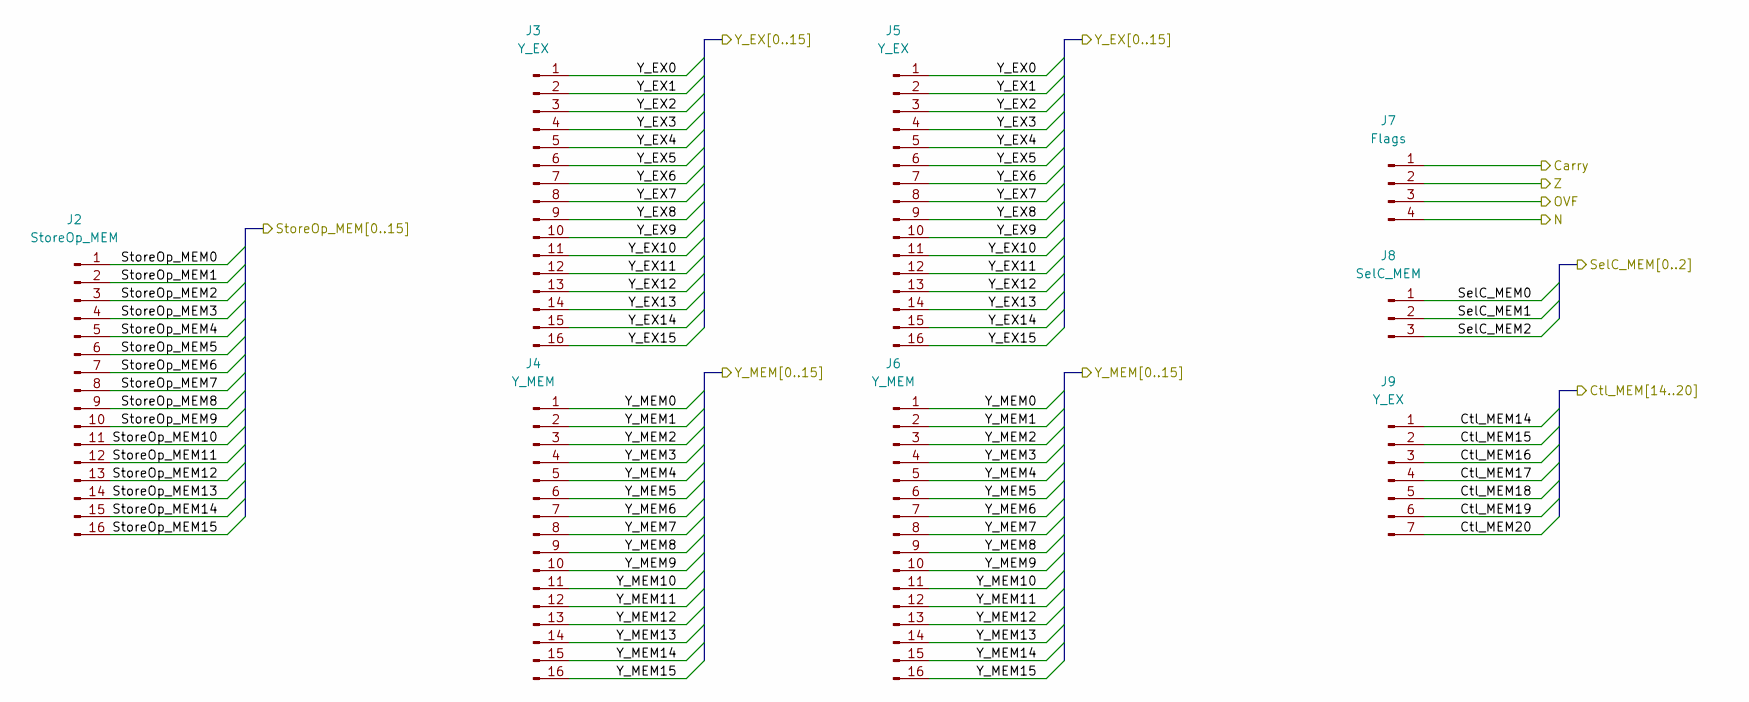
[picture p150: schematic EXPrototypeOutputs.kicad_sch, Turtle16: EX Module Outputs]

Parts:
J2: StoreOp_MEM; PinHeader_1x16_P2.54mm_Vertical
J3, J5: Y_EX; PinHeader_1x16_P2.54mm_Vertical
J4, J6: Y_MEM; PinHeader_1x16_P2.54mm_Vertical
J7: Flags; PinHeader_1x04_P2.54mm_Vertical
J8: SelC_MEM; PinHeader_1x03_P2.54mm_Vertical
J9: Y_EX; PinHeader_1x07_P2.54mm_Vertical

Connections:
/EX Prototype Outputs/Carry: J7.1; also elsewhere on the board
/EX Prototype Outputs/Ctl_MEM14: J9.1; also elsewhere on the board
/EX Prototype Outputs/Ctl_MEM15: J9.2; also elsewhere on the board
/EX Prototype Outputs/Ctl_MEM16: J9.3; also elsewhere on the board
/EX Prototype Outputs/Ctl_MEM17: J9.4; also elsewhere on the board
/EX Prototype Outputs/Ctl_MEM18: J9.5; also elsewhere on the board
/EX Prototype Outputs/Ctl_MEM19: J9.6; also elsewhere on the board
/EX Prototype Outputs/Ctl_MEM20: J9.7; also elsewhere on the board
/EX Prototype Outputs/N: J7.4; also elsewhere on the board
/EX Prototype Outputs/OVF: J7.3; also elsewhere on the board
/EX Prototype Outputs/SelC_MEM0: J8.1; also elsewhere on the board
/EX Prototype Outputs/SelC_MEM1: J8.2; also elsewhere on the board
/EX Prototype Outputs/SelC_MEM2: J8.3; also elsewhere on the board
/EX Prototype Outputs/StoreOp_MEM0: J2.1; also elsewhere on the board
/EX Prototype Outputs/StoreOp_MEM1: J2.2; also elsewhere on the board
/EX Prototype Outputs/StoreOp_MEM2: J2.3; also elsewhere on the board
/EX Prototype Outputs/StoreOp_MEM3: J2.4; also elsewhere on the board
/EX Prototype Outputs/StoreOp_MEM4: J2.5; also elsewhere on the board
/EX Prototype Outputs/StoreOp_MEM5: J2.6; also elsewhere on the board
/EX Prototype Outputs/StoreOp_MEM6: J2.7; also elsewhere on the board
/EX Prototype Outputs/StoreOp_MEM7: J2.8; also elsewhere on the board
/EX Prototype Outputs/StoreOp_MEM8: J2.9; also elsewhere on the board
/EX Prototype Outputs/StoreOp_MEM9: J2.10; also elsewhere on the board
/EX Prototype Outputs/StoreOp_MEM10: J2.11; also elsewhere on the board
/EX Prototype Outputs/StoreOp_MEM11: J2.12; also elsewhere on the board
/EX Prototype Outputs/StoreOp_MEM12: J2.13; also elsewhere on the board
/EX Prototype Outputs/StoreOp_MEM13: J2.14; also elsewhere on the board
/EX Prototype Outputs/StoreOp_MEM14: J2.15; also elsewhere on the board
/EX Prototype Outputs/StoreOp_MEM15: J2.16; also elsewhere on the board
/EX Prototype Outputs/Y_EX0: J3.1, J5.1; also elsewhere on the board
/EX Prototype Outputs/Y_EX1: J3.2, J5.2; also elsewhere on the board
/EX Prototype Outputs/Y_EX2: J3.3, J5.3; also elsewhere on the board
/EX Prototype Outputs/Y_EX3: J3.4, J5.4; also elsewhere on the board
/EX Prototype Outputs/Y_EX4: J3.5, J5.5; also elsewhere on the board
/EX Prototype Outputs/Y_EX5: J3.6, J5.6; also elsewhere on the board
/EX Prototype Outputs/Y_EX6: J3.7, J5.7; also elsewhere on the board
/EX Prototype Outputs/Y_EX7: J3.8, J5.8; also elsewhere on the board
/EX Prototype Outputs/Y_EX8: J3.9, J5.9; also elsewhere on the board
/EX Prototype Outputs/Y_EX9: J3.10, J5.10; also elsewhere on the board
/EX Prototype Outputs/Y_EX10: J3.11, J5.11; also elsewhere on the board
/EX Prototype Outputs/Y_EX11: J3.12, J5.12; also elsewhere on the board
/EX Prototype Outputs/Y_EX12: J3.13, J5.13; also elsewhere on the board
/EX Prototype Outputs/Y_EX13: J3.14, J5.14; also elsewhere on the board
/EX Prototype Outputs/Y_EX14: J3.15, J5.15; also elsewhere on the board
/EX Prototype Outputs/Y_EX15: J3.16, J5.16; also elsewhere on the board
/EX Prototype Outputs/Y_MEM0: J4.1, J6.1; also elsewhere on the board
/EX Prototype Outputs/Y_MEM1: J4.2, J6.2; also elsewhere on the board
/EX Prototype Outputs/Y_MEM2: J4.3, J6.3; also elsewhere on the board
/EX Prototype Outputs/Y_MEM3: J4.4, J6.4; also elsewhere on the board
/EX Prototype Outputs/Y_MEM4: J4.5, J6.5; also elsewhere on the board
/EX Prototype Outputs/Y_MEM5: J4.6, J6.6; also elsewhere on the board
/EX Prototype Outputs/Y_MEM6: J4.7, J6.7; also elsewhere on the board
/EX Prototype Outputs/Y_MEM7: J4.8, J6.8; also elsewhere on the board
/EX Prototype Outputs/Y_MEM8: J4.9, J6.9; also elsewhere on the board
/EX Prototype Outputs/Y_MEM9: J4.10, J6.10; also elsewhere on the board
/EX Prototype Outputs/Y_MEM10: J4.11, J6.11; also elsewhere on the board
/EX Prototype Outputs/Y_MEM11: J4.12, J6.12; also elsewhere on the board
/EX Prototype Outputs/Y_MEM12: J4.13, J6.13; also elsewhere on the board
/EX Prototype Outputs/Y_MEM13: J4.14, J6.14; also elsewhere on the board
/EX Prototype Outputs/Y_MEM14: J4.15, J6.15; also elsewhere on the board
/EX Prototype Outputs/Y_MEM15: J4.16, J6.16; also elsewhere on the board
/EX Prototype Outputs/Z: J7.2; also elsewhere on the board

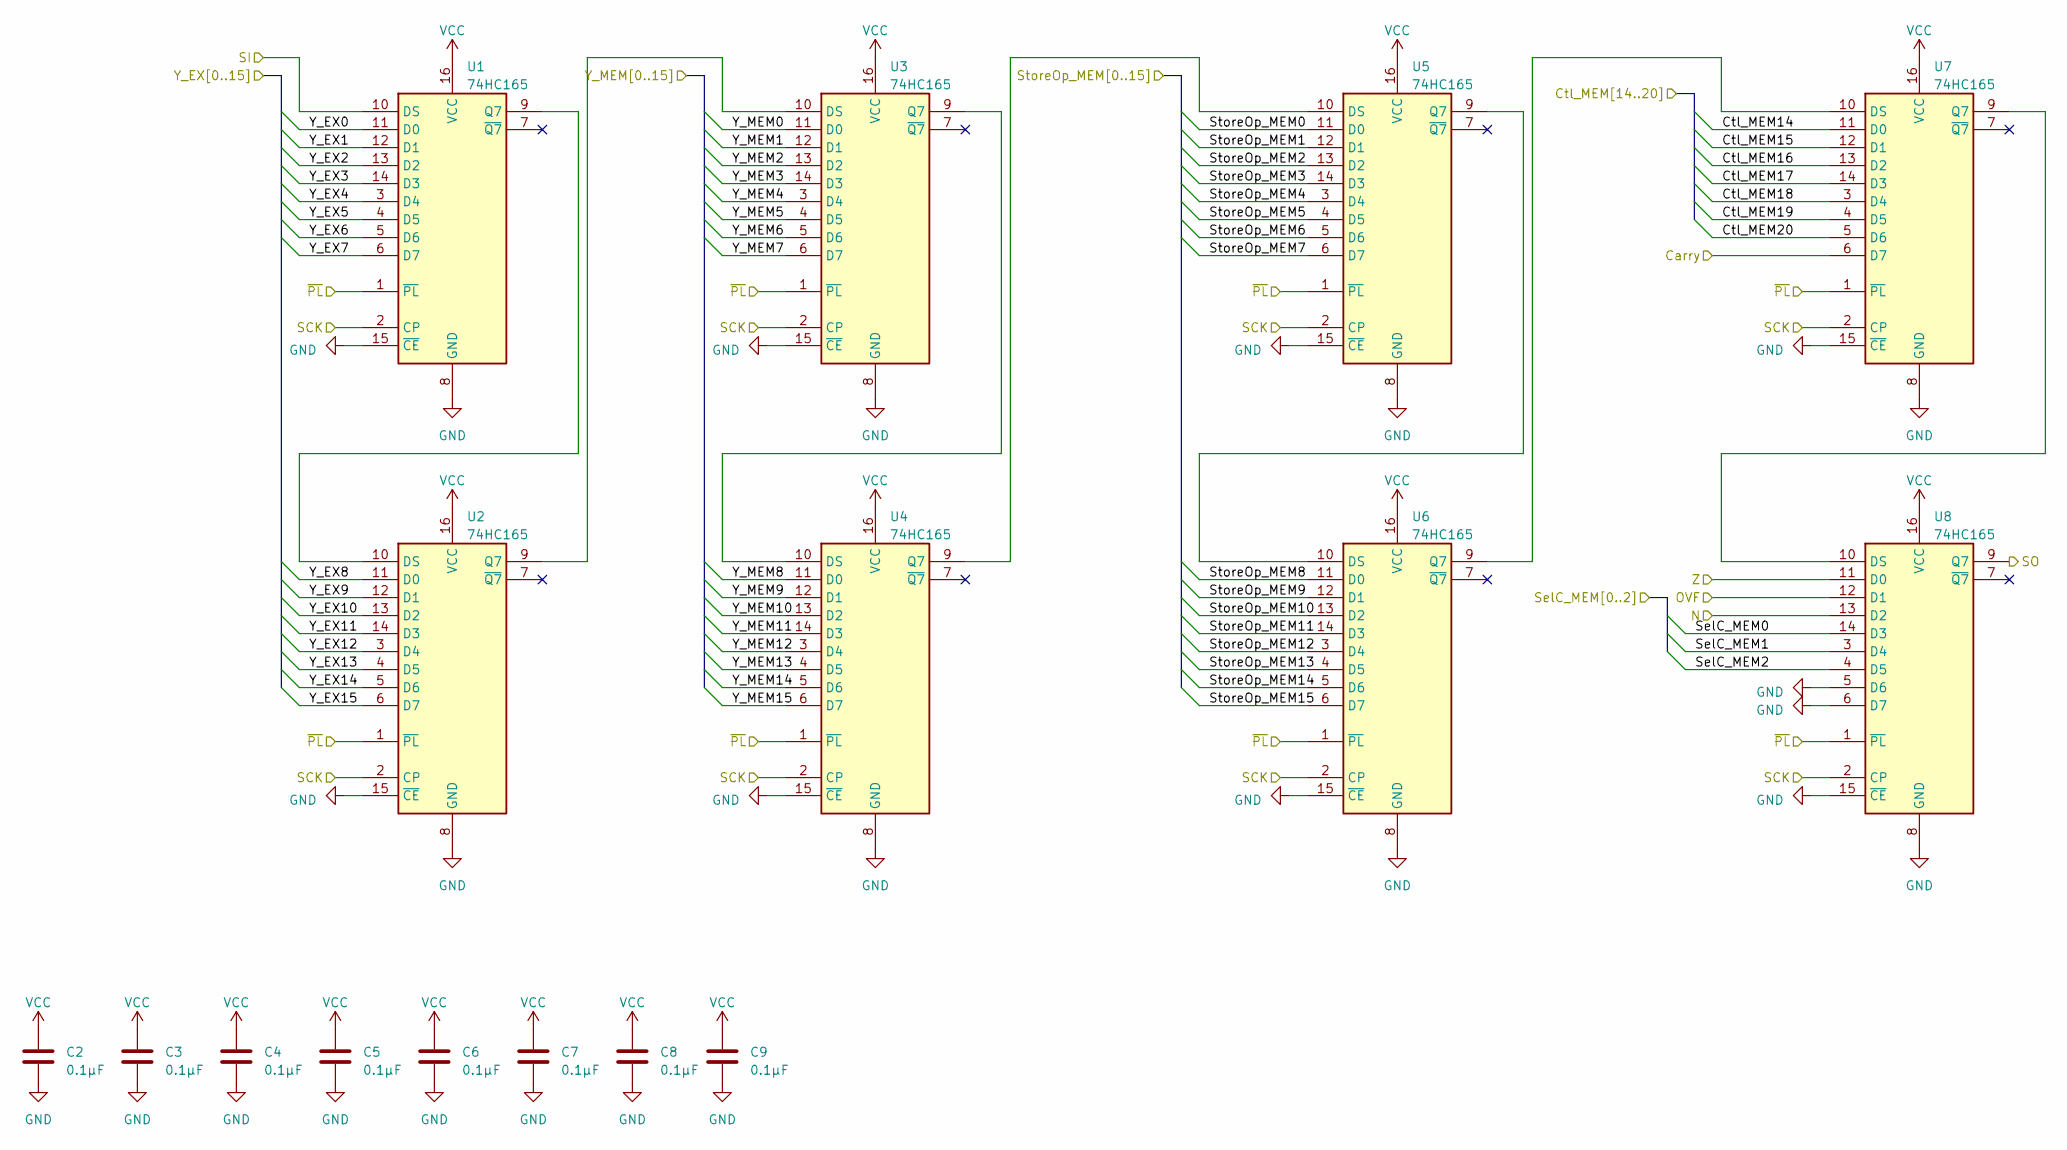
[picture p151: schematic TestFixtureInputs.kicad_sch]

Parts:
C2, C3, C4, C5, C6, C7, C8, C9: 0.1µF; C_0603_1608Metric
U1, U2, U3, U4, U5, U6, U7, U8: 74HC165; TSSOP-16_4.4x5mm_P0.65mm

Connections:
/EX Prototype Outputs/Carry: U7.6 (D7); also elsewhere on the board
/EX Prototype Outputs/Ctl_MEM14: U7.11 (D0); also elsewhere on the board
/EX Prototype Outputs/Ctl_MEM15: U7.12 (D1); also elsewhere on the board
/EX Prototype Outputs/Ctl_MEM16: U7.13 (D2); also elsewhere on the board
/EX Prototype Outputs/Ctl_MEM17: U7.14 (D3); also elsewhere on the board
/EX Prototype Outputs/Ctl_MEM18: U7.3 (D4); also elsewhere on the board
/EX Prototype Outputs/Ctl_MEM19: U7.4 (D5); also elsewhere on the board
/EX Prototype Outputs/Ctl_MEM20: U7.5 (D6); also elsewhere on the board
/EX Prototype Outputs/N: U8.13 (D2); also elsewhere on the board
/EX Prototype Outputs/OVF: U8.12 (D1); also elsewhere on the board
/EX Prototype Outputs/SelC_MEM0: U8.14 (D3); also elsewhere on the board
/EX Prototype Outputs/SelC_MEM1: U8.3 (D4); also elsewhere on the board
/EX Prototype Outputs/SelC_MEM2: U8.4 (D5); also elsewhere on the board
/EX Prototype Outputs/StoreOp_MEM0: U5.11 (D0); also elsewhere on the board
/EX Prototype Outputs/StoreOp_MEM1: U5.12 (D1); also elsewhere on the board
/EX Prototype Outputs/StoreOp_MEM2: U5.13 (D2); also elsewhere on the board
/EX Prototype Outputs/StoreOp_MEM3: U5.14 (D3); also elsewhere on the board
/EX Prototype Outputs/StoreOp_MEM4: U5.3 (D4); also elsewhere on the board
/EX Prototype Outputs/StoreOp_MEM5: U5.4 (D5); also elsewhere on the board
/EX Prototype Outputs/StoreOp_MEM6: U5.5 (D6); also elsewhere on the board
/EX Prototype Outputs/StoreOp_MEM7: U5.6 (D7); also elsewhere on the board
/EX Prototype Outputs/StoreOp_MEM8: U6.11 (D0); also elsewhere on the board
/EX Prototype Outputs/StoreOp_MEM9: U6.12 (D1); also elsewhere on the board
/EX Prototype Outputs/StoreOp_MEM10: U6.13 (D2); also elsewhere on the board
/EX Prototype Outputs/StoreOp_MEM11: U6.14 (D3); also elsewhere on the board
/EX Prototype Outputs/StoreOp_MEM12: U6.3 (D4); also elsewhere on the board
/EX Prototype Outputs/StoreOp_MEM13: U6.4 (D5); also elsewhere on the board
/EX Prototype Outputs/StoreOp_MEM14: U6.5 (D6); also elsewhere on the board
/EX Prototype Outputs/StoreOp_MEM15: U6.6 (D7); also elsewhere on the board
/EX Prototype Outputs/Y_EX0: U1.11 (D0); also elsewhere on the board
/EX Prototype Outputs/Y_EX1: U1.12 (D1); also elsewhere on the board
/EX Prototype Outputs/Y_EX2: U1.13 (D2); also elsewhere on the board
/EX Prototype Outputs/Y_EX3: U1.14 (D3); also elsewhere on the board
/EX Prototype Outputs/Y_EX4: U1.3 (D4); also elsewhere on the board
/EX Prototype Outputs/Y_EX5: U1.4 (D5); also elsewhere on the board
/EX Prototype Outputs/Y_EX6: U1.5 (D6); also elsewhere on the board
/EX Prototype Outputs/Y_EX7: U1.6 (D7); also elsewhere on the board
/EX Prototype Outputs/Y_EX8: U2.11 (D0); also elsewhere on the board
/EX Prototype Outputs/Y_EX9: U2.12 (D1); also elsewhere on the board
/EX Prototype Outputs/Y_EX10: U2.13 (D2); also elsewhere on the board
/EX Prototype Outputs/Y_EX11: U2.14 (D3); also elsewhere on the board
/EX Prototype Outputs/Y_EX12: U2.3 (D4); also elsewhere on the board
/EX Prototype Outputs/Y_EX13: U2.4 (D5); also elsewhere on the board
/EX Prototype Outputs/Y_EX14: U2.5 (D6); also elsewhere on the board
/EX Prototype Outputs/Y_EX15: U2.6 (D7); also elsewhere on the board
/EX Prototype Outputs/Y_MEM0: U3.11 (D0); also elsewhere on the board
/EX Prototype Outputs/Y_MEM1: U3.12 (D1); also elsewhere on the board
/EX Prototype Outputs/Y_MEM2: U3.13 (D2); also elsewhere on the board
/EX Prototype Outputs/Y_MEM3: U3.14 (D3); also elsewhere on the board
/EX Prototype Outputs/Y_MEM4: U3.3 (D4); also elsewhere on the board
/EX Prototype Outputs/Y_MEM5: U3.4 (D5); also elsewhere on the board
/EX Prototype Outputs/Y_MEM6: U3.5 (D6); also elsewhere on the board
/EX Prototype Outputs/Y_MEM7: U3.6 (D7); also elsewhere on the board
/EX Prototype Outputs/Y_MEM8: U4.11 (D0); also elsewhere on the board
/EX Prototype Outputs/Y_MEM9: U4.12 (D1); also elsewhere on the board
/EX Prototype Outputs/Y_MEM10: U4.13 (D2); also elsewhere on the board
/EX Prototype Outputs/Y_MEM11: U4.14 (D3); also elsewhere on the board
/EX Prototype Outputs/Y_MEM12: U4.3 (D4); also elsewhere on the board
/EX Prototype Outputs/Y_MEM13: U4.4 (D5); also elsewhere on the board
/EX Prototype Outputs/Y_MEM14: U4.5 (D6); also elsewhere on the board
/EX Prototype Outputs/Y_MEM15: U4.6 (D7); also elsewhere on the board
/EX Prototype Outputs/Z: U8.11 (D0); also elsewhere on the board
/Test Fixture Inputs/SCK: U1.2 (CP), U2.2 (CP), U3.2 (CP), U4.2 (CP), U5.2 (CP), U6.2 (CP), U7.2 (CP), U8.2 (CP); also elsewhere on the board
/Test Fixture Inputs/SO: U8.9 (Q7); also elsewhere on the board
/Test Fixture Inputs/~PL: U1.1 (~PL), U2.1 (~PL), U3.1 (~PL), U4.1 (~PL), U5.1 (~PL), U6.1 (~PL), U7.1 (~PL), U8.1 (~PL); also elsewhere on the board
GND: C2.2, C3.2, C4.2, C5.2, C6.2, C7.2, C8.2, C9.2, U1.8 (GND), U1.10 (DS), U1.15 (~CE), U2.8 (GND), U2.15 (~CE), U3.8 (GND), U3.15 (~CE), U4.8 (GND), U4.15 (~CE), U5.8 (GND), U5.15 (~CE), U6.8 (GND), U6.15 (~CE), U7.8 (GND), U7.15 (~CE), U8.5 (D6), U8.6 (D7), U8.8 (GND), U8.15 (~CE); also elsewhere on the board
unnamed: U1.9 (Q7), U2.10 (DS)
unnamed: U2.9 (Q7), U3.10 (DS)
unnamed: U3.9 (Q7), U4.10 (DS)
unnamed: U4.9 (Q7), U5.10 (DS)
unnamed: U5.9 (Q7), U6.10 (DS)
unnamed: U6.9 (Q7), U7.10 (DS)
unnamed: U7.9 (Q7), U8.10 (DS)
VCC: C2.1, C3.1, C4.1, C5.1, C6.1, C7.1, C8.1, C9.1, U1.16 (VCC), U2.16 (VCC), U3.16 (VCC), U4.16 (VCC), U5.16 (VCC), U6.16 (VCC), U7.16 (VCC), U8.16 (VCC); also elsewhere on the board
