foxostro/Turtle16/Hardware/PrototypeProcessor/EXModuleTestFixture/EXModuleTestFixture.kicad_pcb

## KiCad design Hardware/PrototypeProcessor/EXModuleTestFixture/EXModuleTestFixture.kicad_pcb (continued)

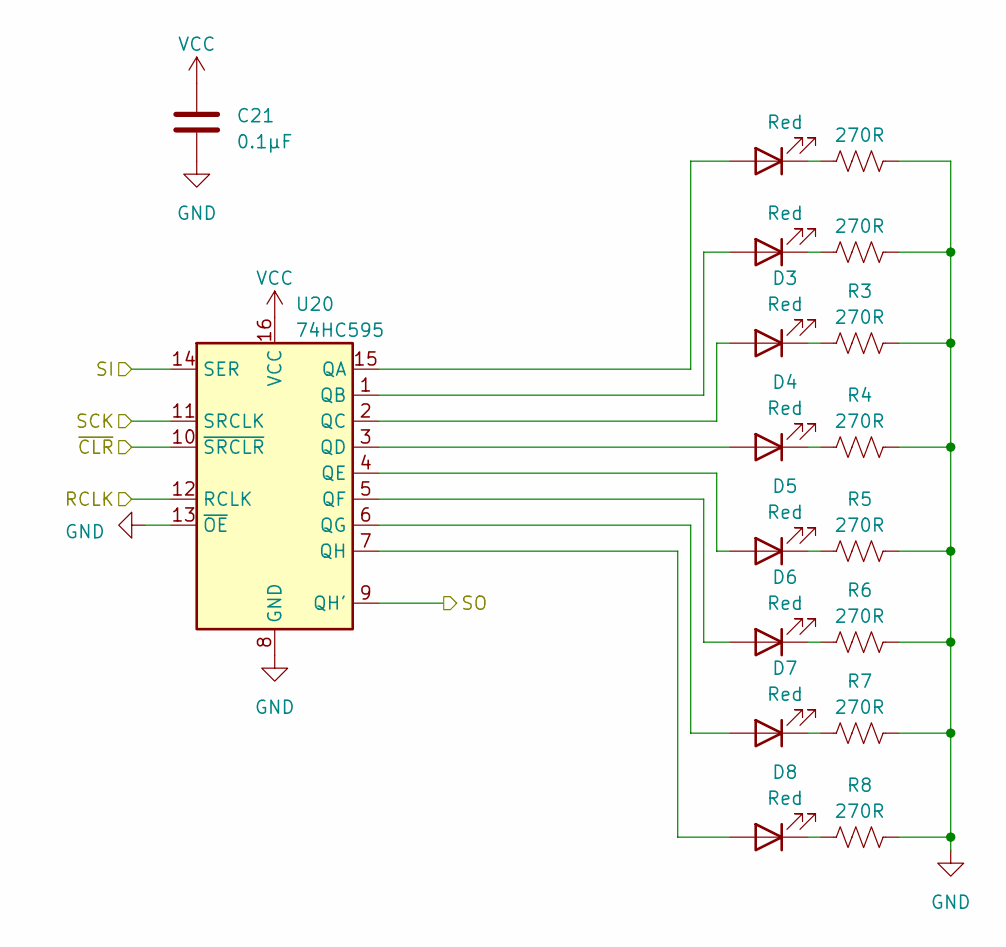
[picture p152: schematic LEDOutputs.kicad_sch]

Parts:
C21: 0.1µF; C_0603_1608Metric
D1, D2, D3, D4, D5, D6, D7, D8: Red; LED_0603_1608Metric
R1, R2, R3, R4, R5, R6, R7, R8: 270R; C_0603_1608Metric
U20: 74HC595; TSSOP-16_4.4x5mm_P0.65mm

Connections:
/LED Output/RCLK: U20.12 (RCLK); also elsewhere on the board
/LED Output/SCK: U20.11 (SRCLK); also elsewhere on the board
/LED Output/SI: U20.14 (SER); also elsewhere on the board
/LED Output/SO: U20.9 (QH')
/LED Output/~CLR: U20.10 (~SRCLR); also elsewhere on the board
GND: C21.2, R1.2, R2.2, R3.2, R4.2, R5.2, R6.2, R7.2, R8.2, U20.8 (GND), U20.13 (~OE); also elsewhere on the board
unnamed: D1.2 (A), U20.15 (QA)
unnamed: D1.1 (K), R1.1
unnamed: D2.2 (A), U20.1 (QB)
unnamed: D2.1 (K), R2.1
unnamed: D3.2 (A), U20.2 (QC)
unnamed: D3.1 (K), R3.1
unnamed: D4.2 (A), U20.3 (QD)
unnamed: D4.1 (K), R4.1
unnamed: D5.2 (A), U20.4 (QE)
unnamed: D5.1 (K), R5.1
unnamed: D6.2 (A), U20.5 (QF)
unnamed: D6.1 (K), R6.1
unnamed: D7.2 (A), U20.6 (QG)
unnamed: D7.1 (K), R7.1
unnamed: D8.2 (A), U20.7 (QH)
unnamed: D8.1 (K), R8.1
VCC: C21.1, U20.16 (VCC); also elsewhere on the board

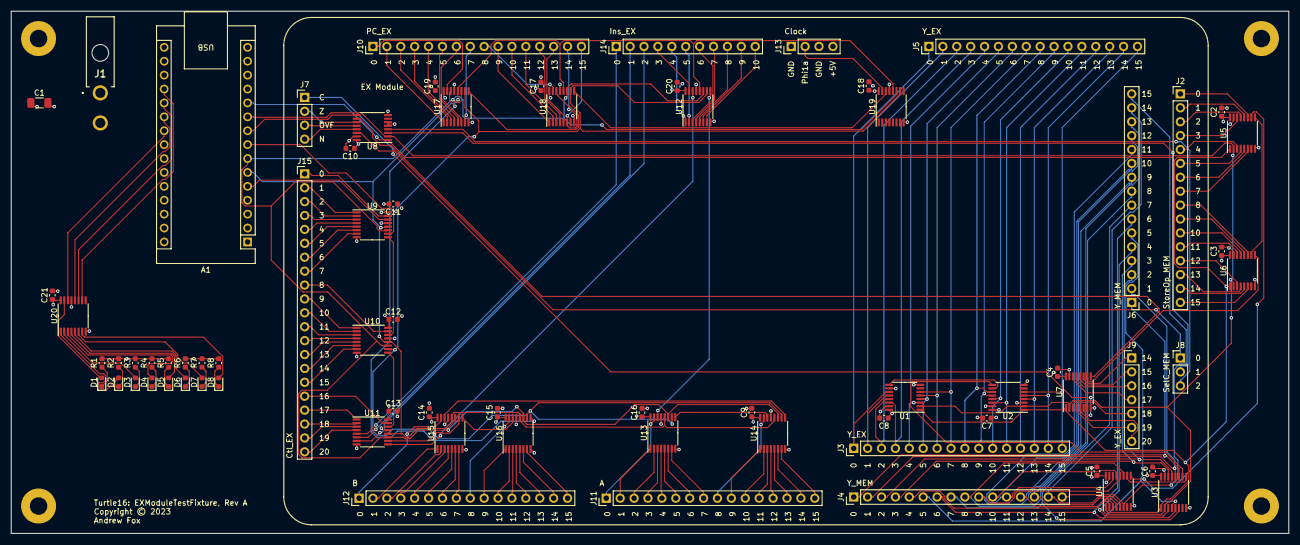
[picture p153: board EXModuleTestFixture.kicad_pcb from above]

Board: 4 copper layers, 233.4 x 95.4 mm, 77 parts (0 on the bottom side), 189 nets.
