foxostro/Turtle16/Hardware/PrototypeProcessor/ControlModule/ControlModule.kicad_pcb

## KiCad design Hardware/PrototypeProcessor/ControlModule/ControlModule.kicad_pcb (2025-06-30)

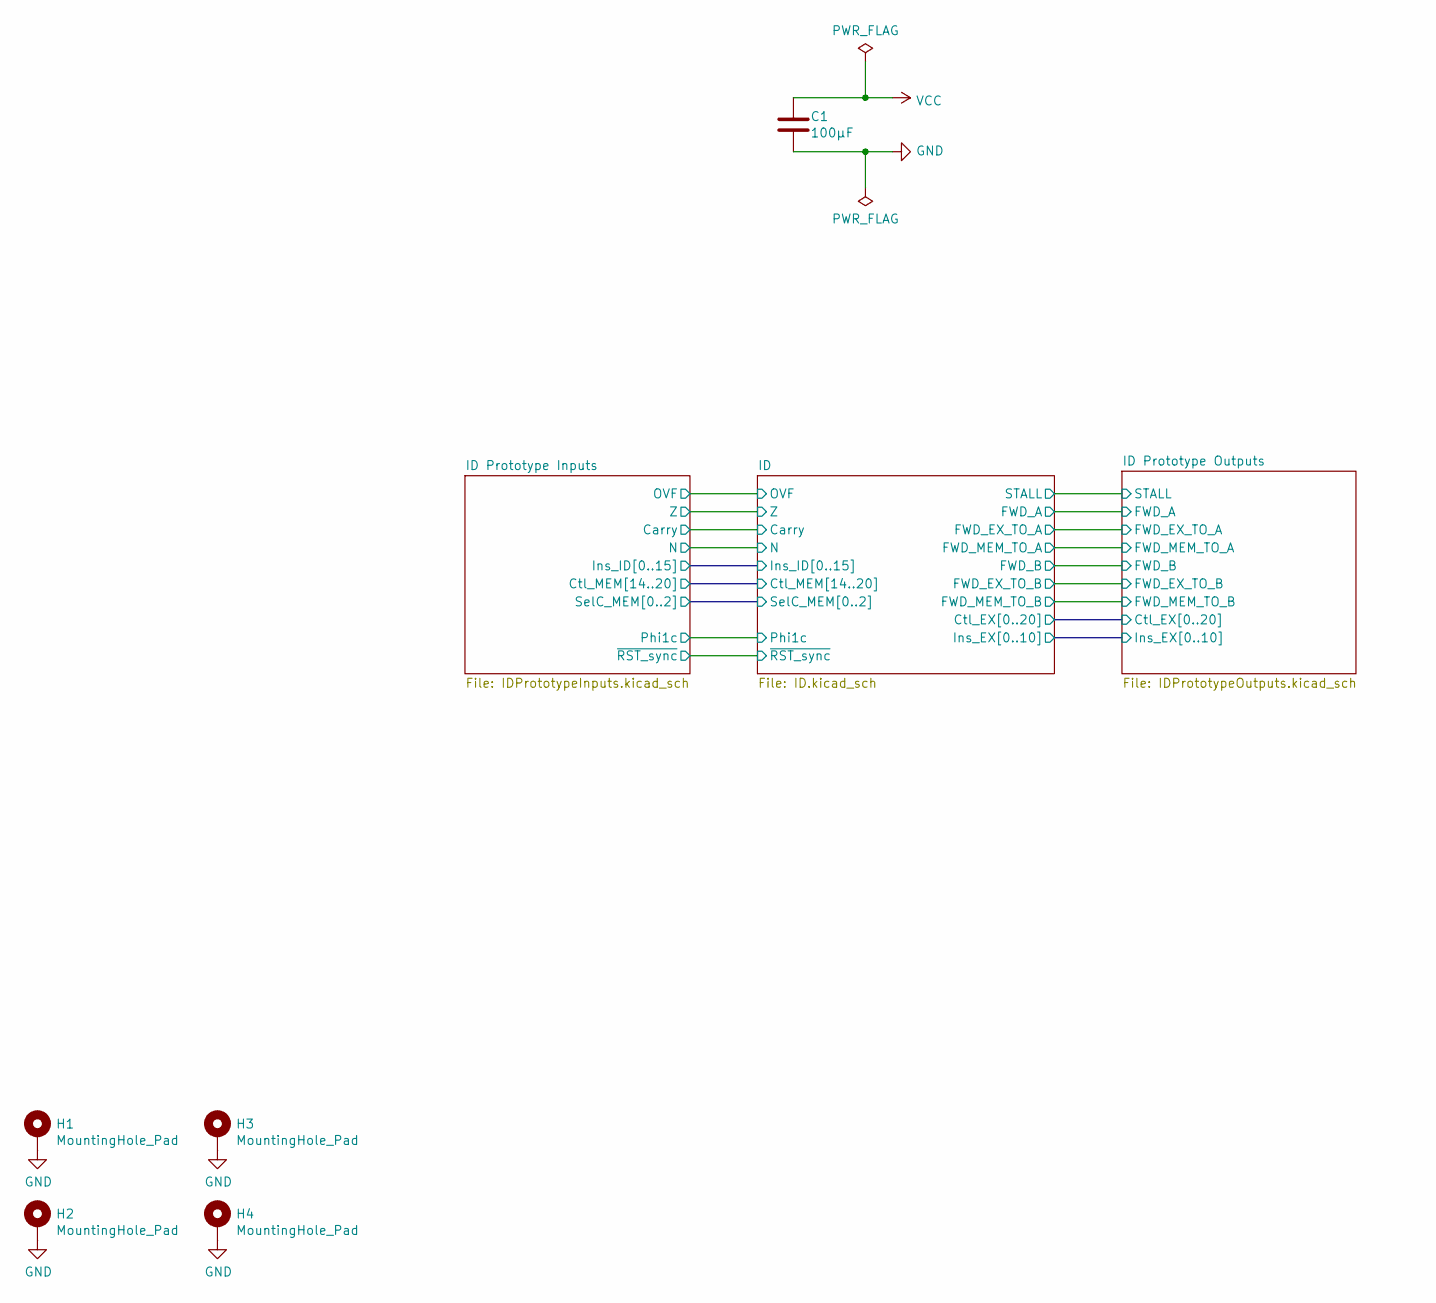
[picture p154: schematic ControlModule.kicad_sch, Turtle16: Control]

Parts:
C1: 100µF; C_1206_3216Metric_Pad1.33x1.80mm_HandSolder
H1, H2, H3, H4: MountingHole_Pad; MountingHole_3.2mm_M3_Pad

Connections:
GND: C1.2, H1.1, H2.1, H3.1, H4.1; also elsewhere on the board
VCC: C1.1; also elsewhere on the board

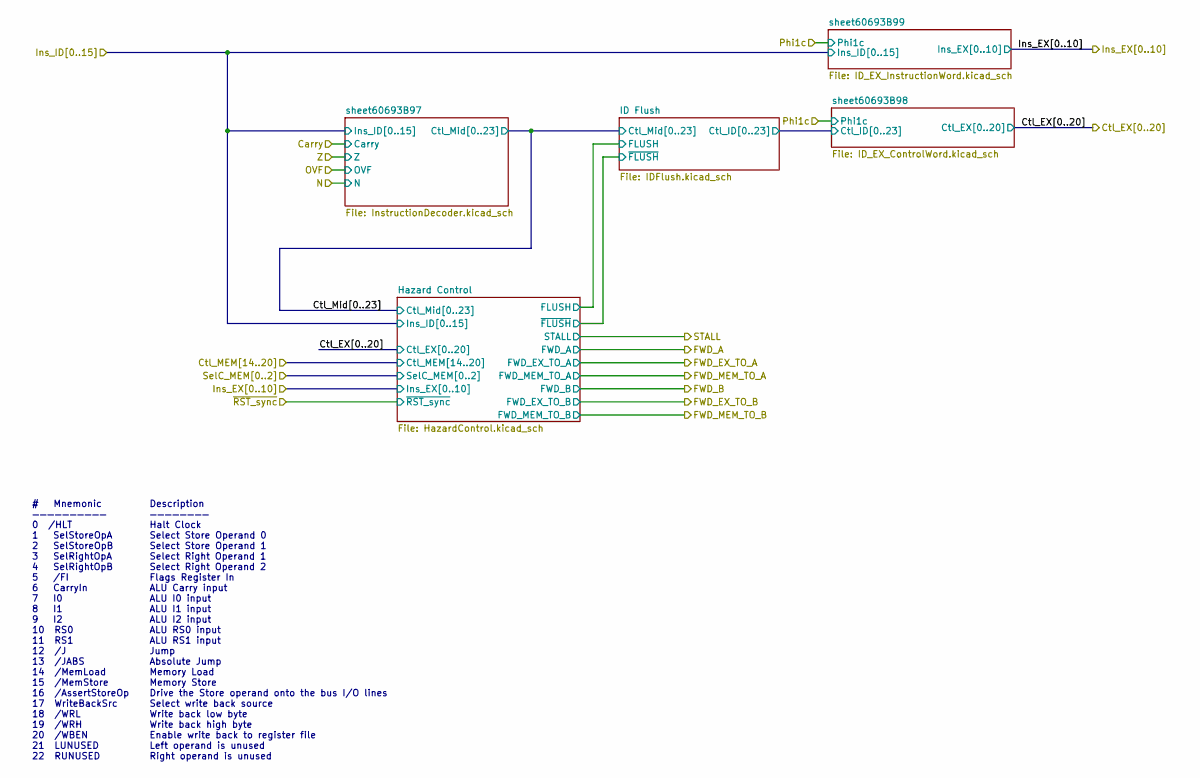
[picture p155: schematic ID.kicad_sch]

Notes on the sheet:
Description ———————— Halt Clock Select Store Operand 0 Select Store Operand 1 Select Right Operand 1 Select Right Operand 2 Flags Register In ALU Carry input ALU I0 input ALU I1 input ALU I2 input ALU RS0 input ALU RS1 input Jump Absolute Jump Memory Load Memory Store Drive the Store operand onto t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
# Mnemonic —————————— 0 /HLT 1 SelStoreOpA 2 SelStoreOpB 3 SelRightOpA 4 SelRightOpB 5 /FI 6 CarryIn 7 I0 8 I1 9 I2 10 RS0 11 RS1 12 /J 13 /JABS 14 /MemLoad 15 /MemStore 16 /AssertStoreOp 17 WriteBackSrc 18 /WRL 19 /WRH 20 /WBEN 21 LUNUSED 22 RUNUSED

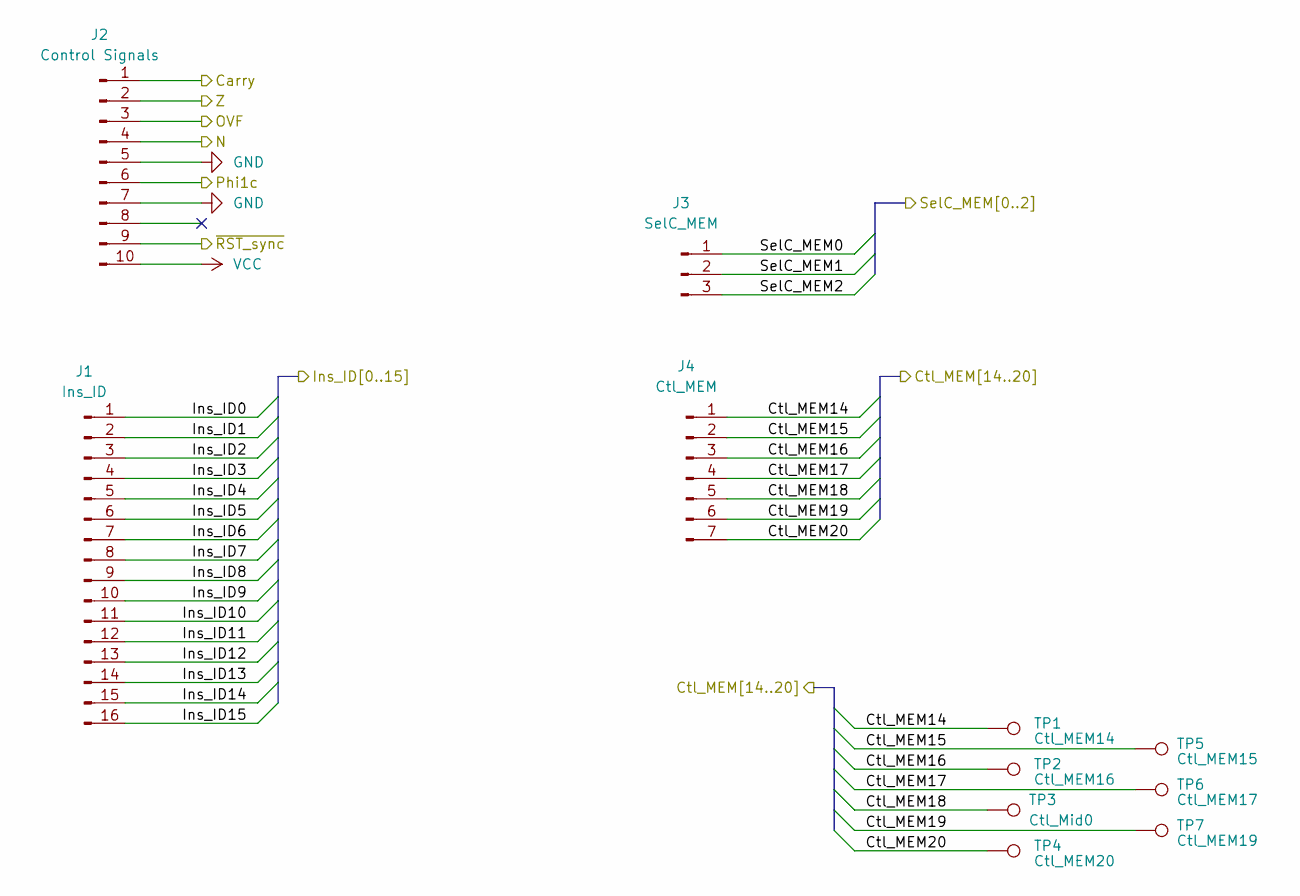
[picture p156: schematic IDPrototypeInputs.kicad_sch]

Parts:
J1: Ins_ID; PinHeader_1x16_P2.54mm_Vertical
J2: Control Signals; PinHeader_1x10_P2.54mm_Vertical
J3: SelC_MEM; PinHeader_1x03_P2.54mm_Vertical
J4: Ctl_MEM; PinHeader_1x07_P2.54mm_Vertical
TP1: Ctl_MEM14; TestPoint_Pad_D1.0mm
TP2: Ctl_MEM16; TestPoint_Pad_D1.0mm
TP3: Ctl_Mid0; TestPoint_Pad_D1.0mm
TP4: Ctl_MEM20; TestPoint_Pad_D1.0mm
TP5: Ctl_MEM15; TestPoint_Pad_D1.0mm
TP6: Ctl_MEM17; TestPoint_Pad_D1.0mm
TP7: Ctl_MEM19; TestPoint_Pad_D1.0mm

Connections:
/ID Prototype Inputs/Carry: J2.1; also elsewhere on the board
/ID Prototype Inputs/Ctl_MEM14: J4.1, TP1.1
/ID Prototype Inputs/Ctl_MEM15: J4.2, TP5.1
/ID Prototype Inputs/Ctl_MEM16: J4.3, TP2.1
/ID Prototype Inputs/Ctl_MEM17: J4.4, TP6.1; also elsewhere on the board
/ID Prototype Inputs/Ctl_MEM18: J4.5, TP3.1
/ID Prototype Inputs/Ctl_MEM19: J4.6, TP7.1
/ID Prototype Inputs/Ctl_MEM20: J4.7, TP4.1; also elsewhere on the board
/ID Prototype Inputs/Ins_ID0: J1.1; also elsewhere on the board
/ID Prototype Inputs/Ins_ID1: J1.2; also elsewhere on the board
/ID Prototype Inputs/Ins_ID2: J1.3; also elsewhere on the board
/ID Prototype Inputs/Ins_ID3: J1.4; also elsewhere on the board
/ID Prototype Inputs/Ins_ID4: J1.5; also elsewhere on the board
/ID Prototype Inputs/Ins_ID5: J1.6; also elsewhere on the board
/ID Prototype Inputs/Ins_ID6: J1.7; also elsewhere on the board
/ID Prototype Inputs/Ins_ID7: J1.8; also elsewhere on the board
/ID Prototype Inputs/Ins_ID8: J1.9; also elsewhere on the board
/ID Prototype Inputs/Ins_ID9: J1.10; also elsewhere on the board
/ID Prototype Inputs/Ins_ID10: J1.11; also elsewhere on the board
/ID Prototype Inputs/Ins_ID11: J1.12; also elsewhere on the board
/ID Prototype Inputs/Ins_ID12: J1.13; also elsewhere on the board
/ID Prototype Inputs/Ins_ID13: J1.14; also elsewhere on the board
/ID Prototype Inputs/Ins_ID14: J1.15; also elsewhere on the board
/ID Prototype Inputs/Ins_ID15: J1.16; also elsewhere on the board
/ID Prototype Inputs/N: J2.4; also elsewhere on the board
/ID Prototype Inputs/OVF: J2.3; also elsewhere on the board
/ID Prototype Inputs/Phi1c: J2.6; also elsewhere on the board
/ID Prototype Inputs/SelC_MEM0: J3.1; also elsewhere on the board
/ID Prototype Inputs/SelC_MEM1: J3.2; also elsewhere on the board
/ID Prototype Inputs/SelC_MEM2: J3.3; also elsewhere on the board
/ID Prototype Inputs/Z: J2.2; also elsewhere on the board
/ID Prototype Inputs/~RST_sync: J2.9; also elsewhere on the board
GND: J2.5, J2.7; also elsewhere on the board
VCC: J2.10; also elsewhere on the board

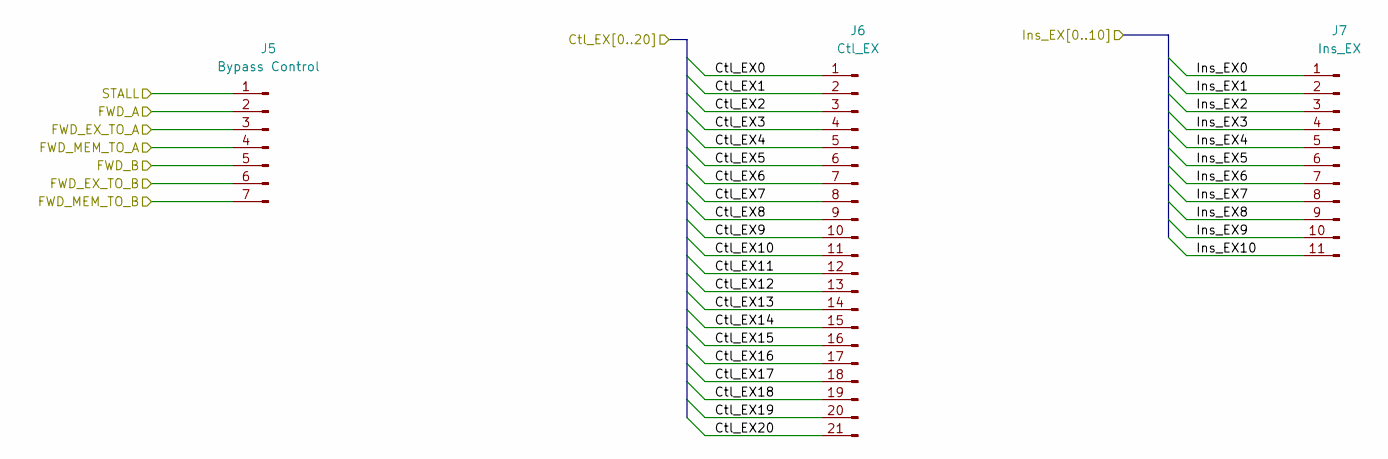
[picture p157: schematic IDPrototypeOutputs.kicad_sch]

Parts:
J5: Bypass Control; PinHeader_1x07_P2.54mm_Vertical
J6: Ctl_EX; PinHeader_1x21_P2.54mm_Vertical
J7: Ins_EX; PinHeader_1x11_P2.54mm_Vertical

Connections:
/ID Prototype Outputs/FWD_A: J5.2; also elsewhere on the board
/ID Prototype Outputs/FWD_B: J5.5; also elsewhere on the board
/ID Prototype Outputs/FWD_EX_TO_A: J5.3; also elsewhere on the board
/ID Prototype Outputs/FWD_EX_TO_B: J5.6; also elsewhere on the board
/ID Prototype Outputs/FWD_MEM_TO_A: J5.4; also elsewhere on the board
/ID Prototype Outputs/FWD_MEM_TO_B: J5.7; also elsewhere on the board
/ID Prototype Outputs/Ins_EX0: J7.1; also elsewhere on the board
/ID Prototype Outputs/Ins_EX1: J7.2; also elsewhere on the board
/ID Prototype Outputs/Ins_EX2: J7.3; also elsewhere on the board
/ID Prototype Outputs/Ins_EX3: J7.4; also elsewhere on the board
/ID Prototype Outputs/Ins_EX4: J7.5; also elsewhere on the board
/ID Prototype Outputs/Ins_EX5: J7.6; also elsewhere on the board
/ID Prototype Outputs/Ins_EX6: J7.7; also elsewhere on the board
/ID Prototype Outputs/Ins_EX7: J7.8; also elsewhere on the board
/ID Prototype Outputs/Ins_EX8: J7.9; also elsewhere on the board
/ID Prototype Outputs/Ins_EX9: J7.10; also elsewhere on the board
/ID Prototype Outputs/Ins_EX10: J7.11; also elsewhere on the board
/ID/Ctl_EX0: J6.1; also elsewhere on the board
/ID/Ctl_EX1: J6.2; also elsewhere on the board
/ID/Ctl_EX2: J6.3; also elsewhere on the board
/ID/Ctl_EX3: J6.4; also elsewhere on the board
/ID/Ctl_EX4: J6.5; also elsewhere on the board
/ID/Ctl_EX5: J6.6; also elsewhere on the board
/ID/Ctl_EX6: J6.7; also elsewhere on the board
/ID/Ctl_EX7: J6.8; also elsewhere on the board
/ID/Ctl_EX8: J6.9; also elsewhere on the board
/ID/Ctl_EX9: J6.10; also elsewhere on the board
/ID/Ctl_EX10: J6.11; also elsewhere on the board
/ID/Ctl_EX11: J6.12; also elsewhere on the board
/ID/Ctl_EX12: J6.13; also elsewhere on the board
/ID/Ctl_EX13: J6.14; also elsewhere on the board
/ID/Ctl_EX14: J6.15; also elsewhere on the board
/ID/Ctl_EX15: J6.16; also elsewhere on the board
/ID/Ctl_EX16: J6.17; also elsewhere on the board
/ID/Ctl_EX17: J6.18; also elsewhere on the board
/ID/Ctl_EX18: J6.19; also elsewhere on the board
/ID/Ctl_EX19: J6.20; also elsewhere on the board
/ID/Ctl_EX20: J6.21; also elsewhere on the board
/ID/Hazard Control/STALL: J5.1; also elsewhere on the board

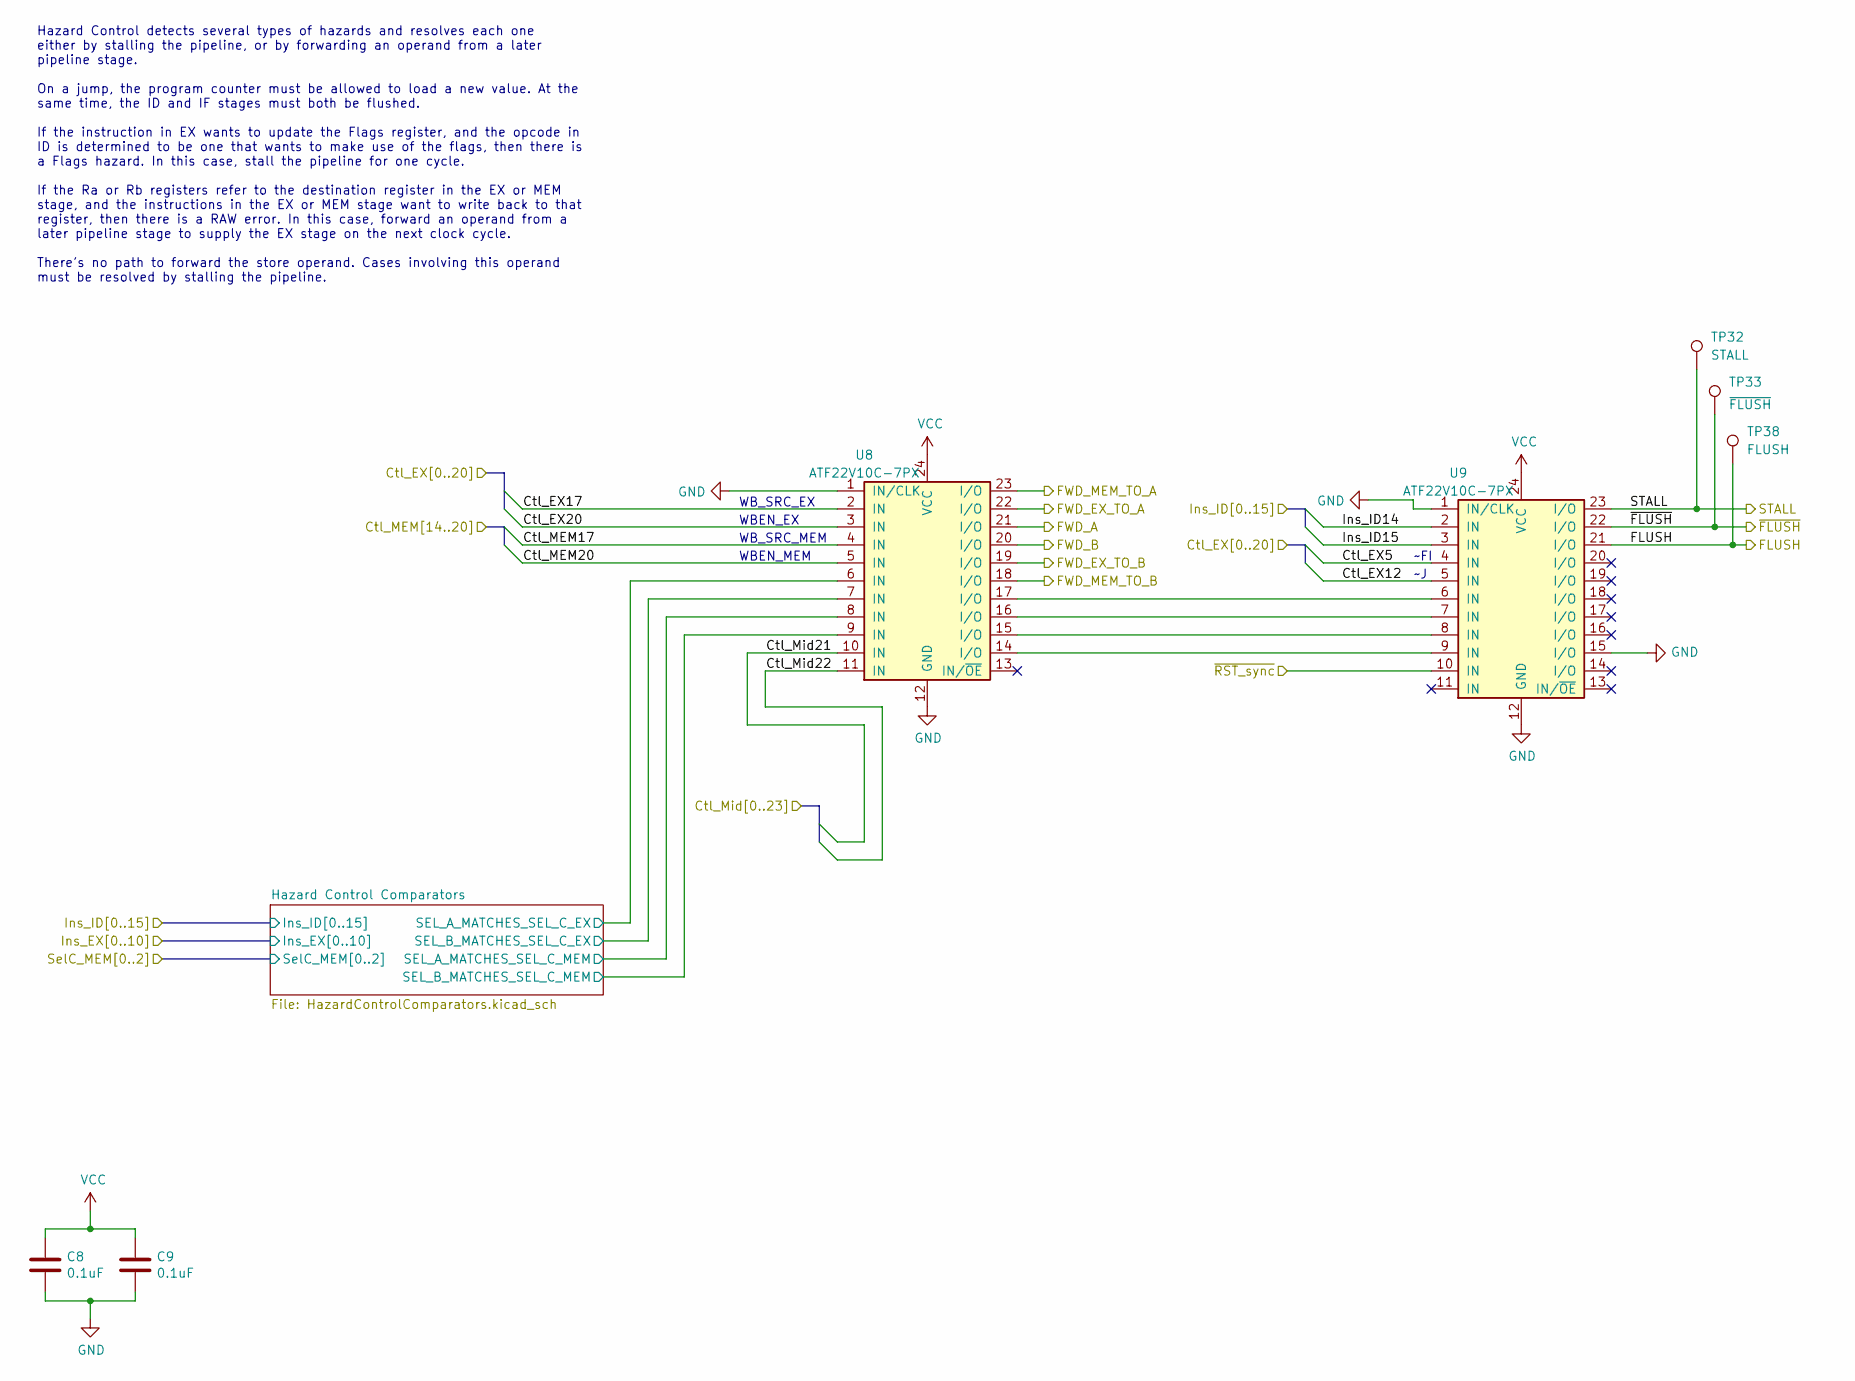
[picture p158: schematic HazardControl.kicad_sch, Hazard Control]

Parts:
C8, C9: 0.1uF; C_0603_1608Metric_Pad1.08x0.95mm_HandSolder
TP32: STALL; TestPoint_Pad_D1.0mm
TP33: ~{FLUSH}; TestPoint_Pad_D1.0mm
TP38: FLUSH; TestPoint_Pad_D1.0mm
U8, U9: ATF22V10C-7PX; DIP-24_W7.62mm_Socket

Connections:
/ID Prototype Inputs/Ctl_MEM17: U8.4 (IN); also elsewhere on the board
/ID Prototype Inputs/Ctl_MEM20: U8.5 (IN); also elsewhere on the board
/ID Prototype Inputs/Ins_ID14: U9.2 (IN); also elsewhere on the board
/ID Prototype Inputs/Ins_ID15: U9.3 (IN); also elsewhere on the board
/ID Prototype Inputs/~RST_sync: U9.10 (IN); also elsewhere on the board
/ID Prototype Outputs/FWD_A: U8.21 (I/O); also elsewhere on the board
/ID Prototype Outputs/FWD_B: U8.20 (I/O); also elsewhere on the board
/ID Prototype Outputs/FWD_EX_TO_A: U8.22 (I/O); also elsewhere on the board
/ID Prototype Outputs/FWD_EX_TO_B: U8.19 (I/O); also elsewhere on the board
/ID Prototype Outputs/FWD_MEM_TO_A: U8.23 (I/O); also elsewhere on the board
/ID Prototype Outputs/FWD_MEM_TO_B: U8.18 (I/O); also elsewhere on the board
/ID/Ctl_EX5: U9.4 (IN); also elsewhere on the board
/ID/Ctl_EX12: U9.5 (IN); also elsewhere on the board
/ID/Ctl_EX17: U8.2 (IN); also elsewhere on the board
/ID/Ctl_EX20: U8.3 (IN); also elsewhere on the board
/ID/Ctl_Mid21: U8.10 (IN); also elsewhere on the board
/ID/Ctl_Mid22: U8.11 (IN); also elsewhere on the board
/ID/Hazard Control/FLUSH: TP38.1, U9.21 (I/O); also elsewhere on the board
/ID/Hazard Control/Hazard Control Comparators/SEL_A_MATCHES_SEL_C_EX: U8.6 (IN); also elsewhere on the board
/ID/Hazard Control/Hazard Control Comparators/SEL_A_MATCHES_SEL_C_MEM: U8.8 (IN); also elsewhere on the board
/ID/Hazard Control/Hazard Control Comparators/SEL_B_MATCHES_SEL_C_EX: U8.7 (IN); also elsewhere on the board
/ID/Hazard Control/Hazard Control Comparators/SEL_B_MATCHES_SEL_C_MEM: U8.9 (IN); also elsewhere on the board
/ID/Hazard Control/STALL: TP32.1, U9.23 (I/O); also elsewhere on the board
/ID/Hazard Control/~FLUSH: TP33.1, U9.22 (I/O); also elsewhere on the board
GND: C8.2, C9.2, U8.1 (IN/CLK), U8.12 (GND), U9.1 (IN/CLK), U9.12 (GND), U9.15 (I/O); also elsewhere on the board
unnamed: U8.14 (I/O), U9.9 (IN)
unnamed: U8.15 (I/O), U9.8 (IN)
unnamed: U8.16 (I/O), U9.7 (IN)
unnamed: U8.17 (I/O), U9.6 (IN)
VCC: C8.1, C9.1, U8.24 (VCC), U9.24 (VCC); also elsewhere on the board

Notes on the sheet:
Hazard Control detects several types of hazards and resolves each one either by stalling the pipeline, or by forwarding an operand from a later pipeline stage. On a jump, the program counter must be allowed to load a new value. At the same time, the ID and IF stages must both be flushed. If the ins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
WBEN_EX
WBEN_MEM
WB_SRC_EX
~FI
WB_SRC_MEM

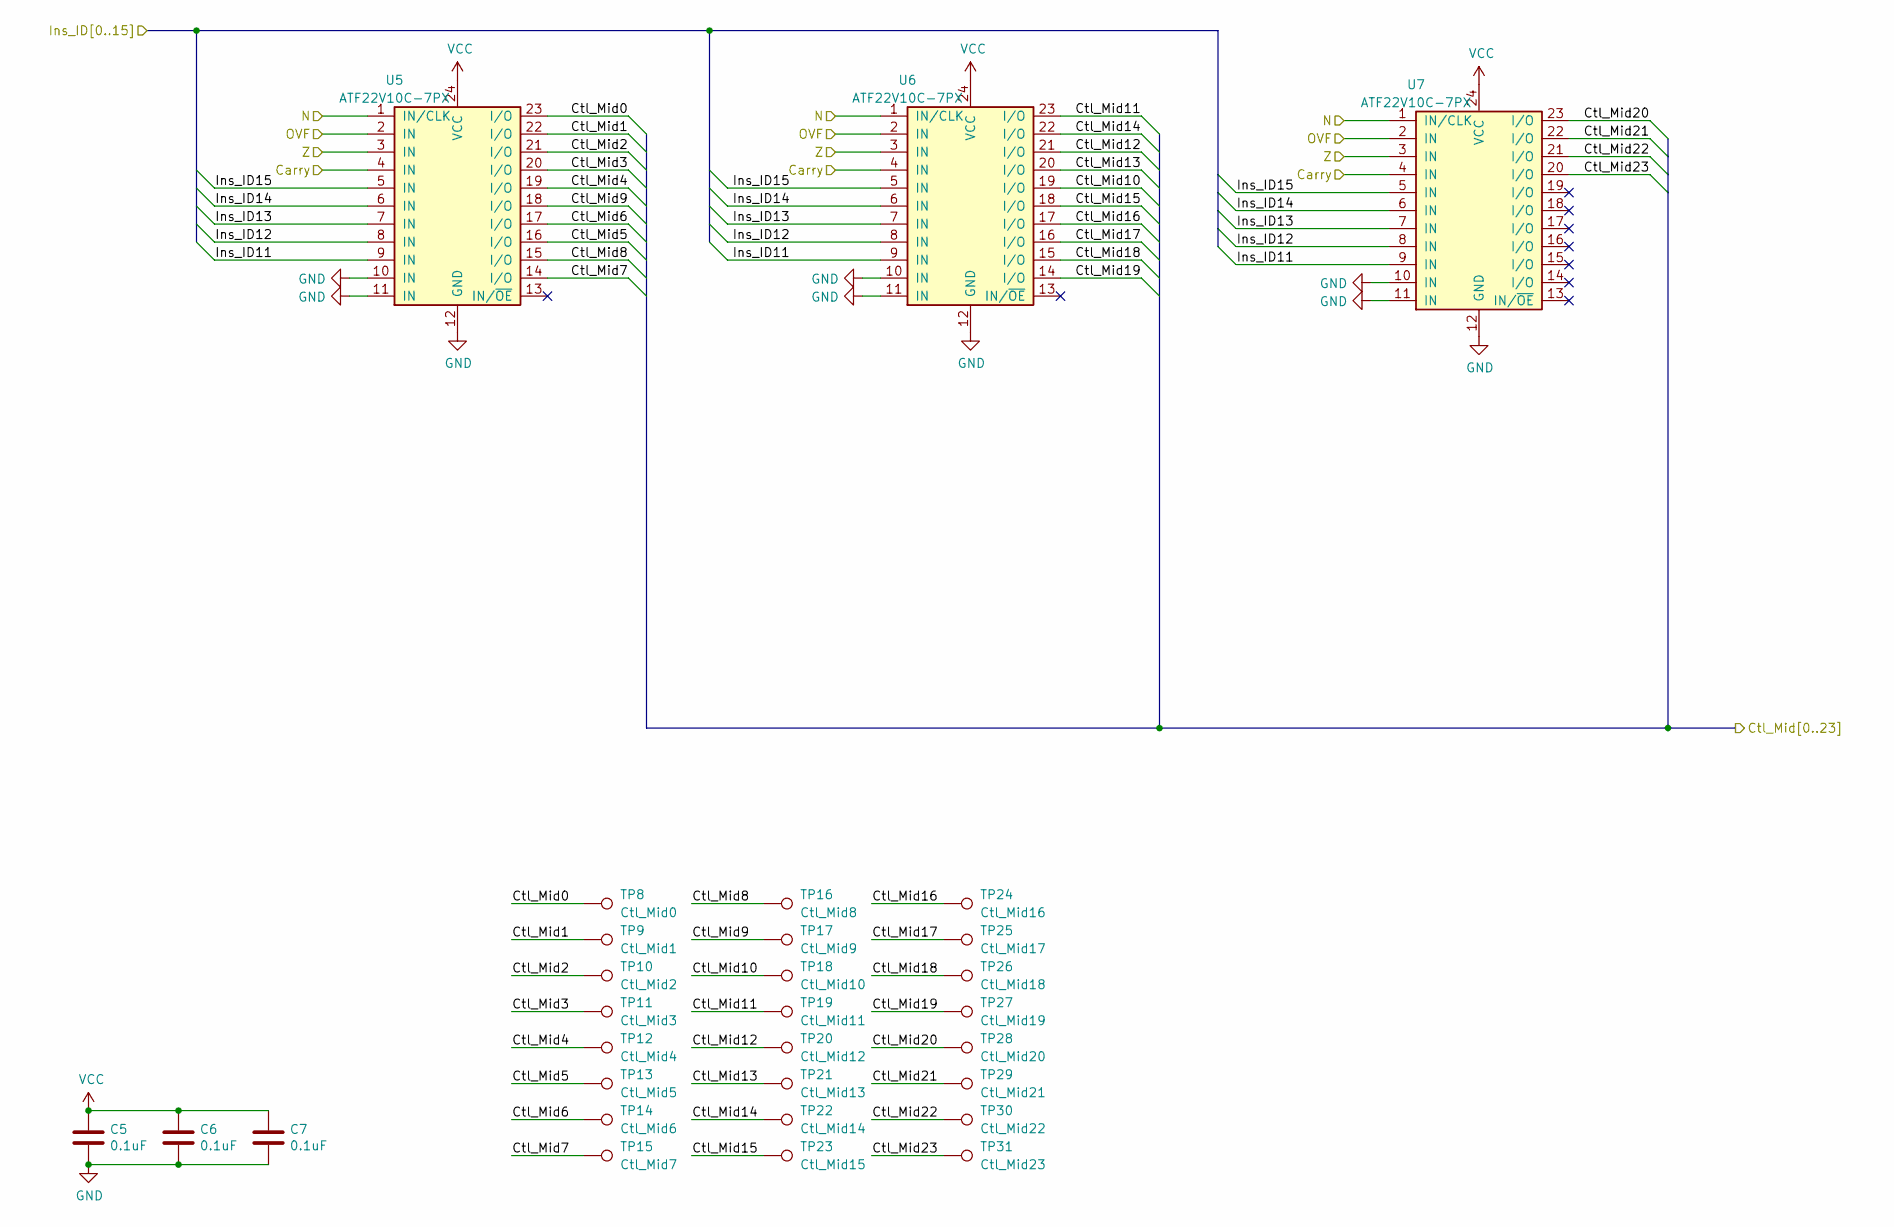
[picture p159: schematic InstructionDecoder.kicad_sch, Instruction Decoder]

Parts:
C5, C6, C7: 0.1uF; C_0603_1608Metric_Pad1.08x0.95mm_HandSolder
TP8: Ctl_Mid0; TestPoint_Pad_D1.0mm
TP9: Ctl_Mid1; TestPoint_Pad_D1.0mm
TP10: Ctl_Mid2; TestPoint_Pad_D1.0mm
TP11: Ctl_Mid3; TestPoint_Pad_D1.0mm
TP12: Ctl_Mid4; TestPoint_Pad_D1.0mm
TP13: Ctl_Mid5; TestPoint_Pad_D1.0mm
TP14: Ctl_Mid6; TestPoint_Pad_D1.0mm
TP15: Ctl_Mid7; TestPoint_Pad_D1.0mm
TP16: Ctl_Mid8; TestPoint_Pad_D1.0mm
TP17: Ctl_Mid9; TestPoint_Pad_D1.0mm
TP18: Ctl_Mid10; TestPoint_Pad_D1.0mm
TP19: Ctl_Mid11; TestPoint_Pad_D1.0mm
TP20: Ctl_Mid12; TestPoint_Pad_D1.0mm
TP21: Ctl_Mid13; TestPoint_Pad_D1.0mm
TP22: Ctl_Mid14; TestPoint_Pad_D1.0mm
TP23: Ctl_Mid15; TestPoint_Pad_D1.0mm
TP24: Ctl_Mid16; TestPoint_Pad_D1.0mm
TP25: Ctl_Mid17; TestPoint_Pad_D1.0mm
TP26: Ctl_Mid18; TestPoint_Pad_D1.0mm
TP27: Ctl_Mid19; TestPoint_Pad_D1.0mm
TP28: Ctl_Mid20; TestPoint_Pad_D1.0mm
TP29: Ctl_Mid21; TestPoint_Pad_D1.0mm
TP30: Ctl_Mid22; TestPoint_Pad_D1.0mm
TP31: Ctl_Mid23; TestPoint_Pad_D1.0mm
U5, U6, U7: ATF22V10C-7PX; DIP-24_W7.62mm_Socket

Connections:
/ID Prototype Inputs/Carry: U5.4 (IN), U6.4 (IN), U7.4 (IN); also elsewhere on the board
/ID Prototype Inputs/Ins_ID11: U5.9 (IN), U6.9 (IN), U7.9 (IN); also elsewhere on the board
/ID Prototype Inputs/Ins_ID12: U5.8 (IN), U6.8 (IN), U7.8 (IN); also elsewhere on the board
/ID Prototype Inputs/Ins_ID13: U5.7 (IN), U6.7 (IN), U7.7 (IN); also elsewhere on the board
/ID Prototype Inputs/Ins_ID14: U5.6 (IN), U6.6 (IN), U7.6 (IN); also elsewhere on the board
/ID Prototype Inputs/Ins_ID15: U5.5 (IN), U6.5 (IN), U7.5 (IN); also elsewhere on the board
/ID Prototype Inputs/N: U5.1 (IN/CLK), U6.1 (IN/CLK), U7.1 (IN/CLK); also elsewhere on the board
/ID Prototype Inputs/OVF: U5.2 (IN), U6.2 (IN), U7.2 (IN); also elsewhere on the board
/ID Prototype Inputs/Z: U5.3 (IN), U6.3 (IN), U7.3 (IN); also elsewhere on the board
/ID/Ctl_Mid0: TP8.1, U5.23 (I/O); also elsewhere on the board
/ID/Ctl_Mid1: TP9.1, U5.22 (I/O); also elsewhere on the board
/ID/Ctl_Mid2: TP10.1, U5.21 (I/O); also elsewhere on the board
/ID/Ctl_Mid3: TP11.1, U5.20 (I/O); also elsewhere on the board
/ID/Ctl_Mid4: TP12.1, U5.19 (I/O); also elsewhere on the board
/ID/Ctl_Mid5: TP13.1, U5.16 (I/O); also elsewhere on the board
/ID/Ctl_Mid6: TP14.1, U5.17 (I/O); also elsewhere on the board
/ID/Ctl_Mid7: TP15.1, U5.14 (I/O); also elsewhere on the board
/ID/Ctl_Mid8: TP16.1, U5.15 (I/O); also elsewhere on the board
/ID/Ctl_Mid9: TP17.1, U5.18 (I/O); also elsewhere on the board
/ID/Ctl_Mid10: TP18.1, U6.19 (I/O); also elsewhere on the board
/ID/Ctl_Mid11: TP19.1, U6.23 (I/O); also elsewhere on the board
/ID/Ctl_Mid12: TP20.1, U6.21 (I/O); also elsewhere on the board
/ID/Ctl_Mid13: TP21.1, U6.20 (I/O); also elsewhere on the board
/ID/Ctl_Mid14: TP22.1, U6.22 (I/O); also elsewhere on the board
/ID/Ctl_Mid15: TP23.1, U6.18 (I/O); also elsewhere on the board
/ID/Ctl_Mid16: TP24.1, U6.17 (I/O); also elsewhere on the board
/ID/Ctl_Mid17: TP25.1, U6.16 (I/O); also elsewhere on the board
/ID/Ctl_Mid18: TP26.1, U6.15 (I/O); also elsewhere on the board
/ID/Ctl_Mid19: TP27.1, U6.14 (I/O); also elsewhere on the board
/ID/Ctl_Mid20: TP28.1, U7.23 (I/O); also elsewhere on the board
/ID/Ctl_Mid21: TP29.1, U7.22 (I/O); also elsewhere on the board
/ID/Ctl_Mid22: TP30.1, U7.21 (I/O); also elsewhere on the board
/ID/Ctl_Mid23: TP31.1, U7.20 (I/O); also elsewhere on the board
GND: C5.2, C6.2, C7.2, U5.10 (IN), U5.11 (IN), U5.12 (GND), U6.10 (IN), U6.11 (IN), U6.12 (GND), U7.10 (IN), U7.11 (IN), U7.12 (GND); also elsewhere on the board
VCC: C5.1, C6.1, C7.1, U5.24 (VCC), U6.24 (VCC), U7.24 (VCC); also elsewhere on the board

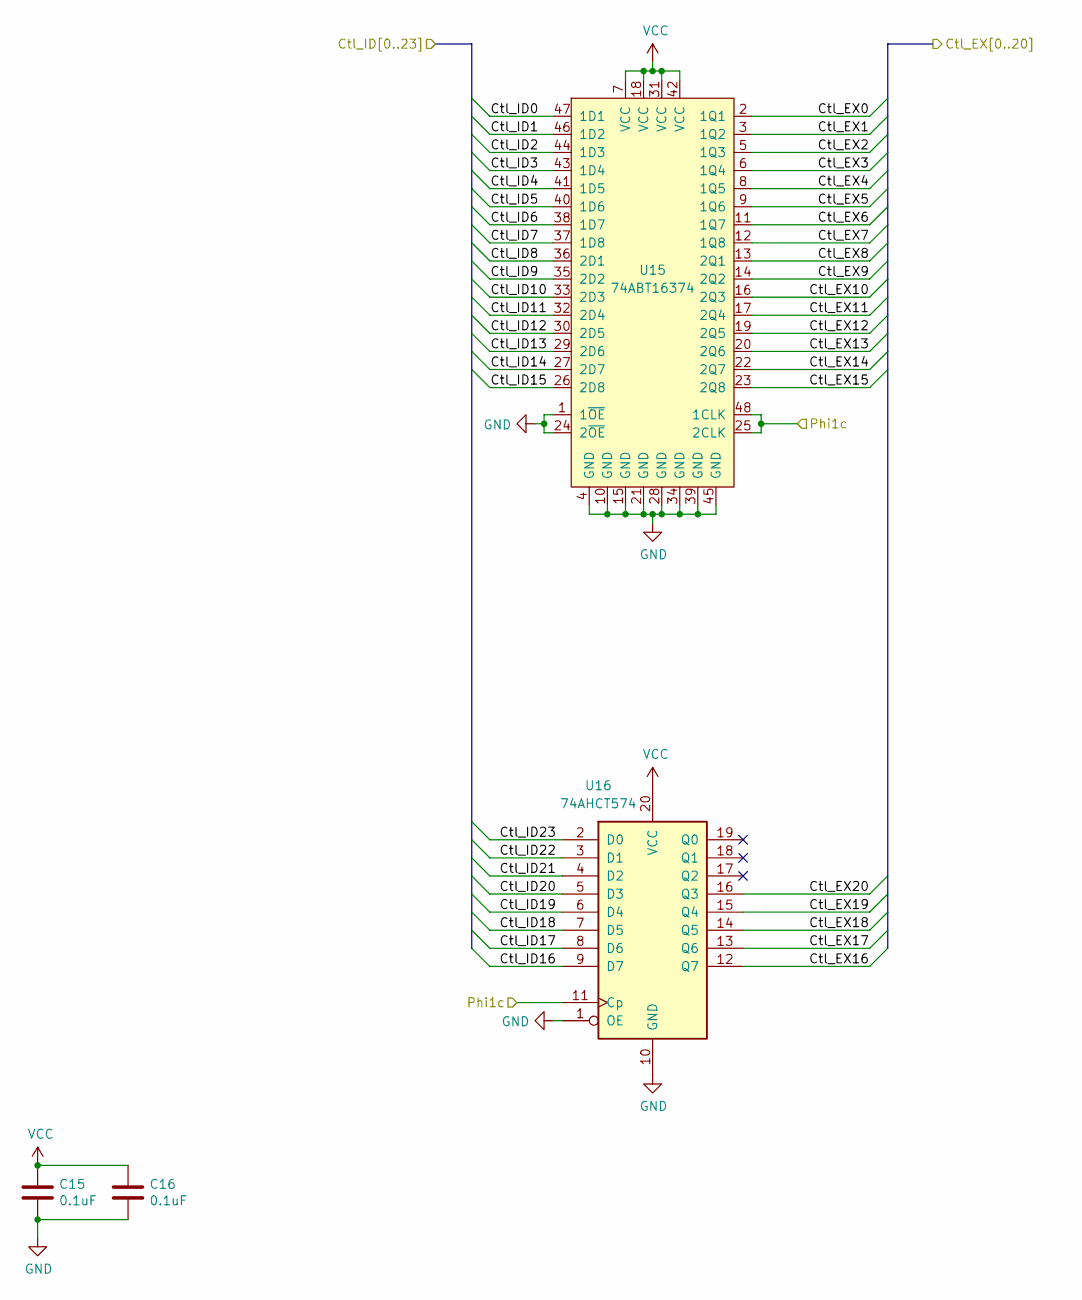
[picture p160: schematic ID_EX_ControlWord.kicad_sch, ID/EX Control Register]

Parts:
C15, C16: 0.1uF; C_0603_1608Metric_Pad1.08x0.95mm_HandSolder
U15: 74ABT16374; TSSOP-48_6.1x12.5mm_P0.5mm
U16: 74AHCT574; TSSOP-20_4.4x6.5mm_P0.65mm

Connections:
/ID Prototype Inputs/Phi1c: U15.25 (2CLK), U15.48 (1CLK), U16.11 (Cp); also elsewhere on the board
/ID/Ctl_EX0: U15.2 (1Q1); also elsewhere on the board
/ID/Ctl_EX1: U15.3 (1Q2); also elsewhere on the board
/ID/Ctl_EX2: U15.5 (1Q3); also elsewhere on the board
/ID/Ctl_EX3: U15.6 (1Q4); also elsewhere on the board
/ID/Ctl_EX4: U15.8 (1Q5); also elsewhere on the board
/ID/Ctl_EX5: U15.9 (1Q6); also elsewhere on the board
/ID/Ctl_EX6: U15.11 (1Q7); also elsewhere on the board
/ID/Ctl_EX7: U15.12 (1Q8); also elsewhere on the board
/ID/Ctl_EX8: U15.13 (2Q1); also elsewhere on the board
/ID/Ctl_EX9: U15.14 (2Q2); also elsewhere on the board
/ID/Ctl_EX10: U15.16 (2Q3); also elsewhere on the board
/ID/Ctl_EX11: U15.17 (2Q4); also elsewhere on the board
/ID/Ctl_EX12: U15.19 (2Q5); also elsewhere on the board
/ID/Ctl_EX13: U15.20 (2Q6); also elsewhere on the board
/ID/Ctl_EX14: U15.22 (2Q7); also elsewhere on the board
/ID/Ctl_EX15: U15.23 (2Q8); also elsewhere on the board
/ID/Ctl_EX16: U16.12 (Q7); also elsewhere on the board
/ID/Ctl_EX17: U16.13 (Q6); also elsewhere on the board
/ID/Ctl_EX18: U16.14 (Q5); also elsewhere on the board
/ID/Ctl_EX19: U16.15 (Q4); also elsewhere on the board
/ID/Ctl_EX20: U16.16 (Q3); also elsewhere on the board
/ID/ID Flush/Ctl_ID0: U15.47 (1D1); also elsewhere on the board
/ID/ID Flush/Ctl_ID1: U15.46 (1D2); also elsewhere on the board
/ID/ID Flush/Ctl_ID2: U15.44 (1D3); also elsewhere on the board
/ID/ID Flush/Ctl_ID3: U15.43 (1D4); also elsewhere on the board
/ID/ID Flush/Ctl_ID4: U15.41 (1D5); also elsewhere on the board
/ID/ID Flush/Ctl_ID5: U15.40 (1D6); also elsewhere on the board
/ID/ID Flush/Ctl_ID6: U15.38 (1D7); also elsewhere on the board
/ID/ID Flush/Ctl_ID7: U15.37 (1D8); also elsewhere on the board
/ID/ID Flush/Ctl_ID8: U15.36 (2D1); also elsewhere on the board
/ID/ID Flush/Ctl_ID9: U15.35 (2D2); also elsewhere on the board
/ID/ID Flush/Ctl_ID10: U15.33 (2D3); also elsewhere on the board
/ID/ID Flush/Ctl_ID11: U15.32 (2D4); also elsewhere on the board
/ID/ID Flush/Ctl_ID12: U15.30 (2D5); also elsewhere on the board
/ID/ID Flush/Ctl_ID13: U15.29 (2D6); also elsewhere on the board
/ID/ID Flush/Ctl_ID14: U15.27 (2D7); also elsewhere on the board
/ID/ID Flush/Ctl_ID15: U15.26 (2D8); also elsewhere on the board
/ID/ID Flush/Ctl_ID16: U16.9 (D7); also elsewhere on the board
/ID/ID Flush/Ctl_ID17: U16.8 (D6); also elsewhere on the board
/ID/ID Flush/Ctl_ID18: U16.7 (D5); also elsewhere on the board
/ID/ID Flush/Ctl_ID19: U16.6 (D4); also elsewhere on the board
/ID/ID Flush/Ctl_ID20: U16.5 (D3); also elsewhere on the board
/ID/ID Flush/Ctl_ID21: U16.4 (D2); also elsewhere on the board
/ID/ID Flush/Ctl_ID22: U16.3 (D1); also elsewhere on the board
/ID/ID Flush/Ctl_ID23: U16.2 (D0); also elsewhere on the board
GND: C15.2, C16.2, U15.1 (1~OE), U15.4 (GND), U15.10 (GND), U15.15 (GND), U15.21 (GND), U15.24 (2~OE), U15.28 (GND), U15.34 (GND), U15.39 (GND), U15.45 (GND), U16.1 (OE), U16.10 (GND); also elsewhere on the board
VCC: C15.1, C16.1, U15.7 (VCC), U15.18 (VCC), U15.31 (VCC), U15.42 (VCC), U16.20 (VCC); also elsewhere on the board
