foxostro/Turtle16/Hardware/PrototypeProcessor/ControlModule/ControlModule.kicad_pcb

## KiCad design Hardware/PrototypeProcessor/ControlModule/ControlModule.kicad_pcb (continued)


Parts:
C14: 0.1uF; C_0603_1608Metric_Pad1.08x0.95mm_HandSolder
U14: 74ABT16374; TSSOP-48_6.1x12.5mm_P0.5mm

Connections:
/ID Prototype Inputs/Ins_ID0: U14.47 (1D1); also elsewhere on the board
/ID Prototype Inputs/Ins_ID1: U14.46 (1D2); also elsewhere on the board
/ID Prototype Inputs/Ins_ID2: U14.44 (1D3); also elsewhere on the board
/ID Prototype Inputs/Ins_ID3: U14.43 (1D4); also elsewhere on the board
/ID Prototype Inputs/Ins_ID4: U14.41 (1D5); also elsewhere on the board
/ID Prototype Inputs/Ins_ID5: U14.40 (1D6); also elsewhere on the board
/ID Prototype Inputs/Ins_ID6: U14.38 (1D7); also elsewhere on the board
/ID Prototype Inputs/Ins_ID7: U14.37 (1D8); also elsewhere on the board
/ID Prototype Inputs/Ins_ID8: U14.36 (2D1); also elsewhere on the board
/ID Prototype Inputs/Ins_ID9: U14.35 (2D2); also elsewhere on the board
/ID Prototype Inputs/Ins_ID10: U14.33 (2D3); also elsewhere on the board
/ID Prototype Inputs/Phi1c: U14.25 (2CLK), U14.48 (1CLK); also elsewhere on the board
/ID Prototype Outputs/Ins_EX0: U14.2 (1Q1); also elsewhere on the board
/ID Prototype Outputs/Ins_EX1: U14.3 (1Q2); also elsewhere on the board
/ID Prototype Outputs/Ins_EX2: U14.5 (1Q3); also elsewhere on the board
/ID Prototype Outputs/Ins_EX3: U14.6 (1Q4); also elsewhere on the board
/ID Prototype Outputs/Ins_EX4: U14.8 (1Q5); also elsewhere on the board
/ID Prototype Outputs/Ins_EX5: U14.9 (1Q6); also elsewhere on the board
/ID Prototype Outputs/Ins_EX6: U14.11 (1Q7); also elsewhere on the board
/ID Prototype Outputs/Ins_EX7: U14.12 (1Q8); also elsewhere on the board
/ID Prototype Outputs/Ins_EX8: U14.13 (2Q1); also elsewhere on the board
/ID Prototype Outputs/Ins_EX9: U14.14 (2Q2); also elsewhere on the board
/ID Prototype Outputs/Ins_EX10: U14.16 (2Q3); also elsewhere on the board
GND: C14.2, U14.1 (1~OE), U14.4 (GND), U14.10 (GND), U14.15 (GND), U14.21 (GND), U14.24 (2~OE), U14.28 (GND), U14.34 (GND), U14.39 (GND), U14.45 (GND); also elsewhere on the board
VCC: C14.1, U14.7 (VCC), U14.18 (VCC), U14.26 (2D8), U14.27 (2D7), U14.29 (2D6), U14.30 (2D5), U14.31 (VCC), U14.32 (2D4), U14.42 (VCC); also elsewhere on the board

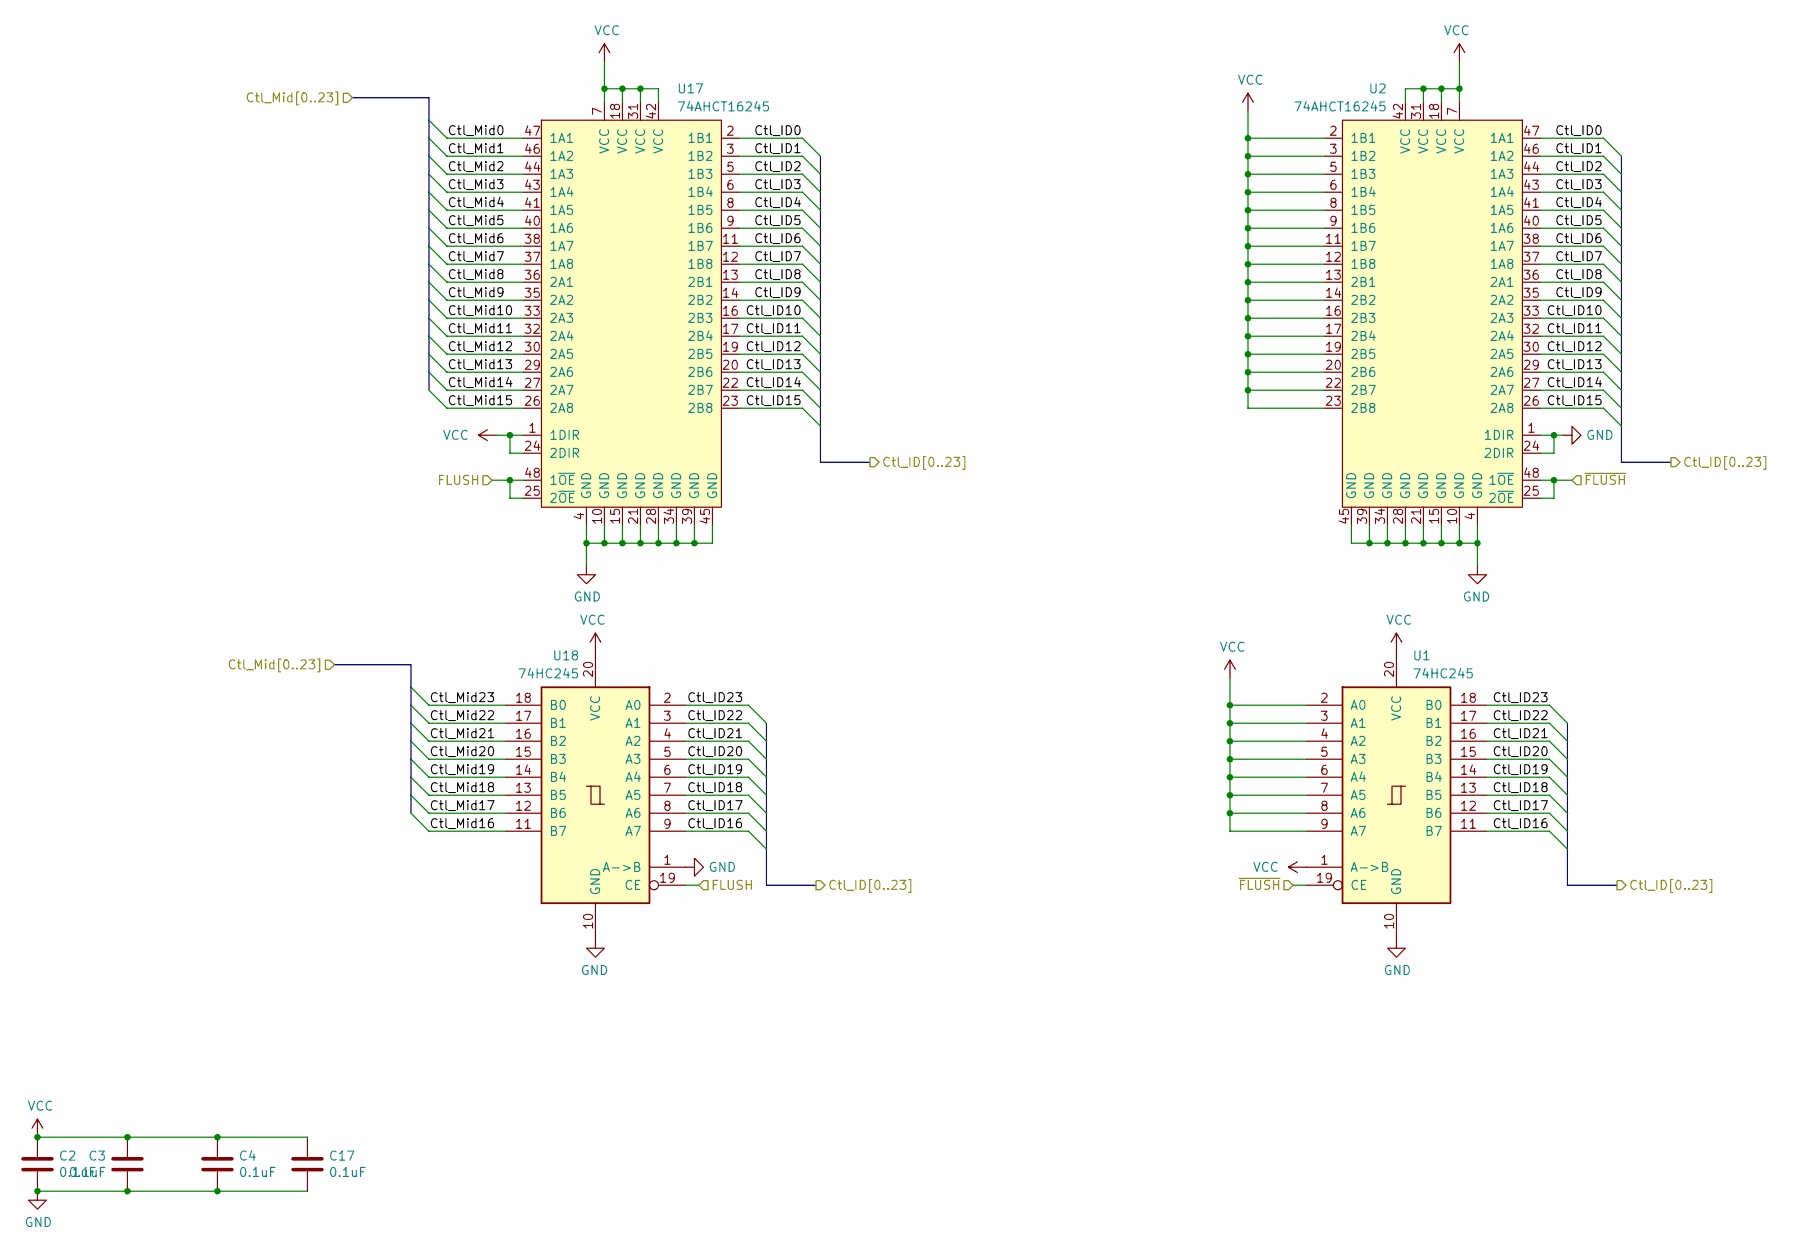
[picture p161: schematic IDFlush.kicad_sch]

Parts:
C2, C3, C4, C17: 0.1uF; C_0603_1608Metric_Pad1.08x0.95mm_HandSolder
U1, U18: 74HC245; TSSOP-20_4.4x6.5mm_P0.65mm
U2, U17: 74AHCT16245; TSSOP-48_6.1x12.5mm_P0.5mm

Connections:
/ID/Ctl_Mid0: U17.47 (1A1); also elsewhere on the board
/ID/Ctl_Mid1: U17.46 (1A2); also elsewhere on the board
/ID/Ctl_Mid2: U17.44 (1A3); also elsewhere on the board
/ID/Ctl_Mid3: U17.43 (1A4); also elsewhere on the board
/ID/Ctl_Mid4: U17.41 (1A5); also elsewhere on the board
/ID/Ctl_Mid5: U17.40 (1A6); also elsewhere on the board
/ID/Ctl_Mid6: U17.38 (1A7); also elsewhere on the board
/ID/Ctl_Mid7: U17.37 (1A8); also elsewhere on the board
/ID/Ctl_Mid8: U17.36 (2A1); also elsewhere on the board
/ID/Ctl_Mid9: U17.35 (2A2); also elsewhere on the board
/ID/Ctl_Mid10: U17.33 (2A3); also elsewhere on the board
/ID/Ctl_Mid11: U17.32 (2A4); also elsewhere on the board
/ID/Ctl_Mid12: U17.30 (2A5); also elsewhere on the board
/ID/Ctl_Mid13: U17.29 (2A6); also elsewhere on the board
/ID/Ctl_Mid14: U17.27 (2A7); also elsewhere on the board
/ID/Ctl_Mid15: U17.26 (2A8); also elsewhere on the board
/ID/Ctl_Mid16: U18.11 (B7); also elsewhere on the board
/ID/Ctl_Mid17: U18.12 (B6); also elsewhere on the board
/ID/Ctl_Mid18: U18.13 (B5); also elsewhere on the board
/ID/Ctl_Mid19: U18.14 (B4); also elsewhere on the board
/ID/Ctl_Mid20: U18.15 (B3); also elsewhere on the board
/ID/Ctl_Mid21: U18.16 (B2); also elsewhere on the board
/ID/Ctl_Mid22: U18.17 (B1); also elsewhere on the board
/ID/Ctl_Mid23: U18.18 (B0); also elsewhere on the board
/ID/Hazard Control/FLUSH: U17.25 (2~OE), U17.48 (1~OE), U18.19 (CE); also elsewhere on the board
/ID/Hazard Control/~FLUSH: U1.19 (CE), U2.25 (2~OE), U2.48 (1~OE); also elsewhere on the board
/ID/ID Flush/Ctl_ID0: U2.47 (1A1), U17.2 (1B1); also elsewhere on the board
/ID/ID Flush/Ctl_ID1: U2.46 (1A2), U17.3 (1B2); also elsewhere on the board
/ID/ID Flush/Ctl_ID2: U2.44 (1A3), U17.5 (1B3); also elsewhere on the board
/ID/ID Flush/Ctl_ID3: U2.43 (1A4), U17.6 (1B4); also elsewhere on the board
/ID/ID Flush/Ctl_ID4: U2.41 (1A5), U17.8 (1B5); also elsewhere on the board
/ID/ID Flush/Ctl_ID5: U2.40 (1A6), U17.9 (1B6); also elsewhere on the board
/ID/ID Flush/Ctl_ID6: U2.38 (1A7), U17.11 (1B7); also elsewhere on the board
/ID/ID Flush/Ctl_ID7: U2.37 (1A8), U17.12 (1B8); also elsewhere on the board
/ID/ID Flush/Ctl_ID8: U2.36 (2A1), U17.13 (2B1); also elsewhere on the board
/ID/ID Flush/Ctl_ID9: U2.35 (2A2), U17.14 (2B2); also elsewhere on the board
/ID/ID Flush/Ctl_ID10: U2.33 (2A3), U17.16 (2B3); also elsewhere on the board
/ID/ID Flush/Ctl_ID11: U2.32 (2A4), U17.17 (2B4); also elsewhere on the board
/ID/ID Flush/Ctl_ID12: U2.30 (2A5), U17.19 (2B5); also elsewhere on the board
/ID/ID Flush/Ctl_ID13: U2.29 (2A6), U17.20 (2B6); also elsewhere on the board
/ID/ID Flush/Ctl_ID14: U2.27 (2A7), U17.22 (2B7); also elsewhere on the board
/ID/ID Flush/Ctl_ID15: U2.26 (2A8), U17.23 (2B8); also elsewhere on the board
/ID/ID Flush/Ctl_ID16: U1.11 (B7), U18.9 (A7); also elsewhere on the board
/ID/ID Flush/Ctl_ID17: U1.12 (B6), U18.8 (A6); also elsewhere on the board
/ID/ID Flush/Ctl_ID18: U1.13 (B5), U18.7 (A5); also elsewhere on the board
/ID/ID Flush/Ctl_ID19: U1.14 (B4), U18.6 (A4); also elsewhere on the board
/ID/ID Flush/Ctl_ID20: U1.15 (B3), U18.5 (A3); also elsewhere on the board
/ID/ID Flush/Ctl_ID21: U1.16 (B2), U18.4 (A2); also elsewhere on the board
/ID/ID Flush/Ctl_ID22: U1.17 (B1), U18.3 (A1); also elsewhere on the board
/ID/ID Flush/Ctl_ID23: U1.18 (B0), U18.2 (A0); also elsewhere on the board
GND: C2.2, C3.2, C4.2, C17.2, U1.10 (GND), U2.1 (1DIR), U2.4 (GND), U2.10 (GND), U2.15 (GND), U2.21 (GND), U2.24 (2DIR), U2.28 (GND), U2.34 (GND), U2.39 (GND), U2.45 (GND), U17.4 (GND), U17.10 (GND), U17.15 (GND), U17.21 (GND), U17.28 (GND), U17.34 (GND), U17.39 (GND), U17.45 (GND), U18.1 (A->B), U18.10 (GND); also elsewhere on the board
VCC: C2.1, C3.1, C4.1, C17.1, U1.1 (A->B), U1.2 (A0), U1.3 (A1), U1.4 (A2), U1.5 (A3), U1.6 (A4), U1.7 (A5), U1.8 (A6), U1.9 (A7), U1.20 (VCC), U2.2 (1B1), U2.3 (1B2), U2.5 (1B3), U2.6 (1B4), U2.7 (VCC), U2.8 (1B5), U2.9 (1B6), U2.11 (1B7), U2.12 (1B8), U2.13 (2B1), U2.14 (2B2), U2.16 (2B3), U2.17 (2B4), U2.18 (VCC), U2.19 (2B5), U2.20 (2B6), U2.22 (2B7), U2.23 (2B8), U2.31 (VCC), U2.42 (VCC), U17.1 (1DIR), U17.7 (VCC), U17.18 (VCC), U17.24 (2DIR), U17.31 (VCC), U17.42 (VCC), U18.20 (VCC); also elsewhere on the board

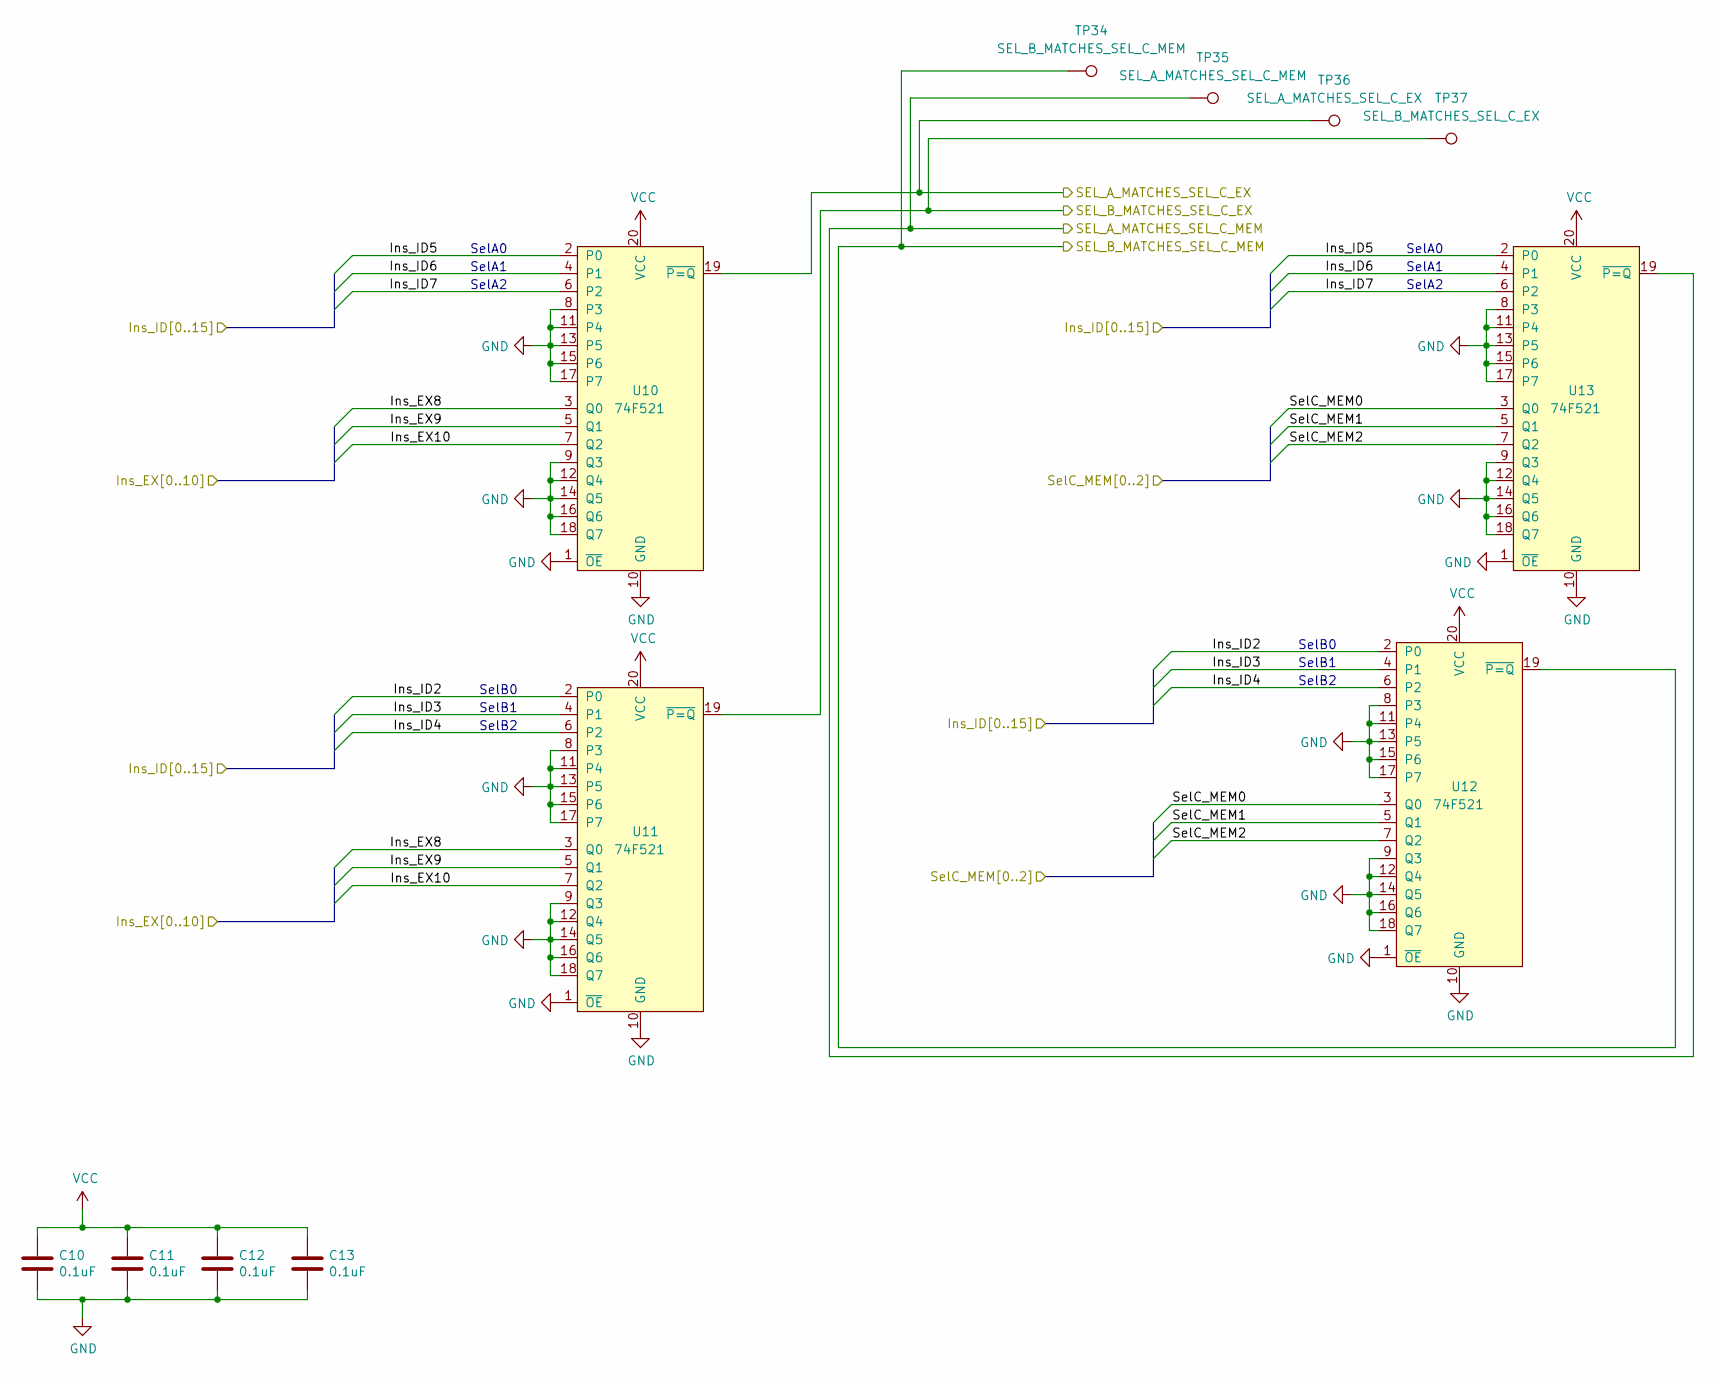
[picture p162: schematic HazardControlComparators.kicad_sch]

Parts:
C10, C11, C12, C13: 0.1uF; C_0603_1608Metric_Pad1.08x0.95mm_HandSolder
TP34: SEL_B_MATCHES_SEL_C_MEM; TestPoint_Pad_D1.0mm
TP35: SEL_A_MATCHES_SEL_C_MEM; TestPoint_Pad_D1.0mm
TP36: SEL_A_MATCHES_SEL_C_EX; TestPoint_Pad_D1.0mm
TP37: SEL_B_MATCHES_SEL_C_EX; TestPoint_Pad_D1.0mm
U10, U11, U12, U13: 74F521; SOIC-20W_7.5x12.8mm_P1.27mm

Connections:
/ID Prototype Inputs/Ins_ID2: U11.2 (P0), U12.2 (P0); also elsewhere on the board
/ID Prototype Inputs/Ins_ID3: U11.4 (P1), U12.4 (P1); also elsewhere on the board
/ID Prototype Inputs/Ins_ID4: U11.6 (P2), U12.6 (P2); also elsewhere on the board
/ID Prototype Inputs/Ins_ID5: U10.2 (P0), U13.2 (P0); also elsewhere on the board
/ID Prototype Inputs/Ins_ID6: U10.4 (P1), U13.4 (P1); also elsewhere on the board
/ID Prototype Inputs/Ins_ID7: U10.6 (P2), U13.6 (P2); also elsewhere on the board
/ID Prototype Inputs/SelC_MEM0: U12.3 (Q0), U13.3 (Q0); also elsewhere on the board
/ID Prototype Inputs/SelC_MEM1: U12.5 (Q1), U13.5 (Q1); also elsewhere on the board
/ID Prototype Inputs/SelC_MEM2: U12.7 (Q2), U13.7 (Q2); also elsewhere on the board
/ID Prototype Outputs/Ins_EX8: U10.3 (Q0), U11.3 (Q0); also elsewhere on the board
/ID Prototype Outputs/Ins_EX9: U10.5 (Q1), U11.5 (Q1); also elsewhere on the board
/ID Prototype Outputs/Ins_EX10: U10.7 (Q2), U11.7 (Q2); also elsewhere on the board
/ID/Hazard Control/Hazard Control Comparators/SEL_A_MATCHES_SEL_C_EX: TP36.1, U10.19 (~P=Q); also elsewhere on the board
/ID/Hazard Control/Hazard Control Comparators/SEL_A_MATCHES_SEL_C_MEM: TP35.1, U13.19 (~P=Q); also elsewhere on the board
/ID/Hazard Control/Hazard Control Comparators/SEL_B_MATCHES_SEL_C_EX: TP37.1, U11.19 (~P=Q); also elsewhere on the board
/ID/Hazard Control/Hazard Control Comparators/SEL_B_MATCHES_SEL_C_MEM: TP34.1, U12.19 (~P=Q); also elsewhere on the board
GND: C10.2, C11.2, C12.2, C13.2, U10.1 (~OE), U10.8 (P3), U10.9 (Q3), U10.10 (GND), U10.11 (P4), U10.12 (Q4), U10.13 (P5), U10.14 (Q5), U10.15 (P6), U10.16 (Q6), U10.17 (P7), U10.18 (Q7), U11.1 (~OE), U11.8 (P3), U11.9 (Q3), U11.10 (GND), U11.11 (P4), U11.12 (Q4), U11.13 (P5), U11.14 (Q5), U11.15 (P6), U11.16 (Q6), U11.17 (P7), U11.18 (Q7), U12.1 (~OE), U12.8 (P3), U12.9 (Q3), U12.10 (GND), U12.11 (P4), U12.12 (Q4), U12.13 (P5), U12.14 (Q5), U12.15 (P6), U12.16 (Q6), U12.17 (P7), U12.18 (Q7), U13.1 (~OE), U13.8 (P3), U13.9 (Q3), U13.10 (GND), U13.11 (P4), U13.12 (Q4), U13.13 (P5), U13.14 (Q5), U13.15 (P6), U13.16 (Q6), U13.17 (P7), U13.18 (Q7); also elsewhere on the board
VCC: C10.1, C11.1, C12.1, C13.1, U10.20 (VCC), U11.20 (VCC), U12.20 (VCC), U13.20 (VCC); also elsewhere on the board

Notes on the sheet:
SelA0
SelB1
SelA2
SelA1
SelB2
SelB0

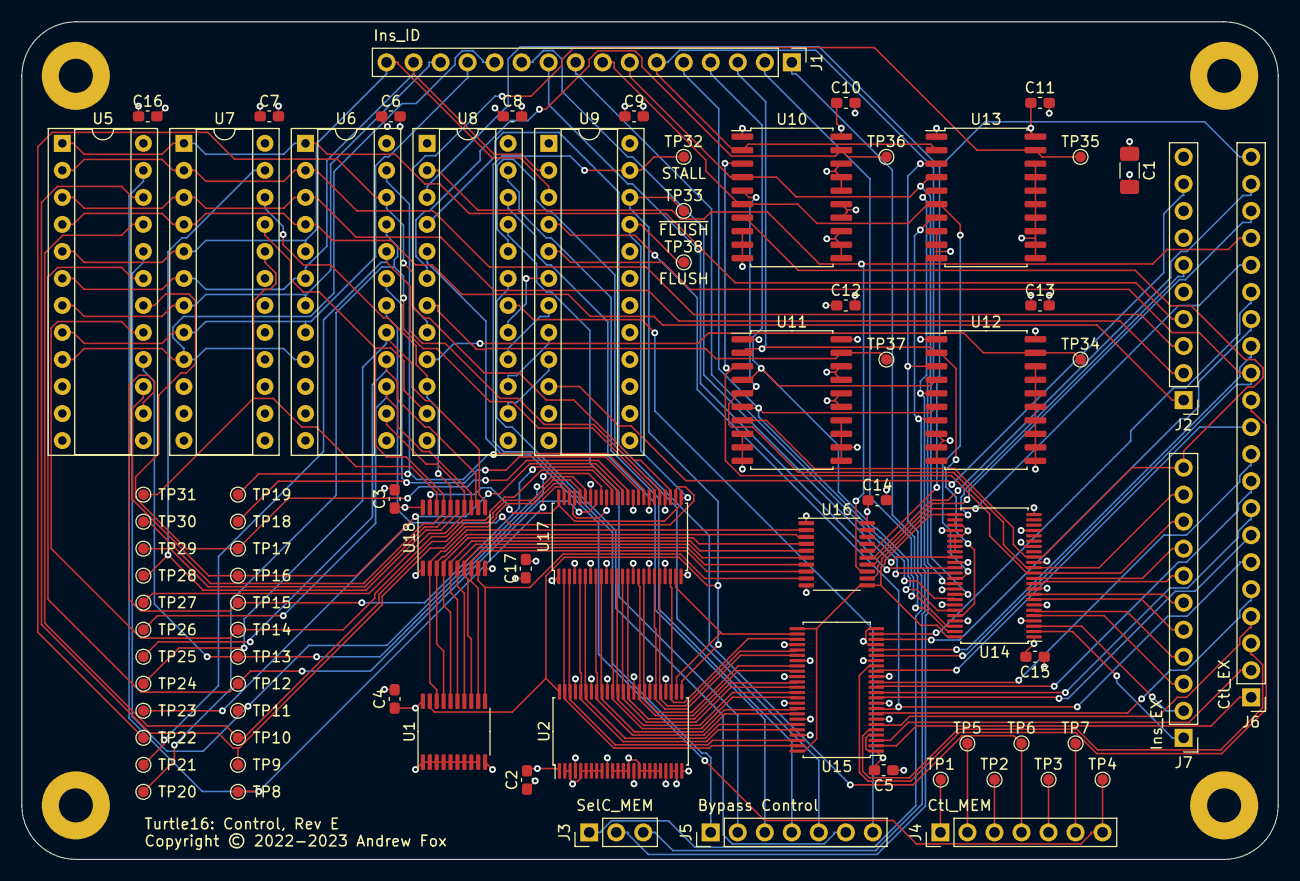
[picture p163: board ControlModule.kicad_pcb from above]

Board: 4 copper layers, 118.1 x 78.7 mm, 82 parts (0 on the bottom side), 131 nets.
