foxostro/Turtle16/Hardware/MonolithicProcessor/MainBoard/MainBoard.kicad_pcb

## KiCad design Hardware/MonolithicProcessor/MainBoard/MainBoard.kicad_pcb (2025-06-30, an earlier design)

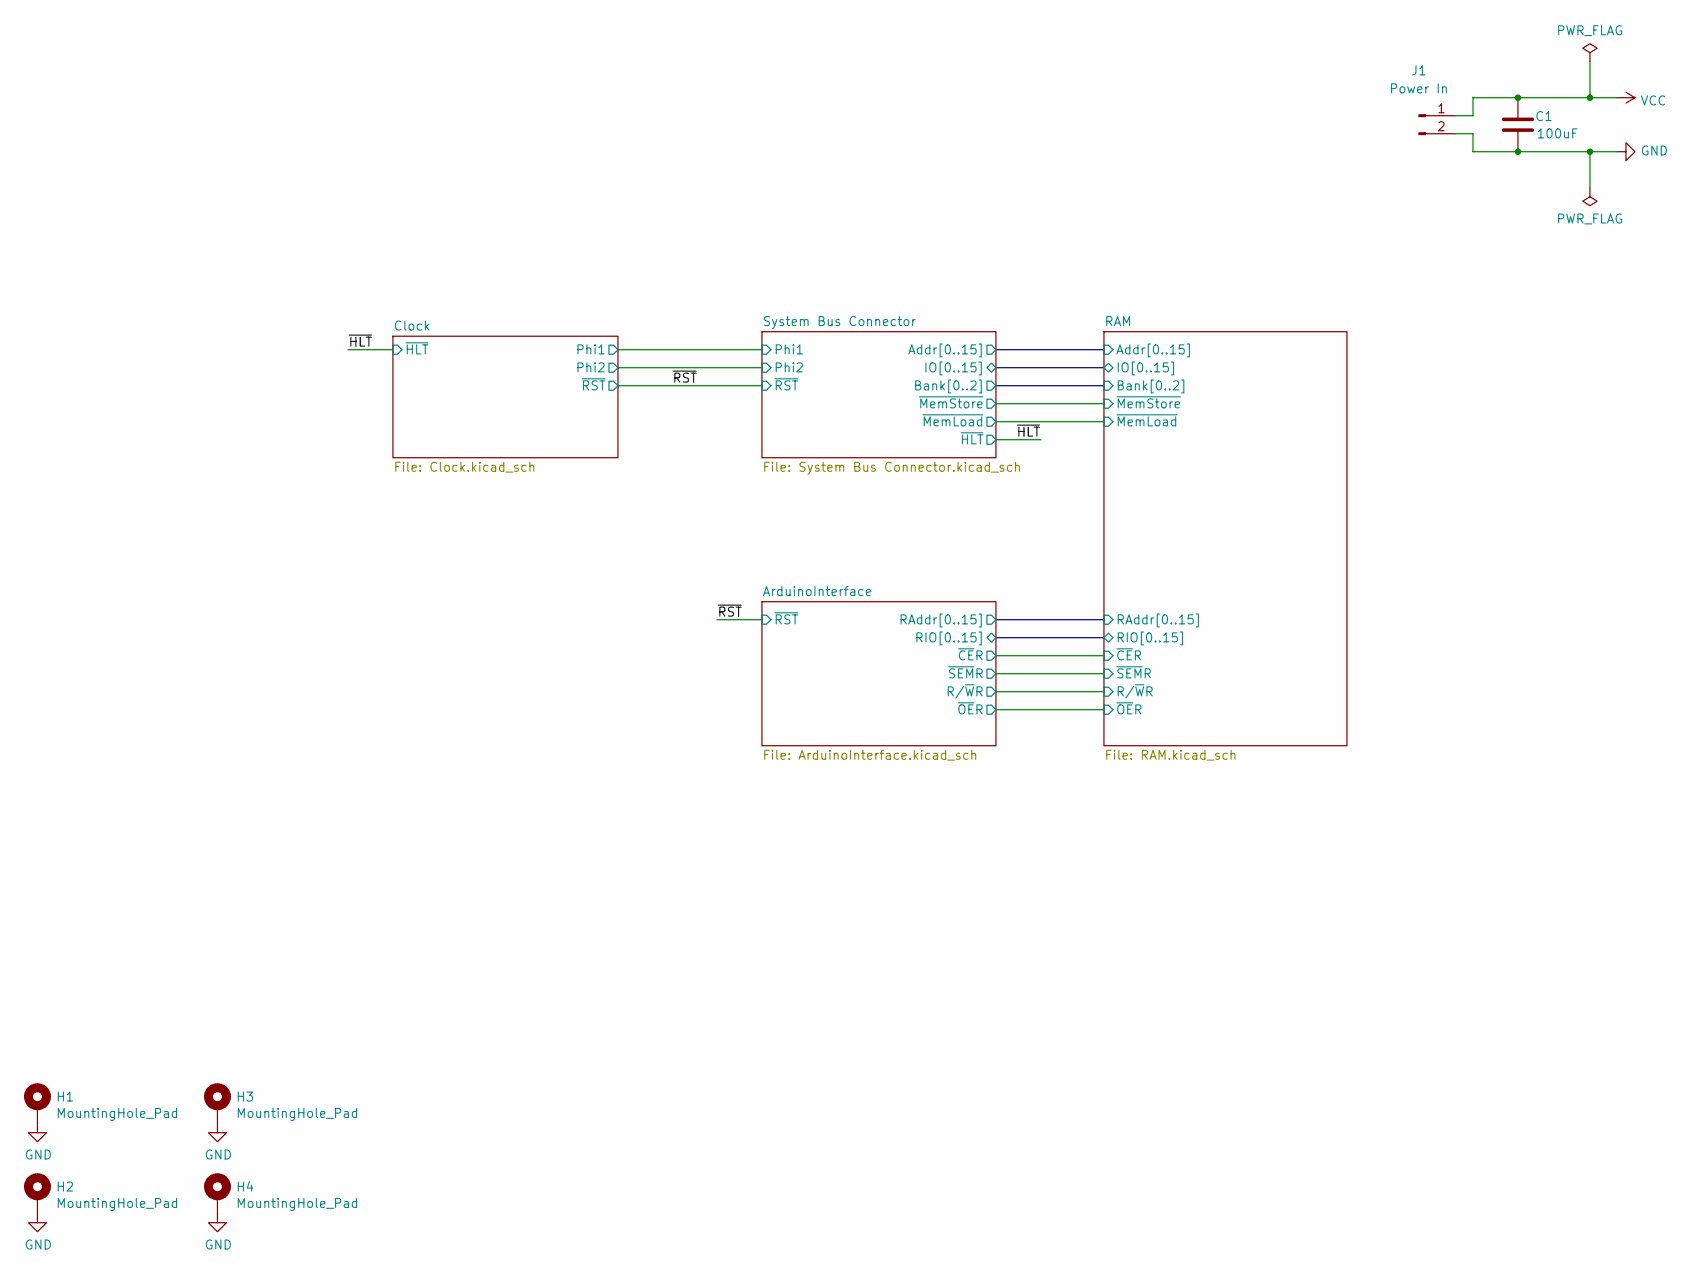
[picture p164: schematic MainBoard.kicad_sch, Turtle16: Main Board]

Parts:
C1: 100uF; C_1206_3216Metric; Manufacturer# AMK316ABJ107ML-T; Mouser# 963-AMK316ABJ107ML-T
H1, H2, H3, H4: MountingHole_Pad; MountingHole_3.2mm_M3_Pad
J1: Power In; 172448-0002; Manufacturer# 172448-0002; Mouser# 538-172448-0002

Connections:
GND: C1.2, H1.1, H2.1, H3.1, H4.1, J1.2; also elsewhere on the board
VCC: C1.1, J1.1; also elsewhere on the board

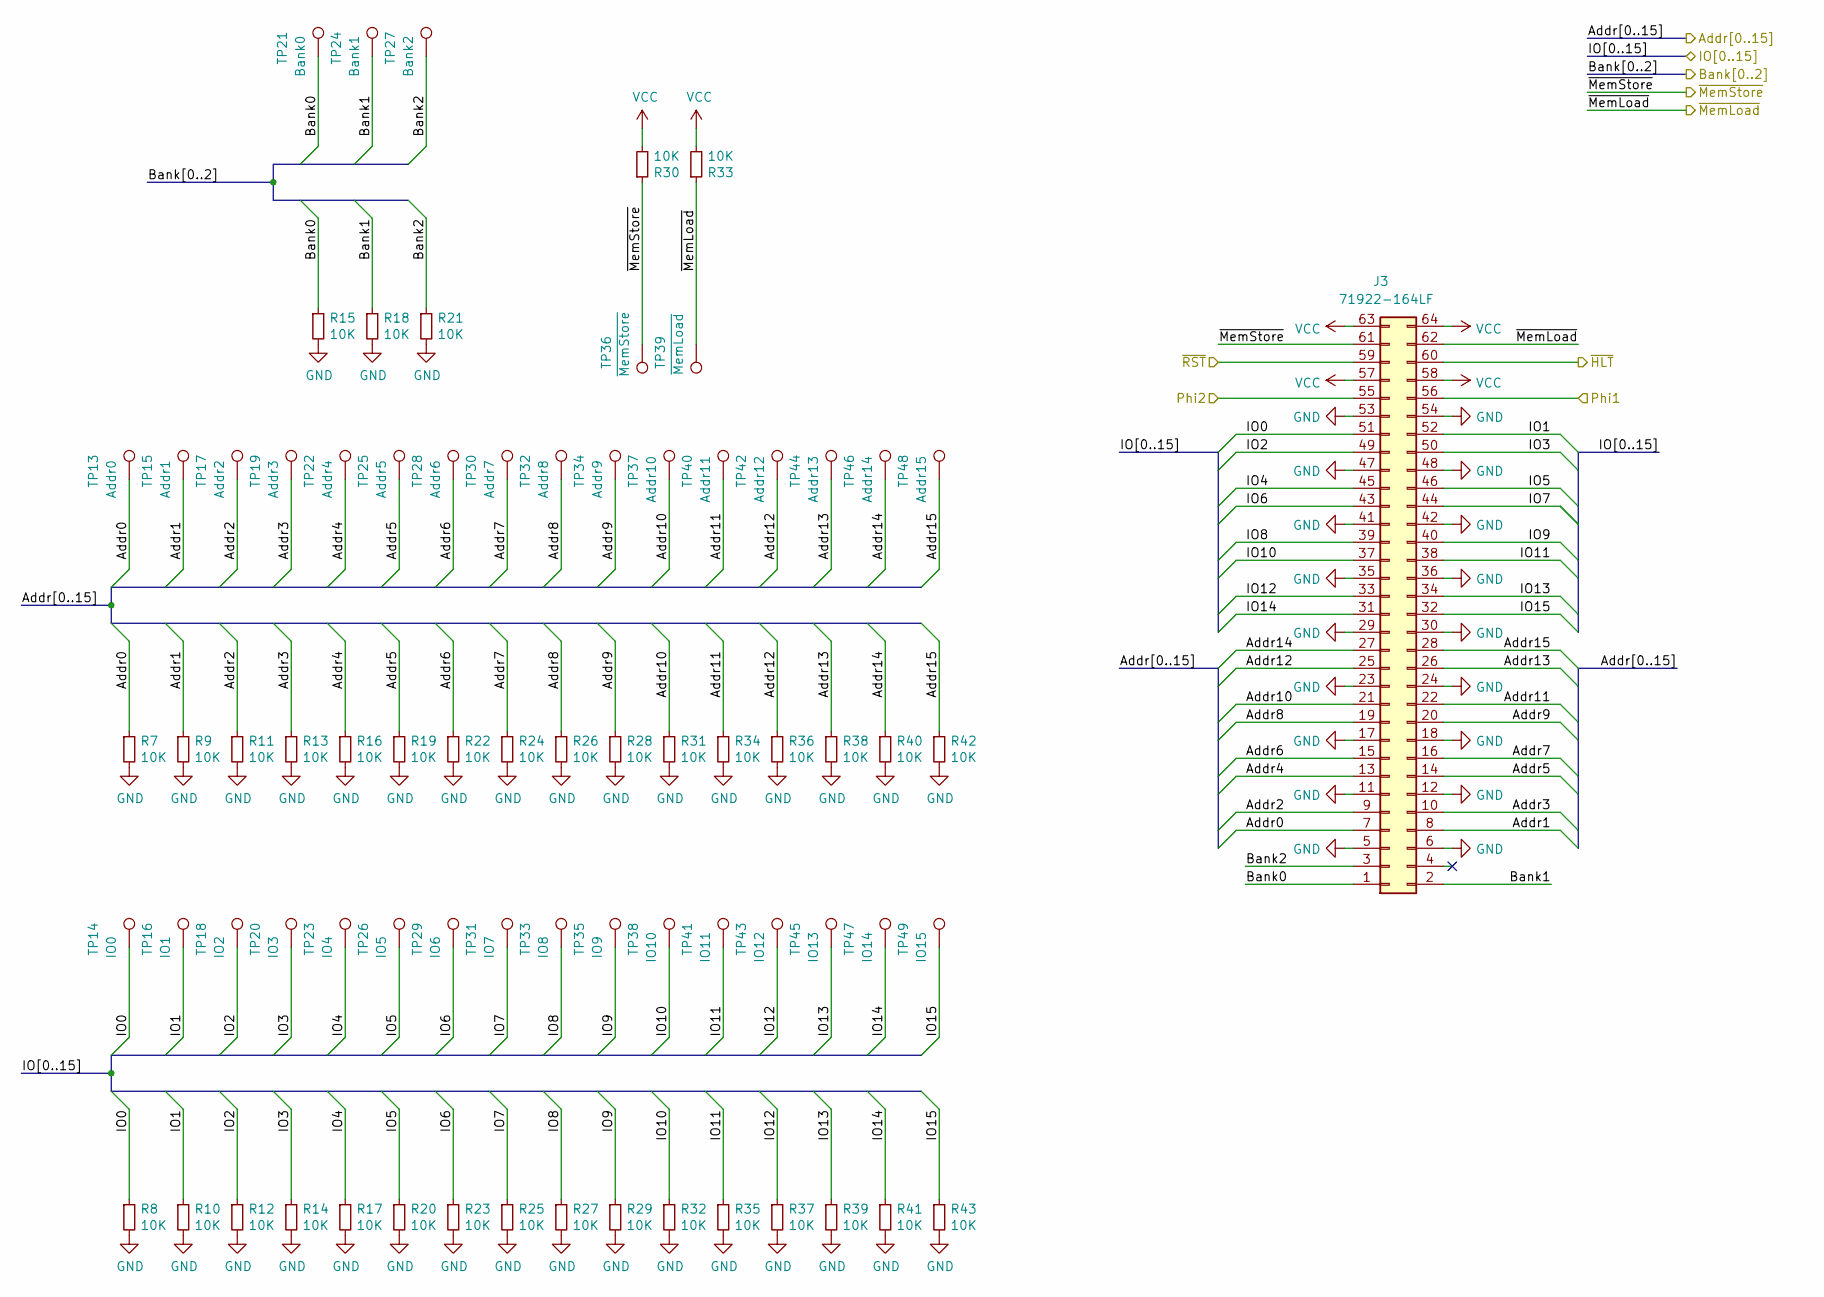
[picture p165: schematic System Bus Connector.kicad_sch, Turtle16: System Bus Connector]

Parts:
J3: 71922-164LF; IDC-Header_2x32_P2.54mm_Horizontal; Manufacturer# 71922-164LF; Mouser# 649-71922-164LF
R7, R8, R9, R10, R11, R12, R13, R14, R15, R16, R17, R18, R19, R20, R21, R22, R23, R24, R25, R26, R27, R28, R29, R30, R31, R32, R33, R34, R35, R36, R37, R38, R39, R40, R41, R42, R43: 10K; R_0603_1608Metric; Manufacturer# CR0603-FX-1002ELF; Mouser# 652-CR0603FX-1002ELF
TP13: Addr0; TestPoint_Pad_D1.0mm
TP14: IO0; TestPoint_Pad_D1.0mm
TP15: Addr1; TestPoint_Pad_D1.0mm
TP16: IO1; TestPoint_Pad_D1.0mm
TP17: Addr2; TestPoint_Pad_D1.0mm
TP18: IO2; TestPoint_Pad_D1.0mm
TP19: Addr3; TestPoint_Pad_D1.0mm
TP20: IO3; TestPoint_Pad_D1.0mm
TP21: Bank0; TestPoint_Pad_D1.0mm
TP22: Addr4; TestPoint_Pad_D1.0mm
TP23: IO4; TestPoint_Pad_D1.0mm
TP24: Bank1; TestPoint_Pad_D1.0mm
TP25: Addr5; TestPoint_Pad_D1.0mm
TP26: IO5; TestPoint_Pad_D1.0mm
TP27: Bank2; TestPoint_Pad_D1.0mm
TP28: Addr6; TestPoint_Pad_D1.0mm
TP29: IO6; TestPoint_Pad_D1.0mm
TP30: Addr7; TestPoint_Pad_D1.0mm
TP31: IO7; TestPoint_Pad_D1.0mm
TP32: Addr8; TestPoint_Pad_D1.0mm
TP33: IO8; TestPoint_Pad_D1.0mm
TP34: Addr9; TestPoint_Pad_D1.0mm
TP35: IO9; TestPoint_Pad_D1.0mm
TP36: ~{MemStore}; TestPoint_Pad_D1.0mm
TP37: Addr10; TestPoint_Pad_D1.0mm
TP38: IO10; TestPoint_Pad_D1.0mm
TP39: ~{MemLoad}; TestPoint_Pad_D1.0mm
TP40: Addr11; TestPoint_Pad_D1.0mm
TP41: IO11; TestPoint_Pad_D1.0mm
TP42: Addr12; TestPoint_Pad_D1.0mm
TP43: IO12; TestPoint_Pad_D1.0mm
TP44: Addr13; TestPoint_Pad_D1.0mm
TP45: IO13; TestPoint_Pad_D1.0mm
TP46: Addr14; TestPoint_Pad_D1.0mm
TP47: IO14; TestPoint_Pad_D1.0mm
TP48: Addr15; TestPoint_Pad_D1.0mm
TP49: IO15; TestPoint_Pad_D1.0mm

Connections:
/Clock/Phi1: J3.56; also elsewhere on the board
/Clock/Phi2: J3.55; also elsewhere on the board
/RAM/Addr0: J3.7, R7.1, TP13.1; also elsewhere on the board
/RAM/Addr1: J3.8, R9.1, TP15.1; also elsewhere on the board
/RAM/Addr2: J3.9, R11.1, TP17.1; also elsewhere on the board
/RAM/Addr3: J3.10, R13.1, TP19.1; also elsewhere on the board
/RAM/Addr4: J3.13, R16.1, TP22.1; also elsewhere on the board
/RAM/Addr5: J3.14, R19.1, TP25.1; also elsewhere on the board
/RAM/Addr6: J3.15, R22.1, TP28.1; also elsewhere on the board
/RAM/Addr7: J3.16, R24.1, TP30.1; also elsewhere on the board
/RAM/Addr8: J3.19, R26.1, TP32.1; also elsewhere on the board
/RAM/Addr9: J3.20, R28.1, TP34.1; also elsewhere on the board
/RAM/Addr10: J3.21, R31.1, TP37.1; also elsewhere on the board
/RAM/Addr11: J3.22, R34.1, TP40.1; also elsewhere on the board
/RAM/Addr12: J3.25, R36.1, TP42.1; also elsewhere on the board
/RAM/Addr13: J3.26, R38.1, TP44.1; also elsewhere on the board
/RAM/Addr14: J3.27, R40.1, TP46.1; also elsewhere on the board
/RAM/Addr15: J3.28, R42.1, TP48.1; also elsewhere on the board
/RAM/Bank0: J3.1, R15.1, TP21.1; also elsewhere on the board
/RAM/Bank1: J3.2, R18.1, TP24.1; also elsewhere on the board
/RAM/Bank2: J3.3, R21.1, TP27.1; also elsewhere on the board
/RAM/IO0: J3.51, R8.1, TP14.1; also elsewhere on the board
/RAM/IO1: J3.52, R10.1, TP16.1; also elsewhere on the board
/RAM/IO2: J3.49, R12.1, TP18.1; also elsewhere on the board
/RAM/IO3: J3.50, R14.1, TP20.1; also elsewhere on the board
/RAM/IO4: J3.45, R17.1, TP23.1; also elsewhere on the board
/RAM/IO5: J3.46, R20.1, TP26.1; also elsewhere on the board
/RAM/IO6: J3.43, R23.1, TP29.1; also elsewhere on the board
/RAM/IO7: J3.44, R25.1, TP31.1; also elsewhere on the board
/RAM/IO8: J3.39, R27.1, TP33.1; also elsewhere on the board
/RAM/IO9: J3.40, R29.1, TP35.1; also elsewhere on the board
/RAM/IO10: J3.37, R32.1, TP38.1; also elsewhere on the board
/RAM/IO11: J3.38, R35.1, TP41.1; also elsewhere on the board
/RAM/IO12: J3.33, R37.1, TP43.1; also elsewhere on the board
/RAM/IO13: J3.34, R39.1, TP45.1; also elsewhere on the board
/RAM/IO14: J3.31, R41.1, TP47.1; also elsewhere on the board
/RAM/IO15: J3.32, R43.1, TP49.1; also elsewhere on the board
/RAM/~MemLoad: J3.62, R33.1, TP39.1; also elsewhere on the board
/RAM/~MemStore: J3.61, R30.1, TP36.1; also elsewhere on the board
/~HLT: J3.60; also elsewhere on the board
/~RST: J3.59; also elsewhere on the board
GND: J3.5, J3.6, J3.11, J3.12, J3.17, J3.18, J3.23, J3.24, J3.29, J3.30, J3.35, J3.36, J3.41, J3.42, J3.47, J3.48, J3.53, J3.54, R7.2, R8.2, R9.2, R10.2, R11.2, R12.2, R13.2, R14.2, R15.2, R16.2, R17.2, R18.2, R19.2, R20.2, R21.2, R22.2, R23.2, R24.2, R25.2, R26.2, R27.2, R28.2, R29.2, R31.2, R32.2, R34.2, R35.2, R36.2, R37.2, R38.2, R39.2, R40.2, R41.2, R42.2, R43.2; also elsewhere on the board
VCC: J3.57, J3.58, J3.63, J3.64, R30.2, R33.2; also elsewhere on the board
