foxostro/Turtle16/Hardware/MonolithicProcessor/MainBoard/MainBoard.kicad_pcb

## KiCad design Hardware/MonolithicProcessor/MainBoard/MainBoard.kicad_pcb (continued)

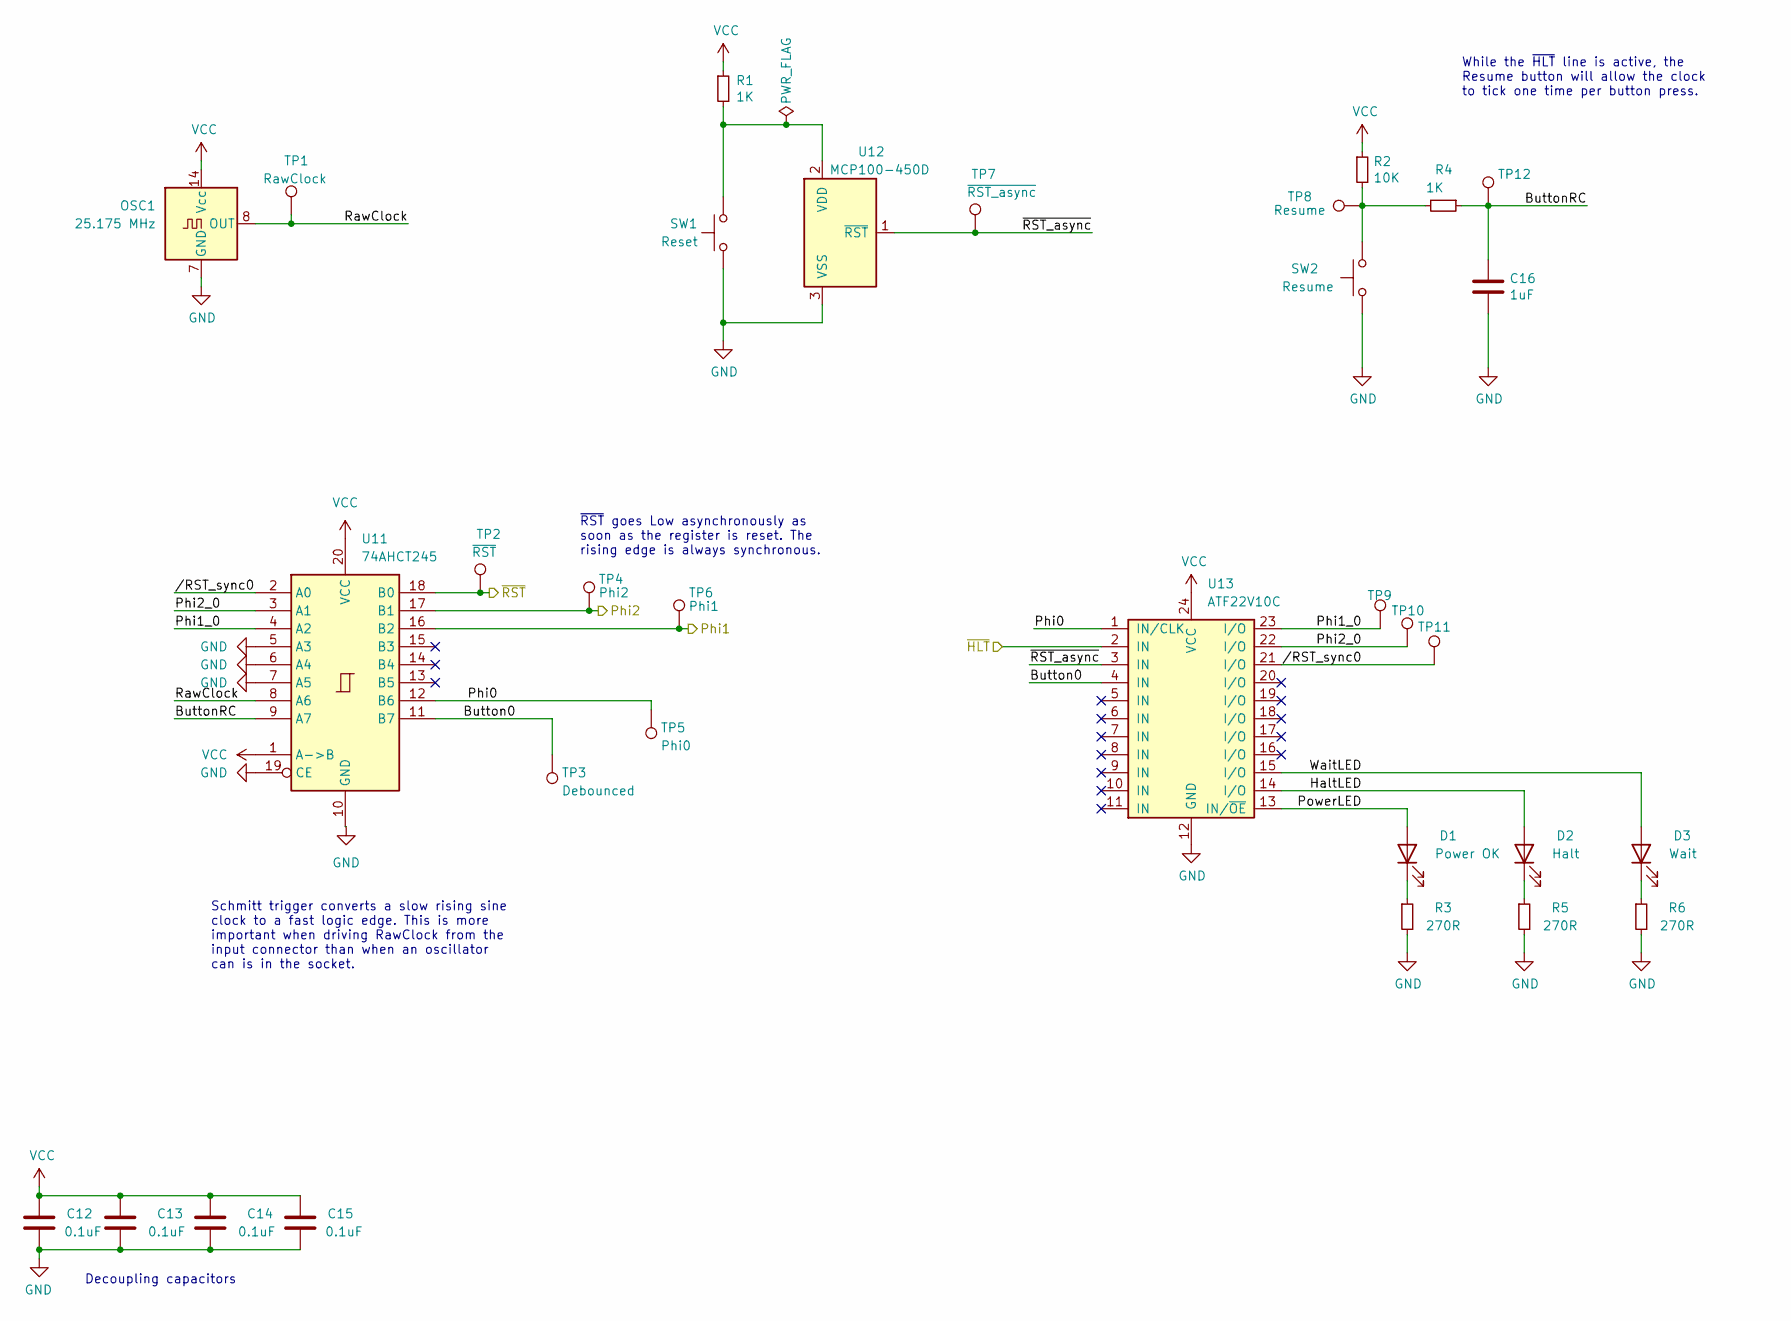
[picture p166: schematic Clock.kicad_sch, Turtle16: Clock]

Parts:
C12, C13, C14, C15: 0.1uF; C_0603_1608Metric; Manufacturer# EMK107B7104KAHT; Mouser# 963-EMK107B7104KAHT
C16: 1uF; C_0603_1608Metric; Manufacturer# CR0603-FX-2700ELF; Mouser# 652-CR0603FX-2700ELF
D1: Power OK; LED_0805_2012Metric; Manufacturer# AP2012ID; Mouser# 604-AP2012ID
D2: Halt; LED_0805_2012Metric; Manufacturer# AP2012ID; Mouser# 604-AP2012ID
D3: Wait; LED_0805_2012Metric; Manufacturer# AP2012ID; Mouser# 604-AP2012ID
OSC1: 25.175 MHz; Oscillator_DIP-14; Manufacturer# 1107741; Mouser# 535-1107741
R1: 1K; R_0603_1608Metric; Manufacturer# CR0603-FX-1002ELF; Mouser# 652-CR0603FX-1002ELF
R2: 10K; R_0603_1608Metric; Manufacturer# CR0603-FX-1002ELF; Mouser# 652-CR0603FX-1002ELF
R3, R5, R6: 270R; R_0603_1608Metric; Manufacturer# CR0603-FX-2700ELF; Mouser# 652-CR0603FX-2700ELF
R4: 1K; R_0603_1608Metric; Manufacturer# CR0603-FX-1001ELF; Mouser# 652-CR0603FX-1001ELF
SW1: Reset; SW_PUSH_6mm_H5mm
SW2: Resume; SW_PUSH_6mm_H5mm
TP1: RawClock; TestPoint_Pad_D1.0mm
TP2: ~{RST}; TestPoint_Pad_D1.0mm
TP3: Debounced; TestPoint_Pad_D1.0mm
TP4: Phi2; TestPoint_Pad_D1.0mm
TP5: Phi0; TestPoint_Pad_D1.0mm
TP6: Phi1; TestPoint_Pad_D1.0mm
TP7: ~{RST_async}; TestPoint_Pad_D1.0mm
TP8: Resume; TestPoint_Pad_D1.0mm
TP9: TestPoint_Pad_D1.0mm
TP10, TP11, TP12: TP; TestPoint_Pad_D1.0mm
U11: 74AHCT245; TSSOP-20_4.4x6.5mm_P0.65mm; Manufacturer# SN74AHCT245PWR; Mouser# 595-SN74AHCT245PWR
U12: MCP100-450D; TO-92; Manufacturer# MCP100-450DI/TO; Mouser# 579-MCP100-450DI/TO
U13: ATF22V10C; DIP-24_W7.62mm_Socket; Manufacturer# ATF22V10C-7PX; Mouser# 556-AF22V10C7PX

Connections:
/Clock/Button0: TP3.1, U11.11 (B7), U13.4 (IN)
/Clock/ButtonRC: C16.1, R4.1, TP12.1, U11.9 (A7)
/Clock/HaltLED: D2.2 (A), U13.14 (I/O)
/Clock/Phi0: TP5.1, U11.12 (B6), U13.1 (IN/CLK)
/Clock/Phi1: TP6.1, U11.16 (B2); also elsewhere on the board
/Clock/Phi1_0: TP9.1, U11.4 (A2), U13.23 (I/O)
/Clock/Phi2: TP4.1, U11.17 (B1); also elsewhere on the board
/Clock/Phi2_0: TP10.1, U11.3 (A1), U13.22 (I/O)
/Clock/PowerLED: D1.2 (A), U13.13 (IN/~OE)
/Clock/RawClock: OSC1.8 (OUT), TP1.1, U11.8 (A6)
/Clock/WaitLED: D3.2 (A), U13.15 (I/O)
/Clock//RST_sync0: TP11.1, U11.2 (A0), U13.21 (I/O)
/Clock/~RST_async: TP7.1, U12.1 (~RST), U13.3 (IN)
/~HLT: U13.2 (IN); also elsewhere on the board
/~RST: TP2.1, U11.18 (B0); also elsewhere on the board
GND: C12.2, C13.2, C14.2, C15.2, C16.2, OSC1.7 (GND), R3.2, R5.2, R6.2, SW1.1, SW2.1, U11.5 (A3), U11.6 (A4), U11.7 (A5), U11.10 (GND), U11.19 (CE), U12.3 (VSS), U13.12 (GND); also elsewhere on the board
unnamed: D1.1 (K), R3.1
unnamed: D2.1 (K), R5.1
unnamed: D3.1 (K), R6.1
unnamed: R2.2, R4.2, SW2.2, TP8.1
unnamed: R1.2, SW1.2, U12.2 (VDD)
VCC: C12.1, C13.1, C14.1, C15.1, OSC1.14 (Vcc), R1.1, R2.1, U11.1 (A->B), U11.20 (VCC), U13.24 (VCC); also elsewhere on the board

Notes on the sheet:
~{RST} goes Low asynchronously as soon as the register is reset. The rising edge is always synchronous.
Schmitt trigger converts a slow rising sine clock to a fast logic edge. This is more important when driving RawClock from the input connector than when an oscillator can is in the socket.
While the ~{HLT} line is active, the Resume button will allow the clock to tick one time per button press.
Decoupling capacitors

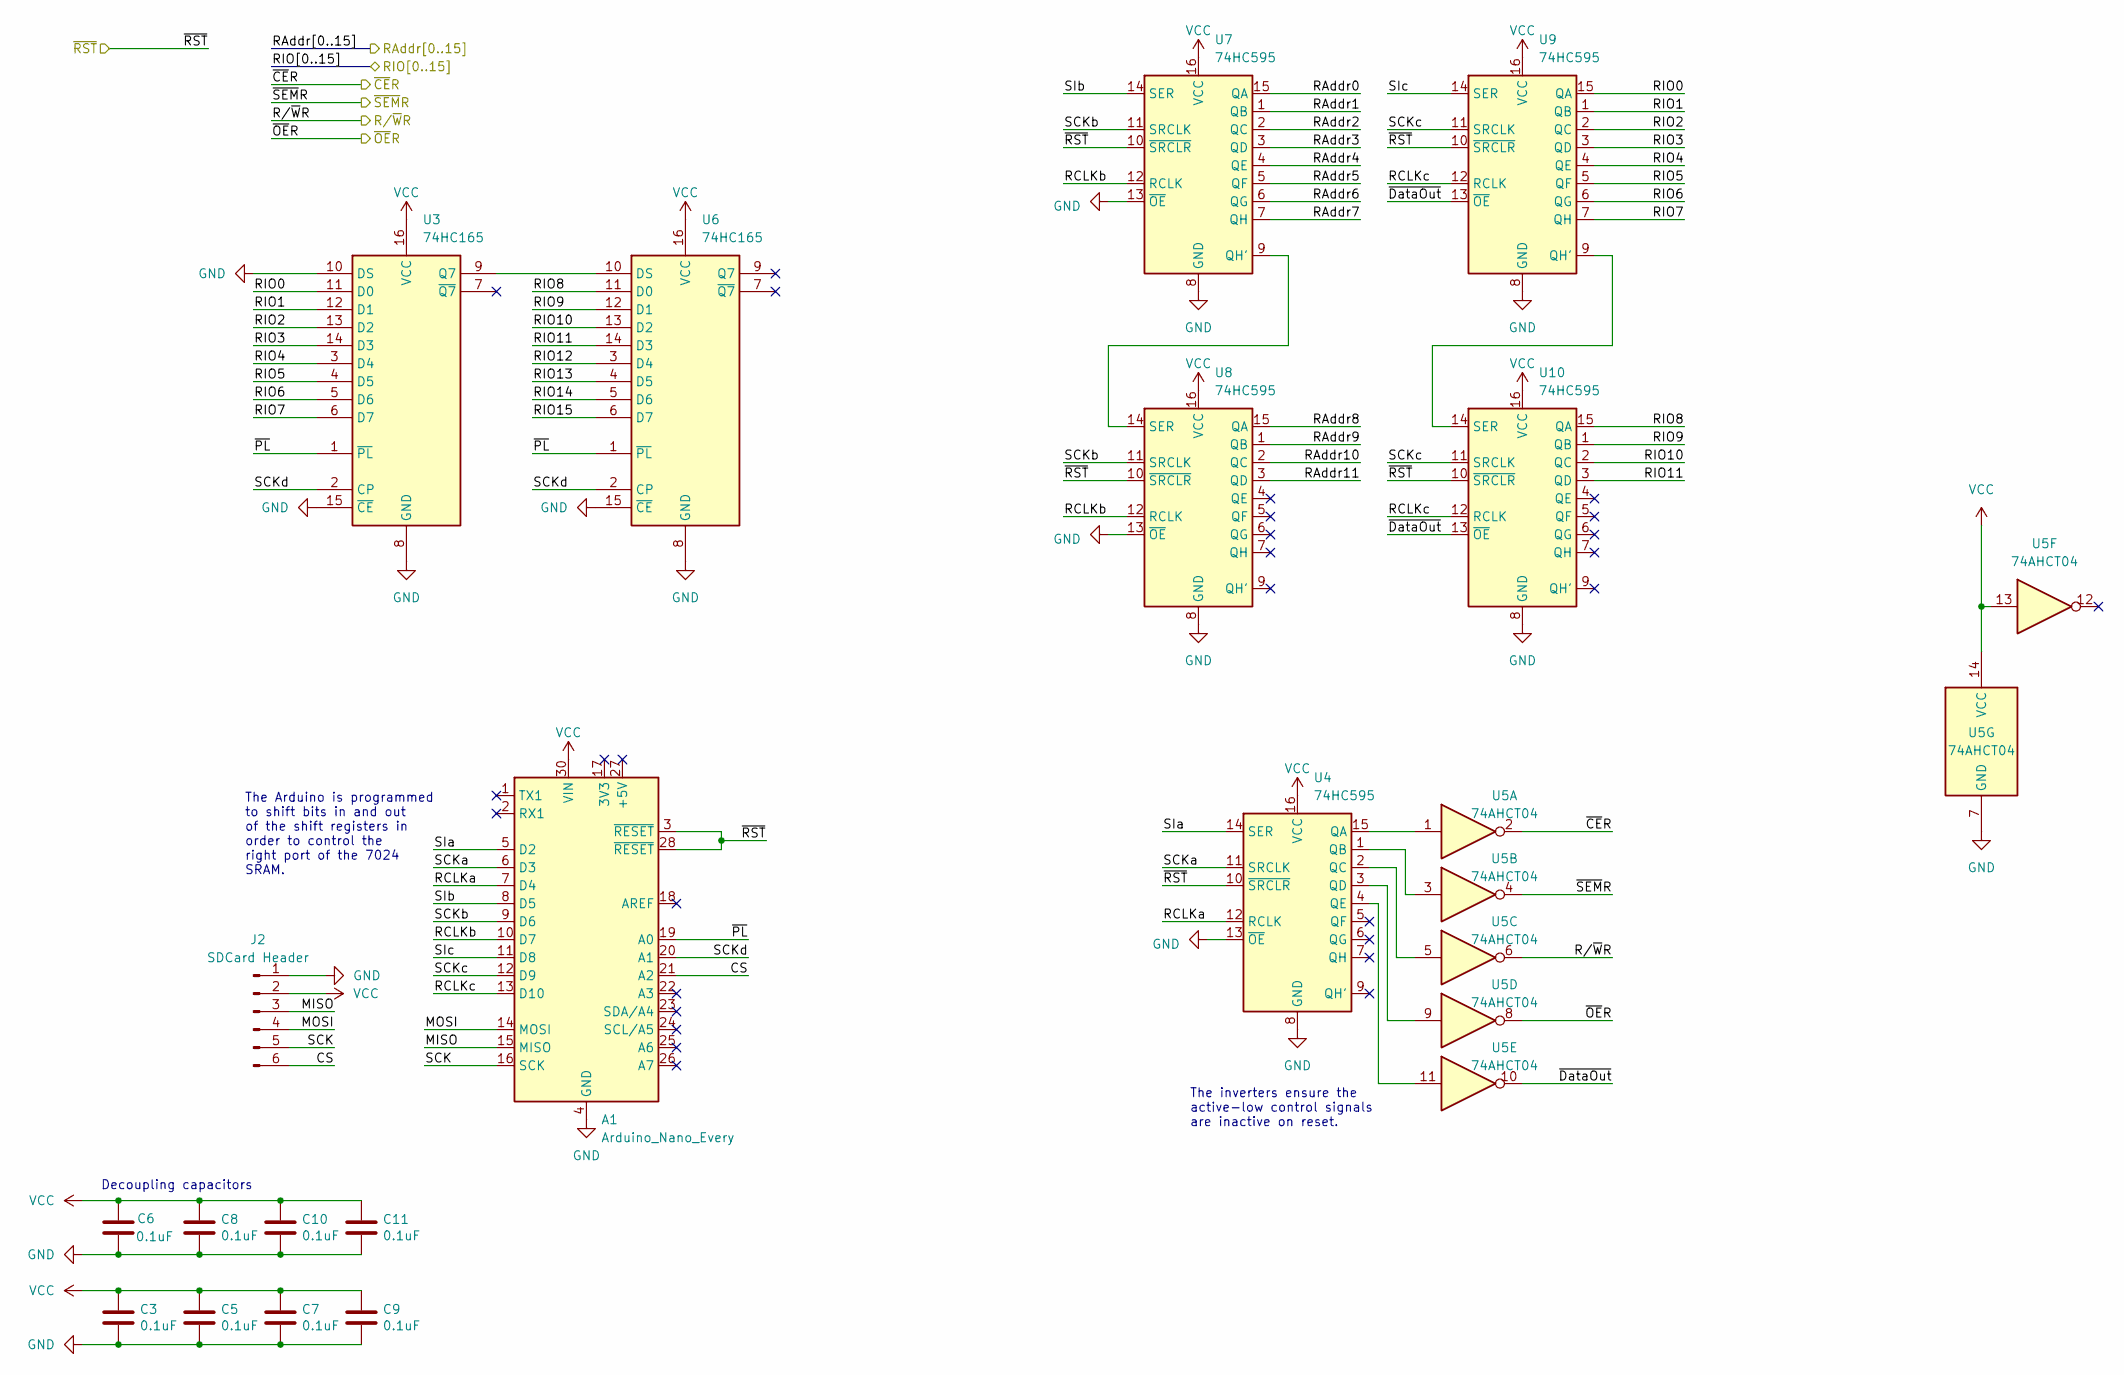
[picture p167: schematic ArduinoInterface.kicad_sch, Turtle16: Arduino Interface]

Parts:
A1: Arduino_Nano_Every; Arduino_Nano
C3, C5, C6, C7, C8, C9, C10, C11: 0.1uF; C_0603_1608Metric; Manufacturer# EMK107B7104KAHT; Mouser# 963-EMK107B7104KAHT
J2: SDCard Header; PinHeader_1x06_P2.54mm_Vertical
U3, U6: 74HC165; TSSOP-16_4.4x5mm_P0.65mm; Manufacturer# 74HC165PW-Q100,118; Mouser# 771-74HC165PWQ100118
U4, U7, U8, U9, U10: 74HC595; TSSOP-16_4.4x5mm_P0.65mm; Manufacturer# 74HC595PW-Q100,118; Mouser# 771-74HC595PW-Q100
U5: 74AHCT04; TSSOP-14_4.4x5mm_P0.65mm; Manufacturer# 74AHCT04APWJ; Mouser# 771-74AHCT04APWJ

Connections:
/ArduinoInterface/CS: A1.21 (A2), J2.6
/ArduinoInterface/MISO: A1.15 (MISO), J2.3
/ArduinoInterface/MOSI: A1.14 (MOSI), J2.4
/ArduinoInterface/RAddr0: U7.15 (QA); also elsewhere on the board
/ArduinoInterface/RAddr1: U7.1 (QB); also elsewhere on the board
/ArduinoInterface/RAddr2: U7.2 (QC); also elsewhere on the board
/ArduinoInterface/RAddr3: U7.3 (QD); also elsewhere on the board
/ArduinoInterface/RAddr4: U7.4 (QE); also elsewhere on the board
/ArduinoInterface/RAddr5: U7.5 (QF); also elsewhere on the board
/ArduinoInterface/RAddr6: U7.6 (QG); also elsewhere on the board
/ArduinoInterface/RAddr7: U7.7 (QH); also elsewhere on the board
/ArduinoInterface/RAddr8: U8.15 (QA); also elsewhere on the board
/ArduinoInterface/RAddr9: U8.1 (QB); also elsewhere on the board
/ArduinoInterface/RAddr10: U8.2 (QC); also elsewhere on the board
/ArduinoInterface/RAddr11: U8.3 (QD); also elsewhere on the board
/ArduinoInterface/RCLKa: A1.7 (D4), U4.12 (RCLK)
/ArduinoInterface/RCLKb: A1.10 (D7), U7.12 (RCLK), U8.12 (RCLK)
/ArduinoInterface/RCLKc: A1.13 (D10), U9.12 (RCLK), U10.12 (RCLK)
/ArduinoInterface/RIO0: U3.11 (D0), U9.15 (QA); also elsewhere on the board
/ArduinoInterface/RIO1: U3.12 (D1), U9.1 (QB); also elsewhere on the board
/ArduinoInterface/RIO2: U3.13 (D2), U9.2 (QC); also elsewhere on the board
/ArduinoInterface/RIO3: U3.14 (D3), U9.3 (QD); also elsewhere on the board
/ArduinoInterface/RIO4: U3.3 (D4), U9.4 (QE); also elsewhere on the board
/ArduinoInterface/RIO5: U3.4 (D5), U9.5 (QF); also elsewhere on the board
/ArduinoInterface/RIO6: U3.5 (D6), U9.6 (QG); also elsewhere on the board
/ArduinoInterface/RIO7: U3.6 (D7), U9.7 (QH); also elsewhere on the board
/ArduinoInterface/RIO8: U6.11 (D0), U10.15 (QA); also elsewhere on the board
/ArduinoInterface/RIO9: U6.12 (D1), U10.1 (QB); also elsewhere on the board
/ArduinoInterface/RIO10: U6.13 (D2), U10.2 (QC); also elsewhere on the board
/ArduinoInterface/RIO11: U6.14 (D3), U10.3 (QD); also elsewhere on the board
/ArduinoInterface/RIO12: U6.3 (D4); also elsewhere on the board
/ArduinoInterface/RIO13: U6.4 (D5); also elsewhere on the board
/ArduinoInterface/RIO14: U6.5 (D6); also elsewhere on the board
/ArduinoInterface/RIO15: U6.6 (D7); also elsewhere on the board
/ArduinoInterface/R/~WR: U5.6; also elsewhere on the board
/ArduinoInterface/SCK: A1.16 (SCK), J2.5
/ArduinoInterface/SCKa: A1.6 (D3), U4.11 (SRCLK)
/ArduinoInterface/SCKb: A1.9 (D6), U7.11 (SRCLK), U8.11 (SRCLK)
/ArduinoInterface/SCKc: A1.12 (D9), U9.11 (SRCLK), U10.11 (SRCLK)
/ArduinoInterface/SCKd: A1.20 (A1), U3.2 (CP), U6.2 (CP)
/ArduinoInterface/SIa: A1.5 (D2), U4.14 (SER)
/ArduinoInterface/SIb: A1.8 (D5), U7.14 (SER)
/ArduinoInterface/SIc: A1.11 (D8), U9.14 (SER)
/ArduinoInterface/~CER: U5.2; also elsewhere on the board
/ArduinoInterface/~DataOut: U5.10, U9.13 (~OE), U10.13 (~OE)
/ArduinoInterface/~OER: U5.8; also elsewhere on the board
/ArduinoInterface/~PL: A1.19 (A0), U3.1 (~PL), U6.1 (~PL)
/ArduinoInterface/~SEMR: U5.4; also elsewhere on the board
/~RST: A1.3 (~RESET), A1.28 (~RESET), U4.10 (~SRCLR), U7.10 (~SRCLR), U8.10 (~SRCLR), U9.10 (~SRCLR), U10.10 (~SRCLR); also elsewhere on the board
GND: A1.4 (GND), A1.29 (GND), C3.2, C5.2, C6.2, C7.2, C8.2, C9.2, C10.2, C11.2, J2.1, U3.8 (GND), U3.10 (DS), U3.15 (~CE), U4.8 (GND), U4.13 (~OE), U5.7 (GND), U6.8 (GND), U6.15 (~CE), U7.8 (GND), U7.13 (~OE), U8.8 (GND), U8.13 (~OE), U9.8 (GND), U10.8 (GND); also elsewhere on the board
unnamed: U3.9 (Q7), U6.10 (DS)
unnamed: U4.15 (QA), U5.1
unnamed: U4.1 (QB), U5.3
unnamed: U4.2 (QC), U5.5
unnamed: U4.3 (QD), U5.9
unnamed: U4.4 (QE), U5.11
unnamed: U7.9 (QH'), U8.14 (SER)
unnamed: U9.9 (QH'), U10.14 (SER)
VCC: A1.30 (VIN), C3.1, C5.1, C6.1, C7.1, C8.1, C9.1, C10.1, C11.1, J2.2, U3.16 (VCC), U4.16 (VCC), U5.13, U5.14 (VCC), U6.16 (VCC), U7.16 (VCC), U8.16 (VCC), U9.16 (VCC), U10.16 (VCC); also elsewhere on the board

Notes on the sheet:
Decoupling capacitors
The Arduino is programmed to shift bits in and out of the shift registers in order to control the right port of the 7024 SRAM.
The inverters ensure the active-low control signals are inactive on reset.

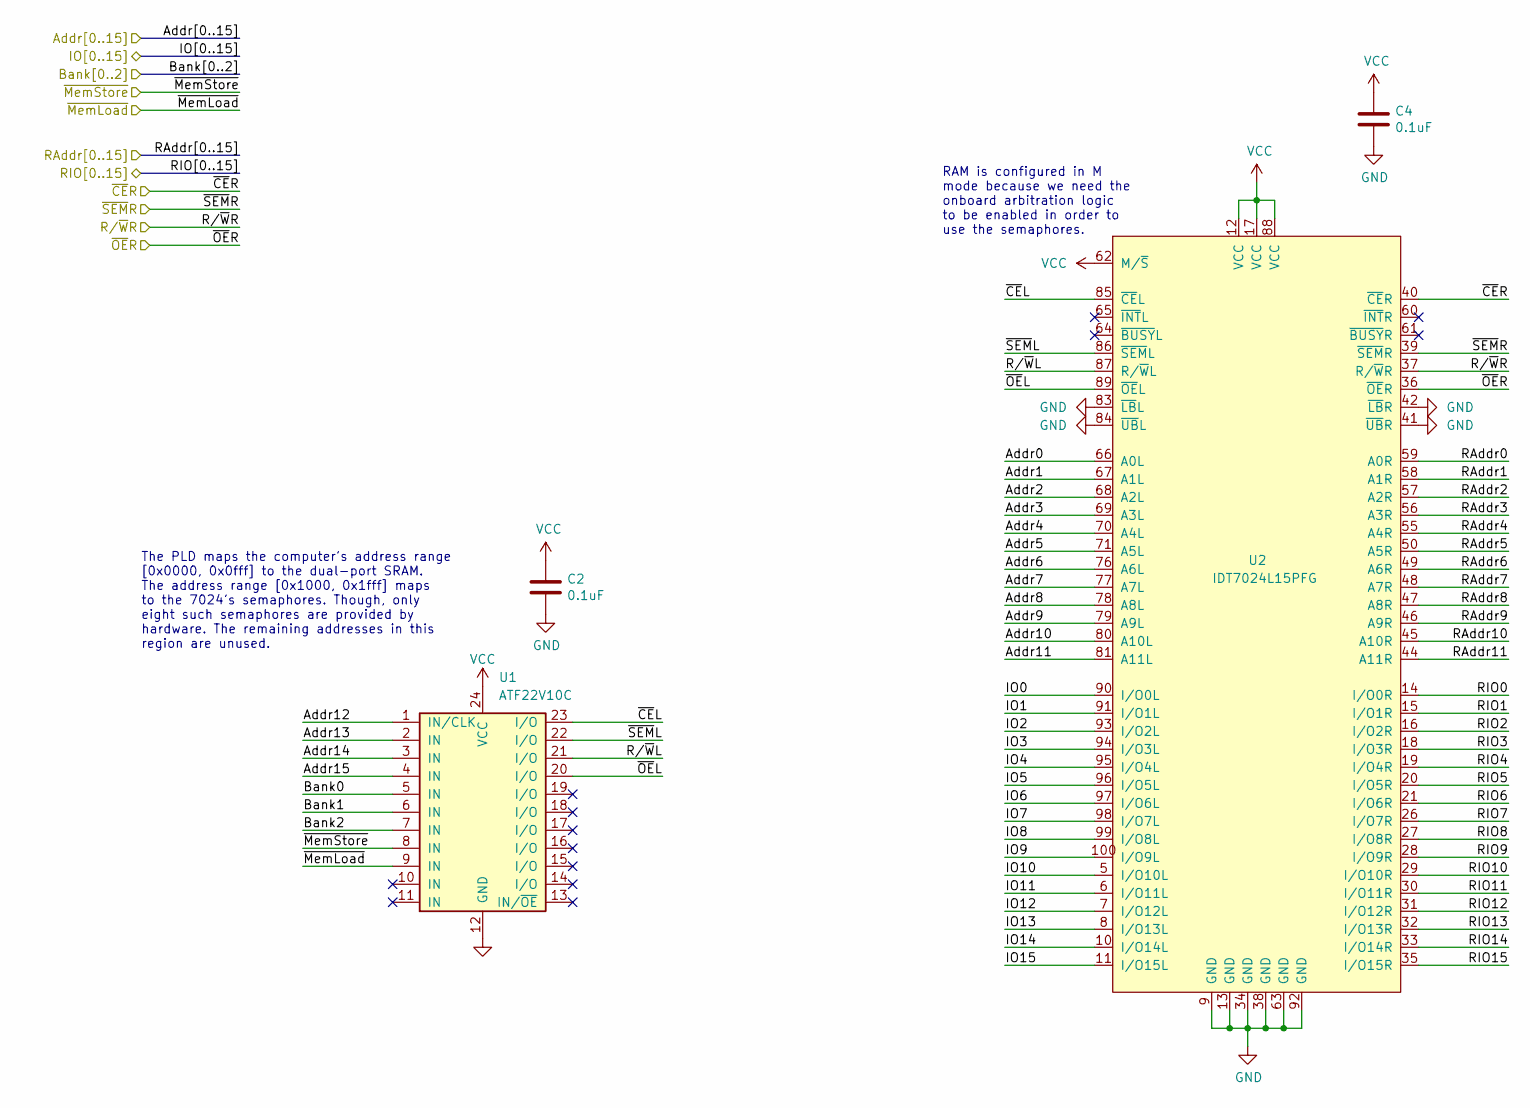
[picture p168: schematic RAM.kicad_sch, Shared Memory]

Parts:
C2, C4: 0.1uF; C_0603_1608Metric; Manufacturer# EMK107B7104KAHT; Mouser# 963-EMK107B7104KAHT
U1: ATF22V10C; DIP-24_W7.62mm_Socket; Manufacturer# ATF22V10C-7PX; Mouser# 556-AF22V10C7PX
U2: IDT7024L15PFG; TQFP-100_14x14mm_P0.5mm; Manufacturer# 7024L15PFG; Mouser# 972-7024L15PFG

Connections:
/ArduinoInterface/RAddr0: U2.59 (A0R); also elsewhere on the board
/ArduinoInterface/RAddr1: U2.58 (A1R); also elsewhere on the board
/ArduinoInterface/RAddr2: U2.57 (A2R); also elsewhere on the board
/ArduinoInterface/RAddr3: U2.56 (A3R); also elsewhere on the board
/ArduinoInterface/RAddr4: U2.55 (A4R); also elsewhere on the board
/ArduinoInterface/RAddr5: U2.50 (A5R); also elsewhere on the board
/ArduinoInterface/RAddr6: U2.49 (A6R); also elsewhere on the board
/ArduinoInterface/RAddr7: U2.48 (A7R); also elsewhere on the board
/ArduinoInterface/RAddr8: U2.47 (A8R); also elsewhere on the board
/ArduinoInterface/RAddr9: U2.46 (A9R); also elsewhere on the board
/ArduinoInterface/RAddr10: U2.45 (A10R); also elsewhere on the board
/ArduinoInterface/RAddr11: U2.44 (A11R); also elsewhere on the board
/ArduinoInterface/RIO0: U2.14 (I/O0R); also elsewhere on the board
/ArduinoInterface/RIO1: U2.15 (I/O1R); also elsewhere on the board
/ArduinoInterface/RIO2: U2.16 (I/O2R); also elsewhere on the board
/ArduinoInterface/RIO3: U2.18 (I/O3R); also elsewhere on the board
/ArduinoInterface/RIO4: U2.19 (I/O4R); also elsewhere on the board
/ArduinoInterface/RIO5: U2.20 (I/O5R); also elsewhere on the board
/ArduinoInterface/RIO6: U2.21 (I/O6R); also elsewhere on the board
/ArduinoInterface/RIO7: U2.26 (I/O7R); also elsewhere on the board
/ArduinoInterface/RIO8: U2.27 (I/O8R); also elsewhere on the board
/ArduinoInterface/RIO9: U2.28 (I/O9R); also elsewhere on the board
/ArduinoInterface/RIO10: U2.29 (I/O10R); also elsewhere on the board
/ArduinoInterface/RIO11: U2.30 (I/O11R); also elsewhere on the board
/ArduinoInterface/RIO12: U2.31 (I/O12R); also elsewhere on the board
/ArduinoInterface/RIO13: U2.32 (I/O13R); also elsewhere on the board
/ArduinoInterface/RIO14: U2.33 (I/O14R); also elsewhere on the board
/ArduinoInterface/RIO15: U2.35 (I/O15R); also elsewhere on the board
/ArduinoInterface/R/~WR: U2.37 (R/~WR); also elsewhere on the board
/ArduinoInterface/~CER: U2.40 (~CER); also elsewhere on the board
/ArduinoInterface/~OER: U2.36 (~OER); also elsewhere on the board
/ArduinoInterface/~SEMR: U2.39 (~SEMR); also elsewhere on the board
/RAM/Addr0: U2.66 (A0L); also elsewhere on the board
/RAM/Addr1: U2.67 (A1L); also elsewhere on the board
/RAM/Addr2: U2.68 (A2L); also elsewhere on the board
/RAM/Addr3: U2.69 (A3L); also elsewhere on the board
/RAM/Addr4: U2.70 (A4L); also elsewhere on the board
/RAM/Addr5: U2.71 (A5L); also elsewhere on the board
/RAM/Addr6: U2.76 (A6L); also elsewhere on the board
/RAM/Addr7: U2.77 (A7L); also elsewhere on the board
/RAM/Addr8: U2.78 (A8L); also elsewhere on the board
/RAM/Addr9: U2.79 (A9L); also elsewhere on the board
/RAM/Addr10: U2.80 (A10L); also elsewhere on the board
/RAM/Addr11: U2.81 (A11L); also elsewhere on the board
/RAM/Addr12: U1.1 (IN/CLK); also elsewhere on the board
/RAM/Addr13: U1.2 (IN); also elsewhere on the board
/RAM/Addr14: U1.3 (IN); also elsewhere on the board
/RAM/Addr15: U1.4 (IN); also elsewhere on the board
/RAM/Bank0: U1.5 (IN); also elsewhere on the board
/RAM/Bank1: U1.6 (IN); also elsewhere on the board
/RAM/Bank2: U1.7 (IN); also elsewhere on the board
/RAM/IO0: U2.90 (I/O0L); also elsewhere on the board
/RAM/IO1: U2.91 (I/O1L); also elsewhere on the board
/RAM/IO2: U2.93 (I/O2L); also elsewhere on the board
/RAM/IO3: U2.94 (I/O3L); also elsewhere on the board
/RAM/IO4: U2.95 (I/O4L); also elsewhere on the board
/RAM/IO5: U2.96 (I/O5L); also elsewhere on the board
/RAM/IO6: U2.97 (I/O6L); also elsewhere on the board
/RAM/IO7: U2.98 (I/O7L); also elsewhere on the board
/RAM/IO8: U2.99 (I/O8L); also elsewhere on the board
/RAM/IO9: U2.100 (I/O9L); also elsewhere on the board
/RAM/IO10: U2.5 (I/O10L); also elsewhere on the board
/RAM/IO11: U2.6 (I/O11L); also elsewhere on the board
/RAM/IO12: U2.7 (I/O12L); also elsewhere on the board
/RAM/IO13: U2.8 (I/O13L); also elsewhere on the board
/RAM/IO14: U2.10 (I/O14L); also elsewhere on the board
/RAM/IO15: U2.11 (I/O15L); also elsewhere on the board
/RAM/R/~WL: U1.21 (I/O), U2.87 (R/~WL)
/RAM/~CEL: U1.23 (I/O), U2.85 (~CEL)
/RAM/~MemLoad: U1.9 (IN); also elsewhere on the board
/RAM/~MemStore: U1.8 (IN); also elsewhere on the board
/RAM/~OEL: U1.20 (I/O), U2.89 (~OEL)
/RAM/~SEML: U1.22 (I/O), U2.86 (~SEML)
GND: C2.2, C4.2, U1.12 (GND), U2.9 (GND), U2.13 (GND), U2.34 (GND), U2.38 (GND), U2.41 (~UBR), U2.42 (~LBR), U2.63 (GND), U2.83 (~LBL), U2.84 (~UBL), U2.92 (GND); also elsewhere on the board
VCC: C2.1, C4.1, U1.24 (VCC), U2.12 (VCC), U2.17 (VCC), U2.62 (M/~S), U2.88 (VCC); also elsewhere on the board

Notes on the sheet:
The PLD maps the computer's address range [0x0000, 0x0fff] to the dual-port SRAM. The address range [0x1000, 0x1fff] maps to the 7024's semaphores. Though, only eight such semaphores are provided by hardware. The remaining addresses in this region are unused.
RAM is configured in M mode because we need the onboard arbitration logic to be enabled in order to use the semaphores.

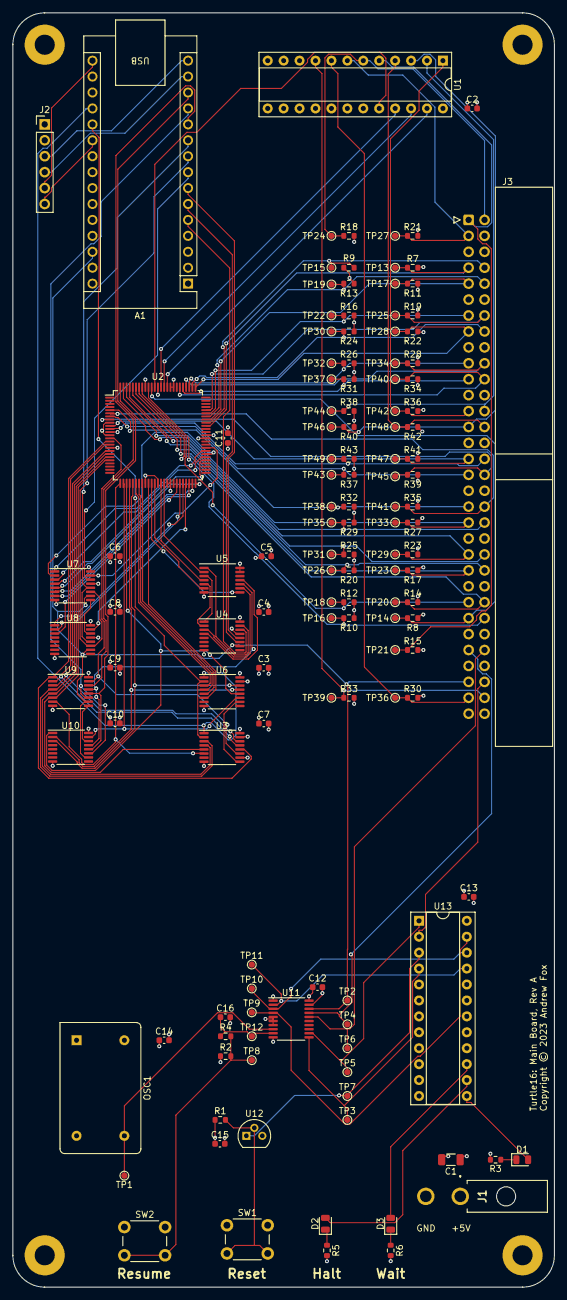
[picture p169: board Hardware/MonolithicProcessor/MainBoard/MainBoard.kicad_pcb from above]

Board: 4 copper layers, 86.4 x 203.2 mm, 135 parts (0 on the bottom side), 119 nets.
