foxostro/Turtle16/Hardware/PrototypeProcessor/ProgramCounterPrototype/ProgramCounterPrototype.kicad_pcb

## KiCad design Hardware/PrototypeProcessor/ProgramCounterPrototype/ProgramCounterPrototype.kicad_pcb (2025-06-30)

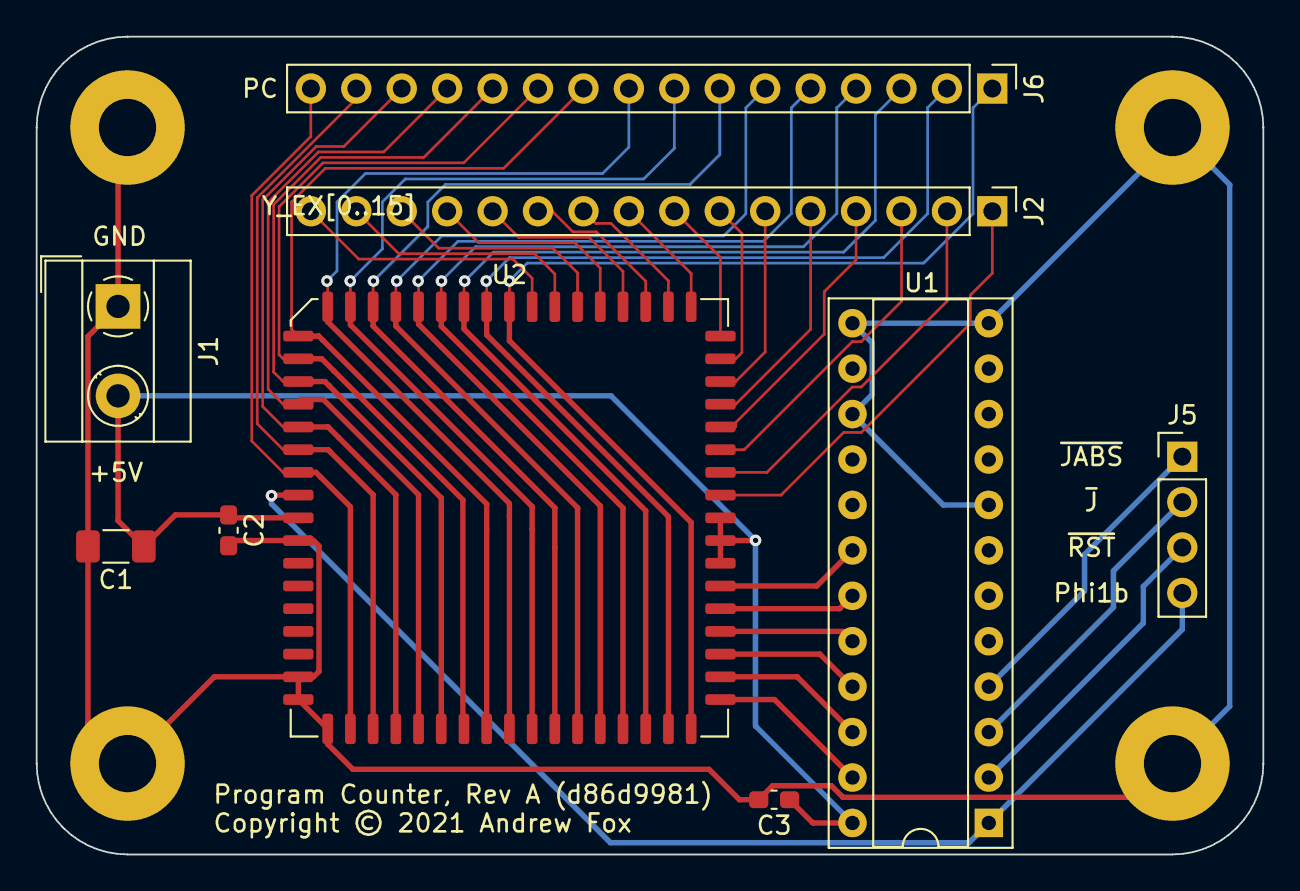
[picture p170: board ProgramCounterPrototype.kicad_pcb from above]

Board: 2 copper layers, 68.6 x 45.7 mm, 13 parts (0 on the bottom side), 44 nets.

Parts:
C1: 100µF; C_1206_3216Metric_Pad1.33x1.80mm_HandSolder
C2, C3: 100nF; C_0603_1608Metric_Pad1.08x0.95mm_HandSolder
H1, H2, H3, H4: MountingHole_Pad; MountingHole_3.2mm_M3_Pad
J1: Screw_Terminal_01x02; TerminalBlock_MetzConnect_Type055_RT01502HDWU_1x02_P5.00mm_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
J2: Y_EX[0..15]; PinHeader_1x16_P2.54mm_Vertical
J5: Ctl; PinHeader_1x04_P2.54mm_Vertical
J6: PC; PinHeader_1x16_P2.54mm_Vertical
U1: ATF22V10C-7PX; DIP-24_W7.62mm_Socket
U2: IDT7381; PLCC-68_24.2x24.2mm_P1.27mm

Connections:
/PC0: J6.1, U2.1, U2.43
/PC1: J6.2, U2.2, U2.42
/PC2: J6.3, U2.3, U2.41
/PC3: J6.4, U2.4, U2.40
/PC4: J6.5, U2.5, U2.39
/PC5: J6.6, U2.6, U2.38
/PC6: J6.7, U2.7, U2.37
/PC7: J6.8, U2.8, U2.36
/PC8: J6.9, U2.9, U2.35
/PC9: J6.10, U2.10, U2.34
/PC10: J6.11, U2.11, U2.33
/PC11: J6.12, U2.12, U2.32
/PC12: J6.13, U2.13, U2.31
/PC13: J6.14, U2.14, U2.30
/PC14: J6.15, U2.15, U2.29
/PC15: J6.16, U2.16, U2.28
/Y_EX0: J2.1, U2.53
/Y_EX1: J2.2, U2.54
/Y_EX2: J2.3, U2.55
/Y_EX3: J2.4, U2.56
/Y_EX4: J2.5, U2.57
/Y_EX5: J2.6, U2.58
/Y_EX6: J2.7, U2.59
/Y_EX7: J2.8, U2.60
/Y_EX8: J2.9, U2.61
/Y_EX9: J2.10, U2.62
/Y_EX10: J2.11, U2.63
/Y_EX11: J2.12, U2.64
/Y_EX12: J2.13, U2.65
/Y_EX13: J2.14, U2.66
/Y_EX14: J2.15, U2.67
/Y_EX15: J2.16, U2.68
/sheet606491AF/~JABS: J5.1, U1.4
/sheet606491AF/~J: J5.2, U1.3
/sheet606491AF/~RST: J5.3, U1.2
GND: C1.2, C2.2, C3.2, H1.1, H2.1, H3.1, H4.1, J1.1, U1.8, U1.12, U1.13, U1.15, U2.19, U2.25, U2.26, U2.27
unnamed: U1.18, U2.49
unnamed: U1.19, U2.48
unnamed: U1.20, U2.47
unnamed: U1.21, U2.46
unnamed: U1.22, U2.45
unnamed: U1.23, U2.44
Phi1b: J5.4, U1.1, U2.17
VCC: C1.1, C2.1, C3.1, J1.2, U1.24, U2.18, U2.50, U2.51, U2.52
